JiajunGuo1027/Soft-Glove-Dissertation/data/raw/flex_sensor/ind0/plot_sensors_20250812_154303.png

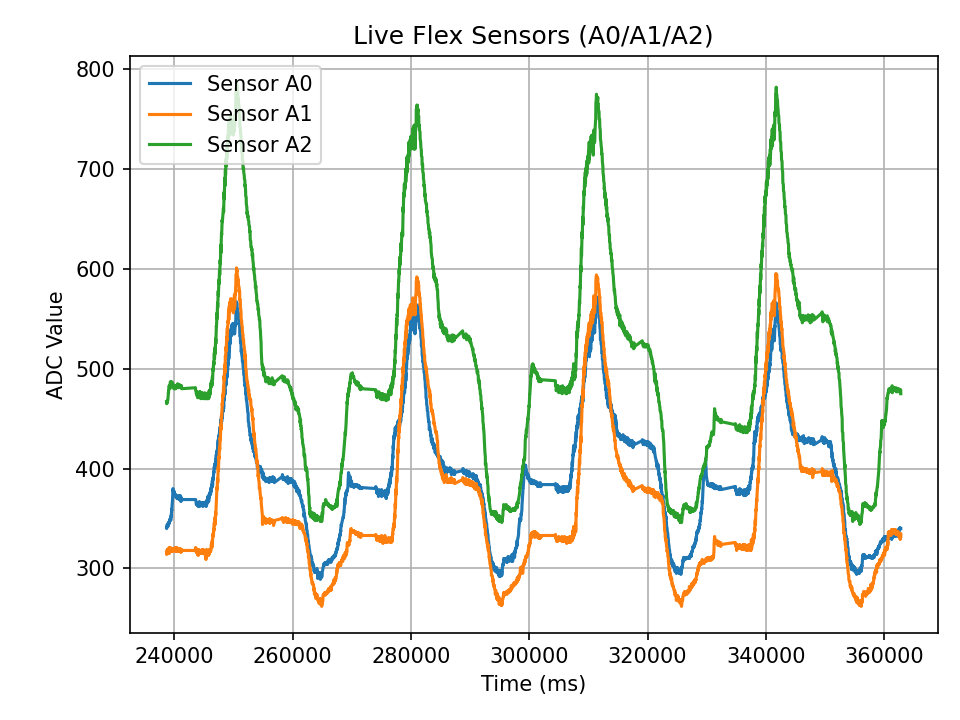
data/raw/flex_sensor/ind0/plot_sensors_20250812_154303.png
