JiajunGuo1027/Soft-Glove-Dissertation/data/raw/flex_sensor/ind1/plot_sensors_full_20250812_160008.png

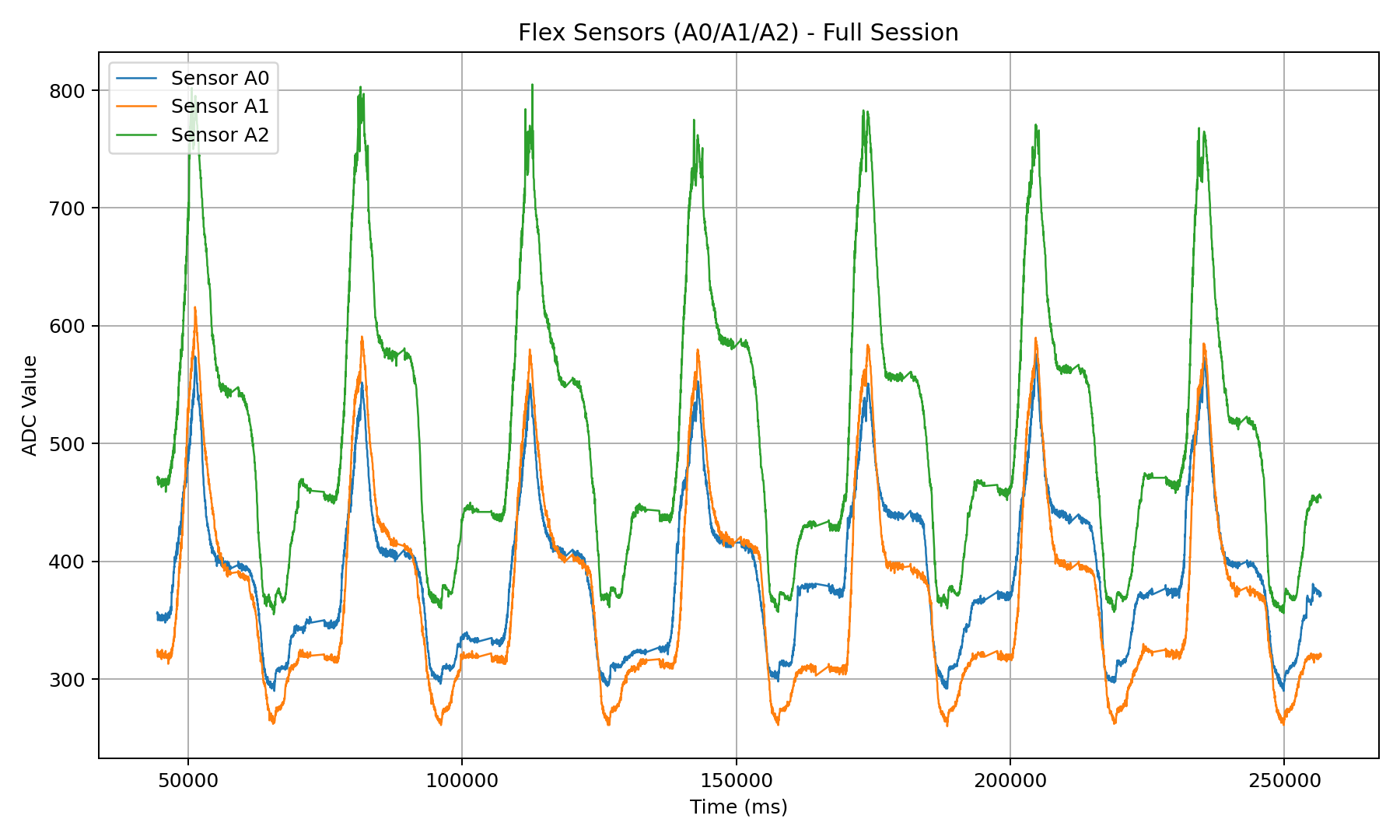
data/raw/flex_sensor/ind1/plot_sensors_full_20250812_160008.png
