JiajunGuo1027/Soft-Glove-Dissertation/data/raw/flex_sensor/ind2/plot_motors_20250812_160704.png

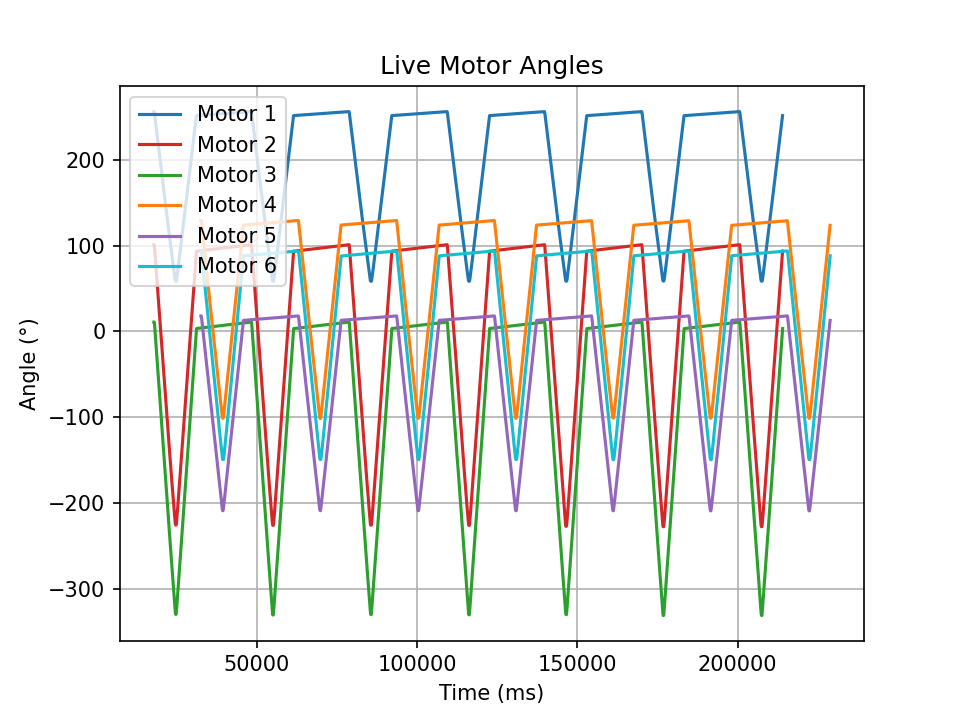
data/raw/flex_sensor/ind2/plot_motors_20250812_160704.png
