JiajunGuo1027/Soft-Glove-Dissertation/data/raw/flex_sensor/mid1/plot_sensors_20250812_162041.png

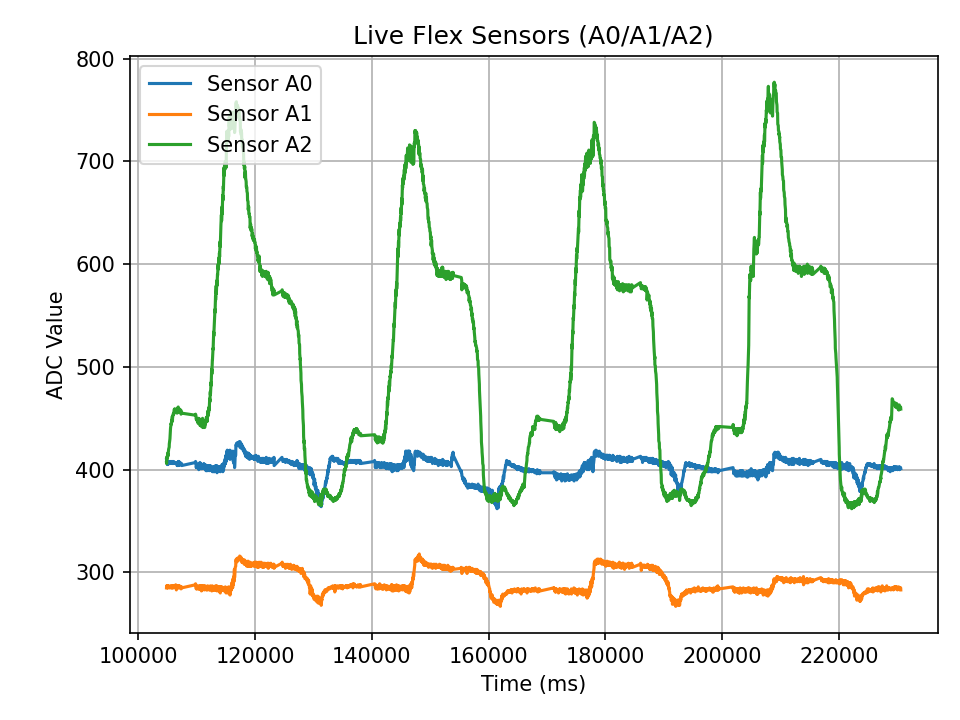
data/raw/flex_sensor/mid1/plot_sensors_20250812_162041.png
