JiajunGuo1027/Soft-Glove-Dissertation/data/raw/flex_sensor/mid2/plot_sensors_full_20250812_163051.png

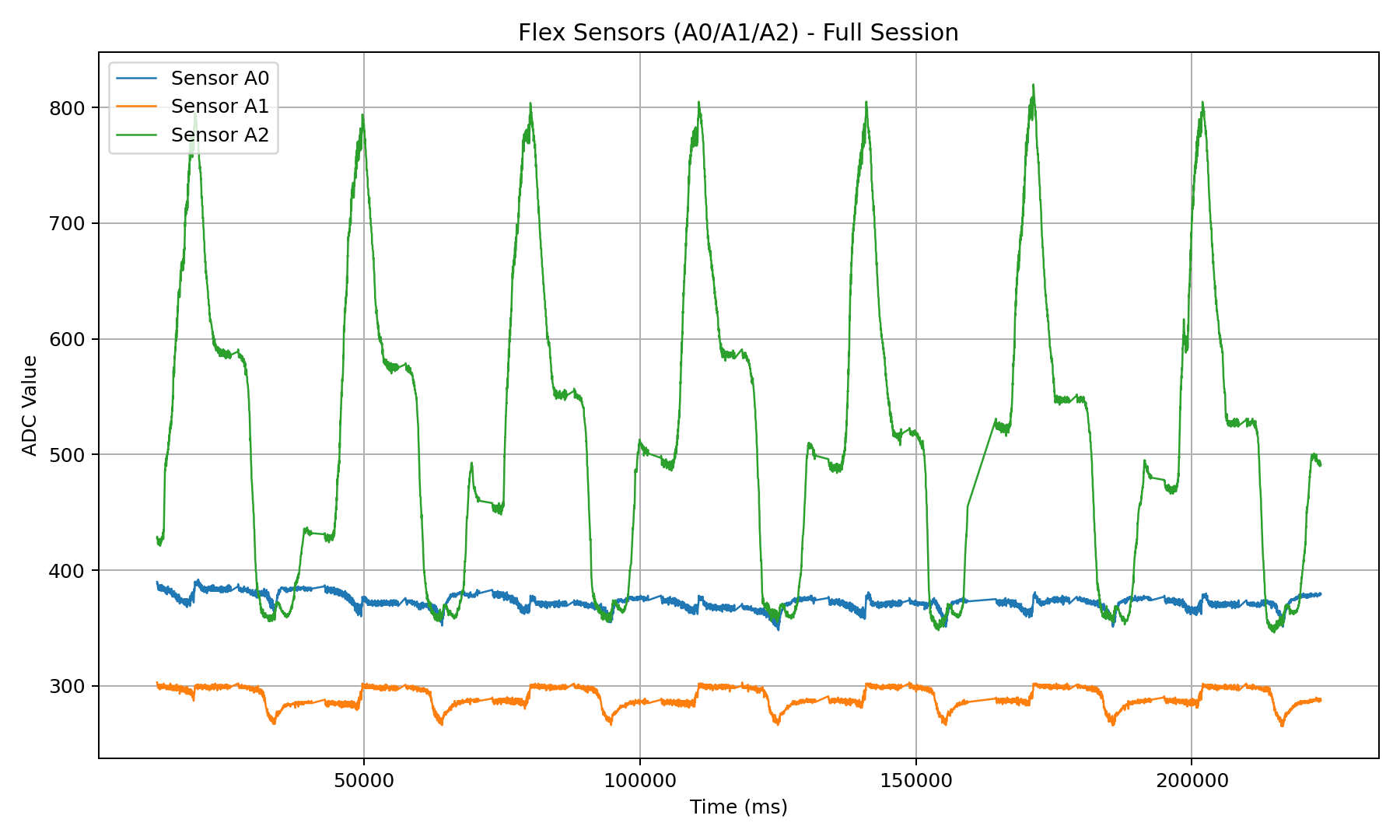
data/raw/flex_sensor/mid2/plot_sensors_full_20250812_163051.png
