JiajunGuo1027/Soft-Glove-Dissertation/data/raw/flex_sensor/plot_sensors_20250809_205605.png

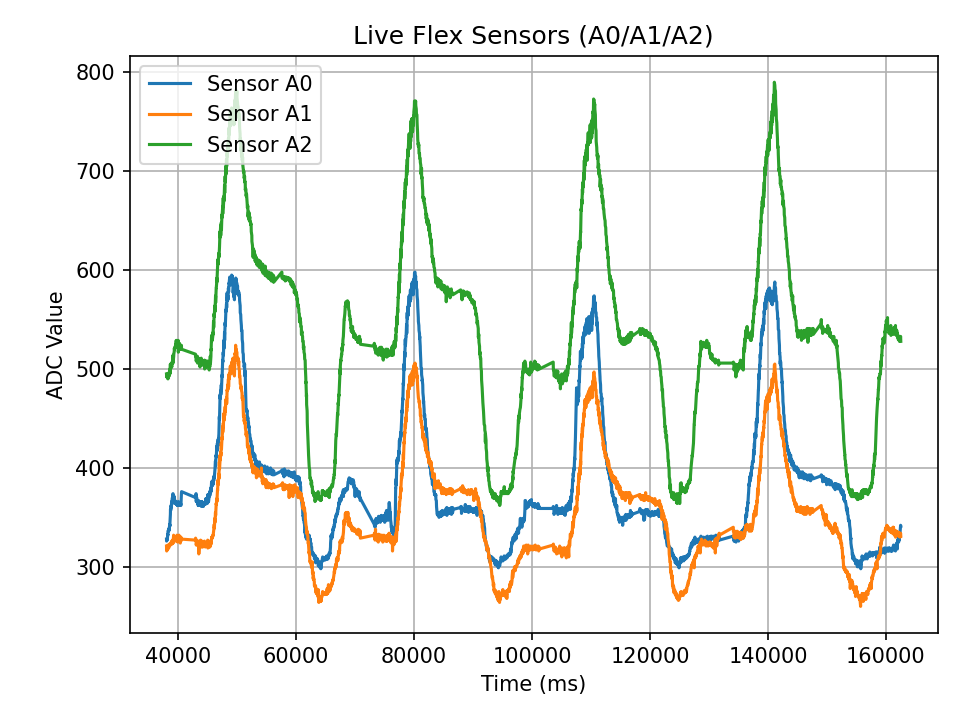
data/raw/flex_sensor/plot_sensors_20250809_205605.png
