JiajunGuo1027/Soft-Glove-Dissertation/data/raw/flex_sensor/plot_sensors_20250809_210135.png

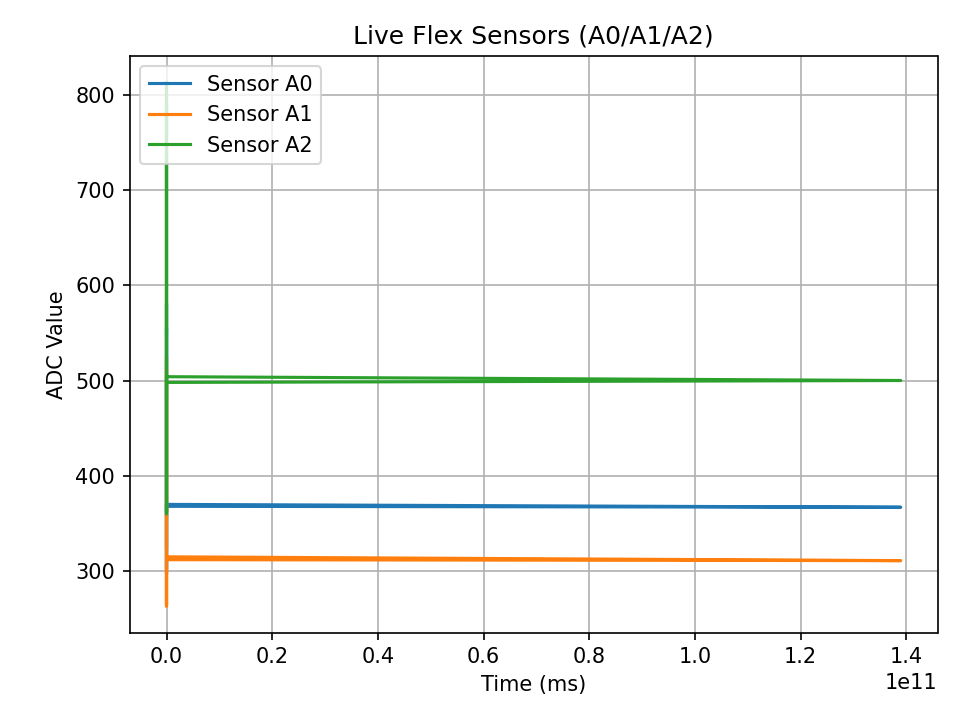
data/raw/flex_sensor/plot_sensors_20250809_210135.png
