JiajunGuo1027/Soft-Glove-Dissertation/data/raw/flex_sensor/thu1/plot_sensors_full_20250812_171734.png

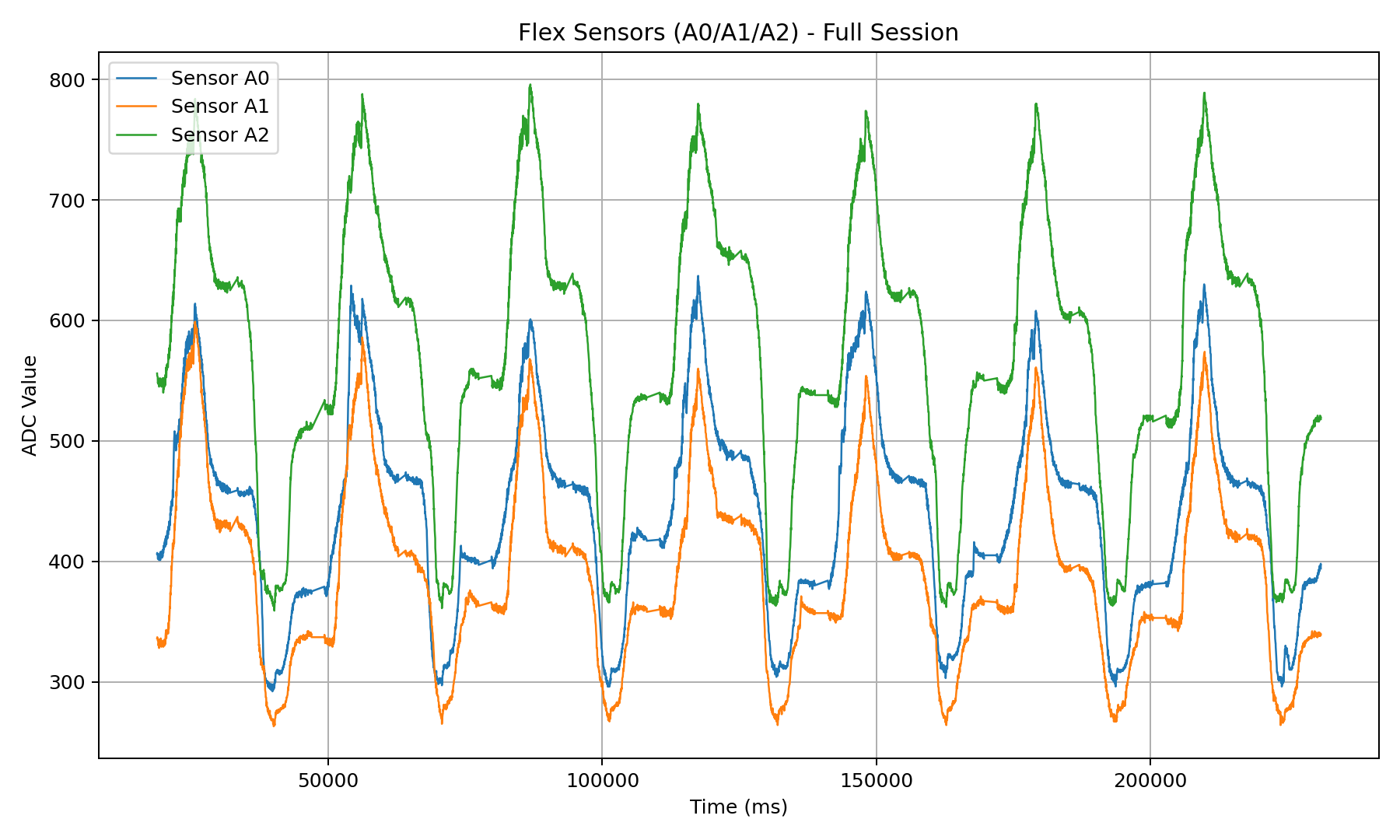
data/raw/flex_sensor/thu1/plot_sensors_full_20250812_171734.png
