JiajunGuo1027/Soft-Glove-Dissertation/data/raw/flex_sensor/thu2/plot_sensors_20250812_172157.png

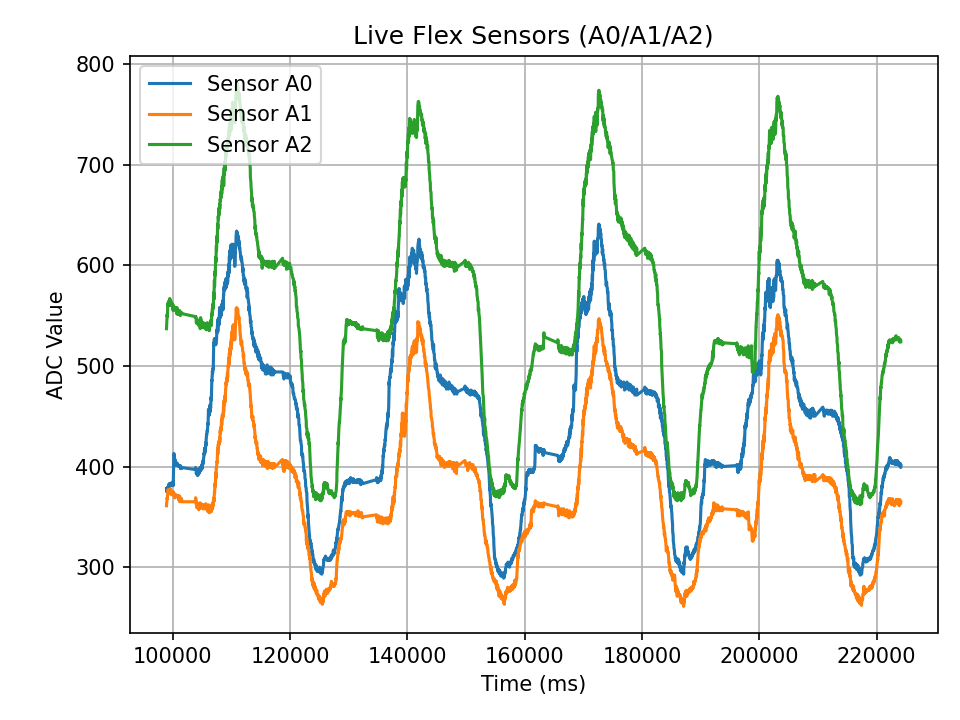
data/raw/flex_sensor/thu2/plot_sensors_20250812_172157.png
