JiajunGuo1027/Soft-Glove-Dissertation/data/raw/Index/0/Figure_ind0.png

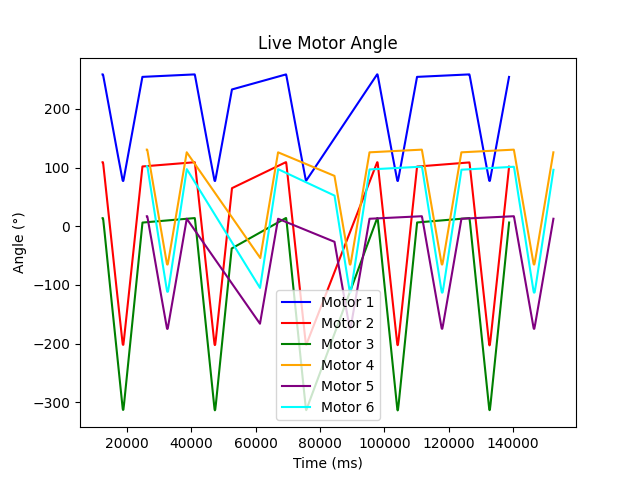
data/raw/Index/0/Figure_ind0.png
