JiajunGuo1027/Soft-Glove-Dissertation/data/raw/Index/0/Figure_ind01.png

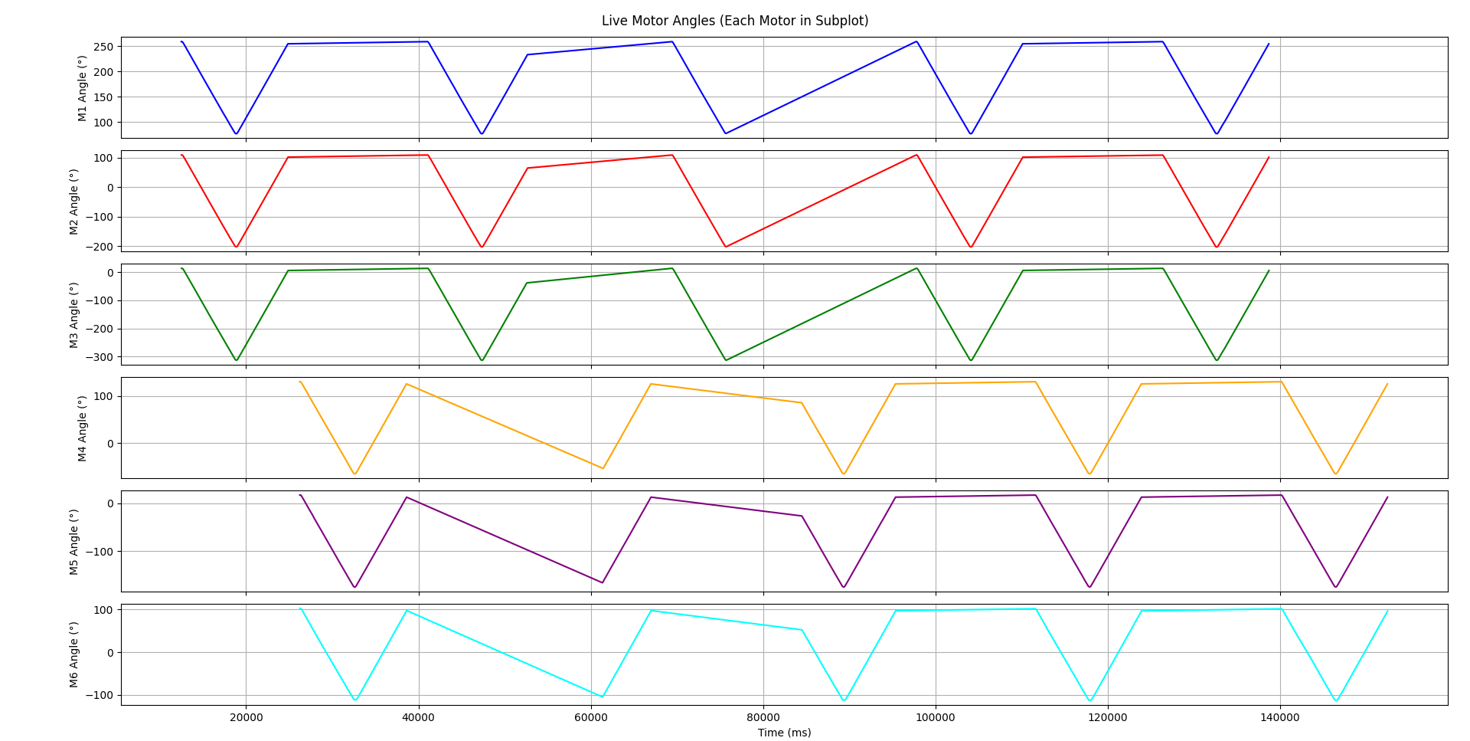
data/raw/Index/0/Figure_ind01.png
