JiajunGuo1027/Soft-Glove-Dissertation/data/raw/Index/2/Figure_ind2.png

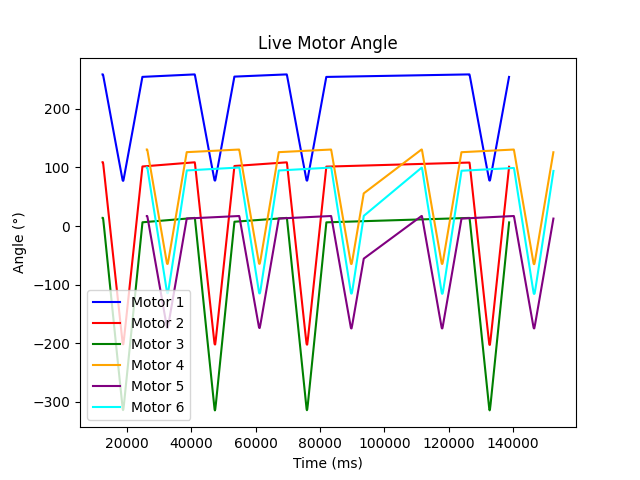
data/raw/Index/2/Figure_ind2.png
