JiajunGuo1027/Soft-Glove-Dissertation/data/raw/Index/2/Figure_ind21.png

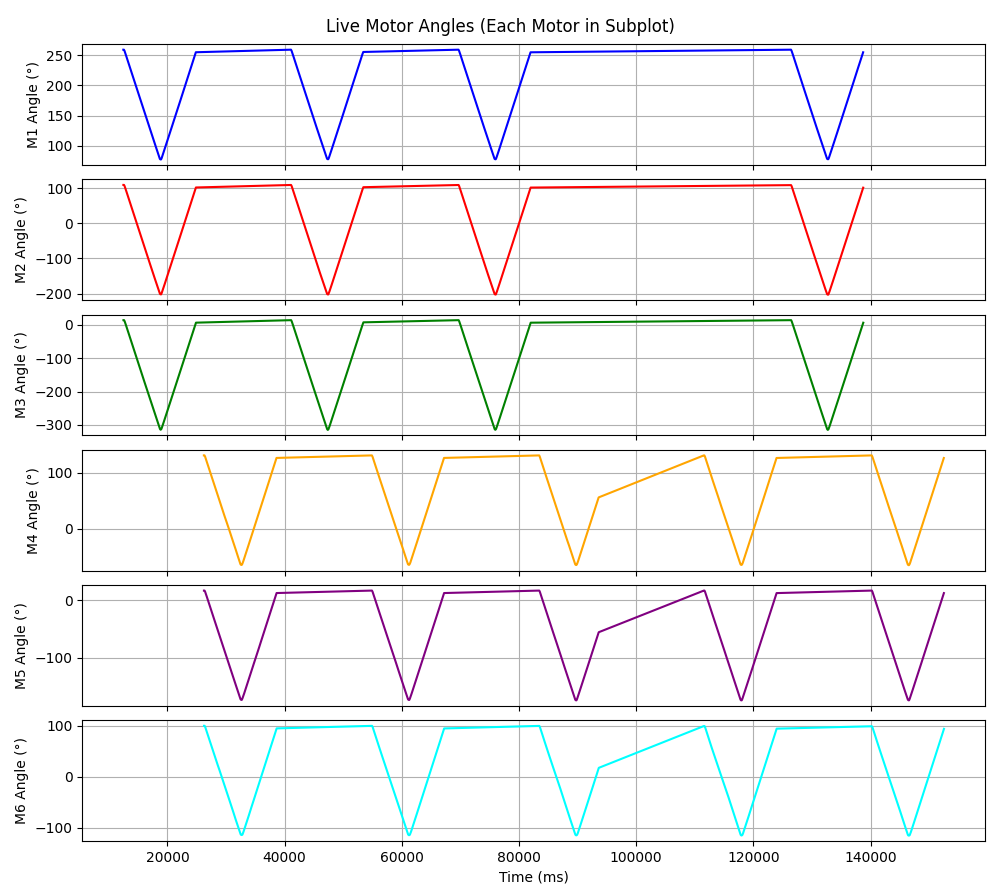
data/raw/Index/2/Figure_ind21.png
