JiajunGuo1027/Soft-Glove-Dissertation/data/raw/Middle/1/Figure_mid1.png

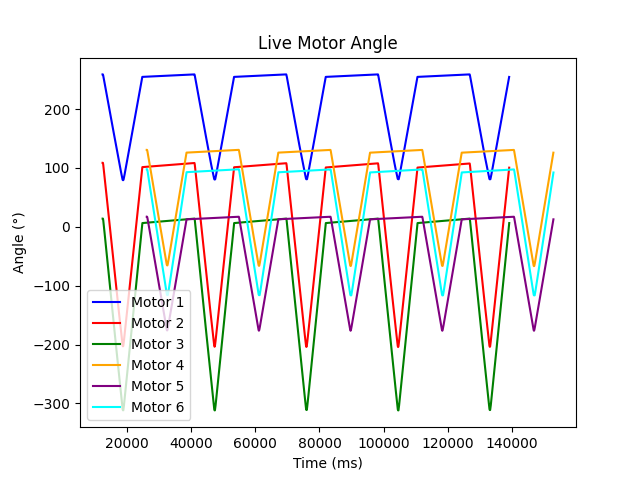
data/raw/Middle/1/Figure_mid1.png
