JiajunGuo1027/Soft-Glove-Dissertation/data/raw/Middle/2/Figure_mid2.png

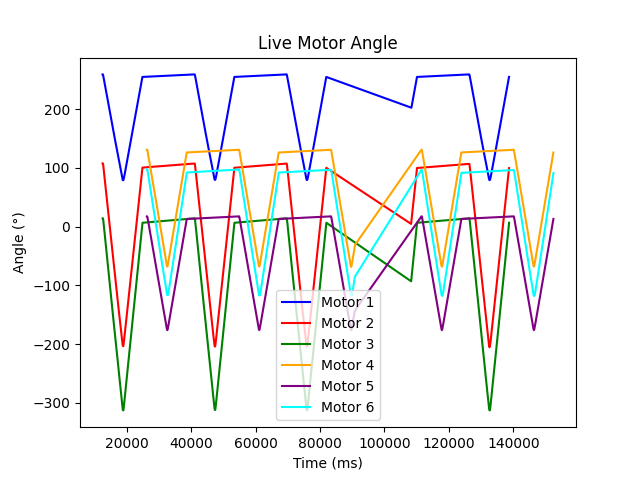
data/raw/Middle/2/Figure_mid2.png
