JiajunGuo1027/Soft-Glove-Dissertation/data/raw/Middle/2/Figure_mid21.png

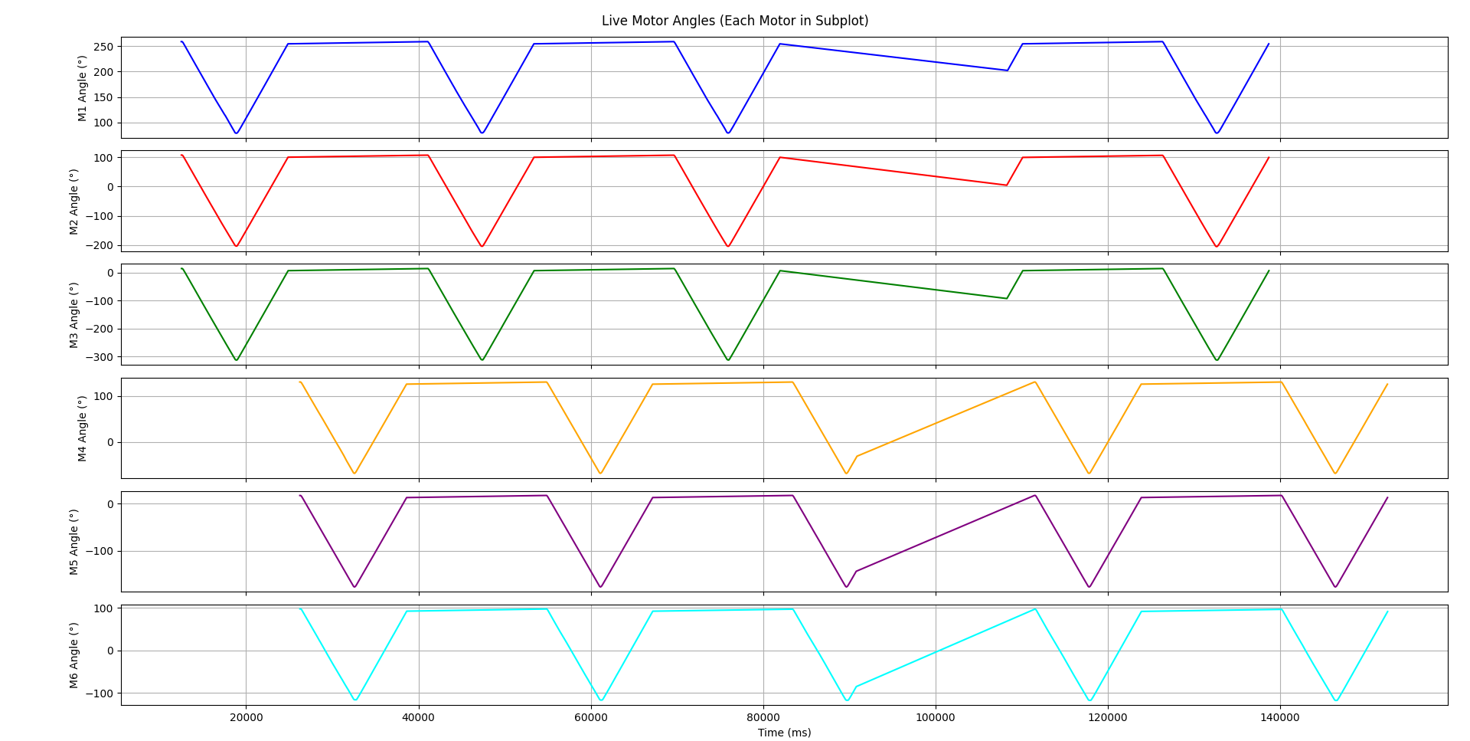
data/raw/Middle/2/Figure_mid21.png
