JiajunGuo1027/Soft-Glove-Dissertation/data/raw/Thumb/1/Figure_thu11.png

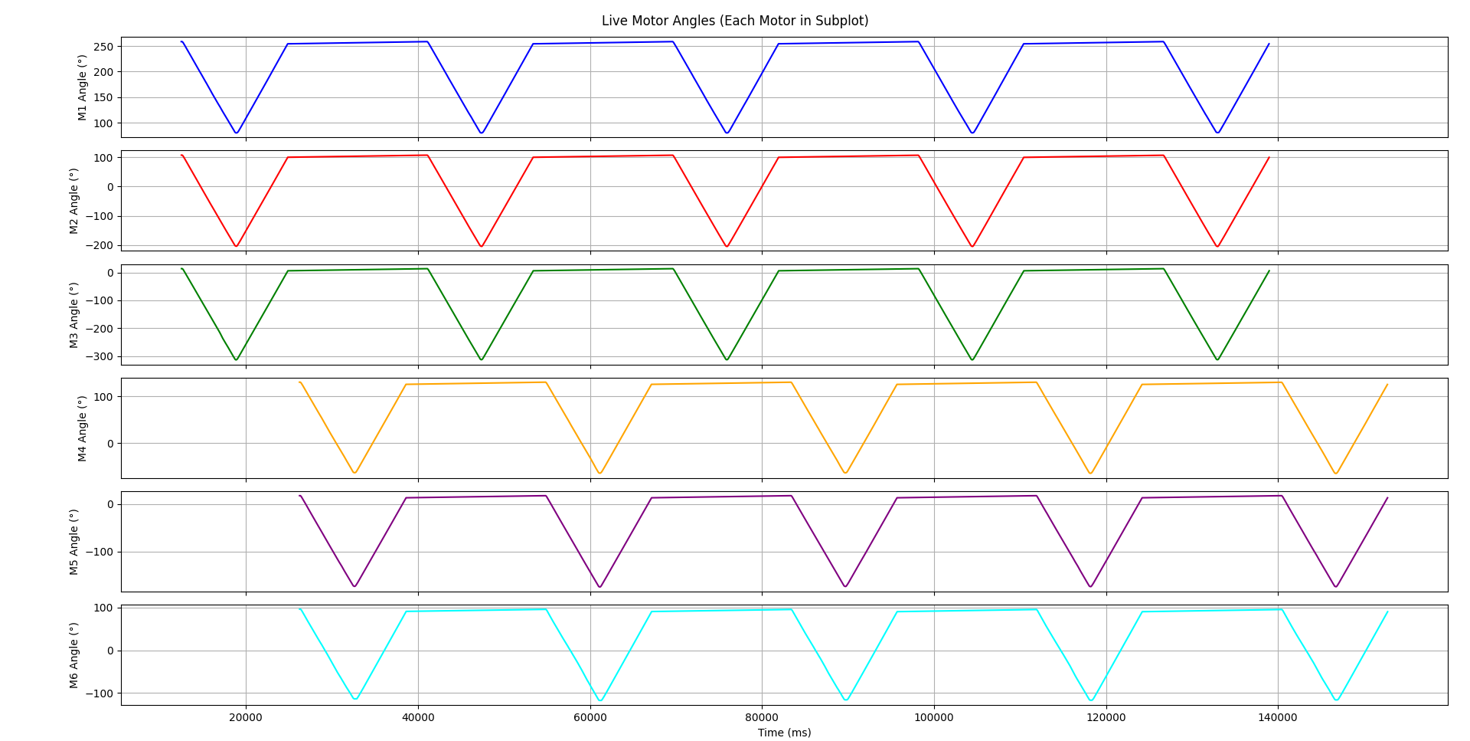
data/raw/Thumb/1/Figure_thu11.png
