JiajunGuo1027/Soft-Glove-Dissertation/data/raw/Thumb/2/Figure_thu2.png

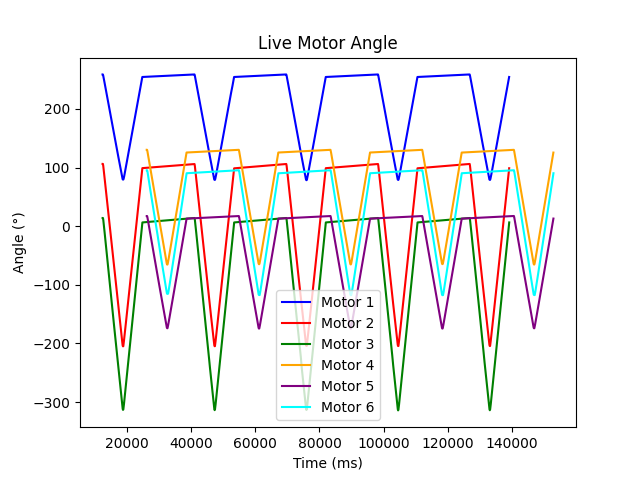
data/raw/Thumb/2/Figure_thu2.png
