JiajunGuo1027/Soft-Glove-Dissertation/images/article/aluminum.jpg

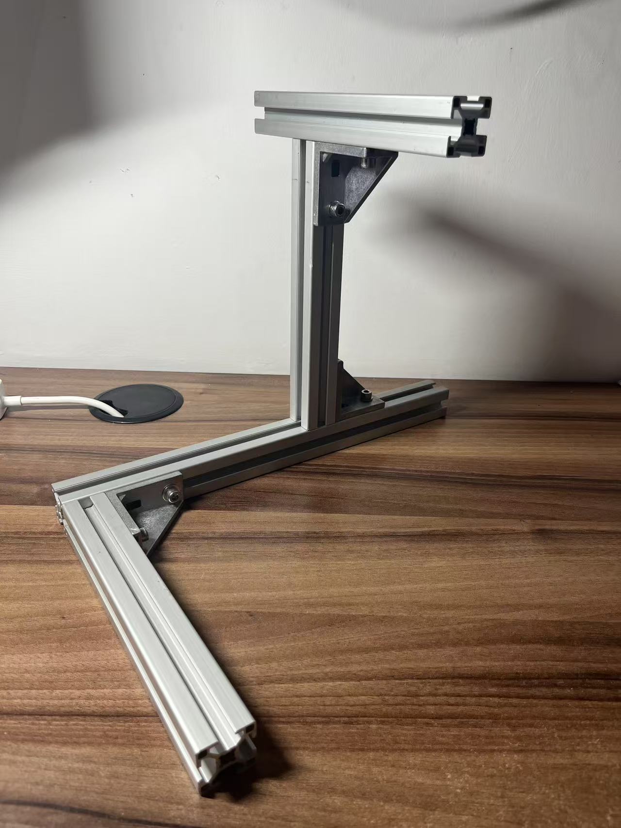
images/article/aluminum.jpg
