JiajunGuo1027/Soft-Glove-Dissertation/images/article/anagle_detect.jpg

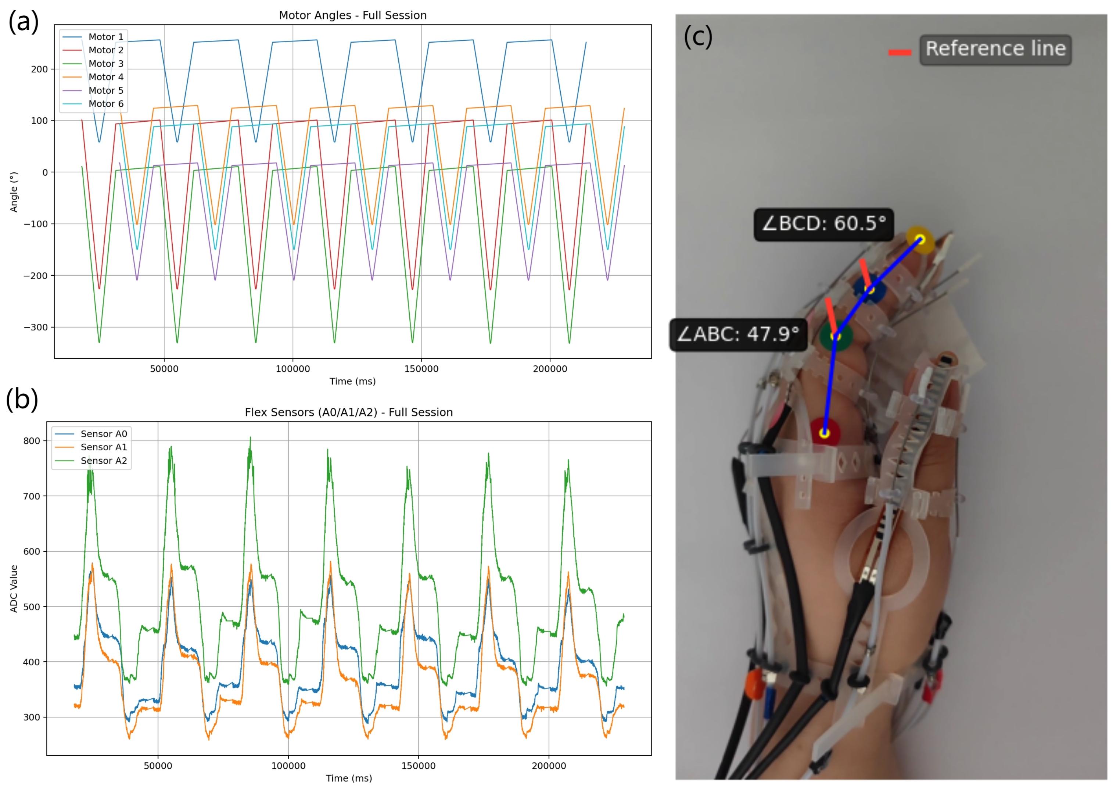
images/article/anagle_detect.jpg
