JiajunGuo1027/Soft-Glove-Dissertation/images/article/cable_connector.png

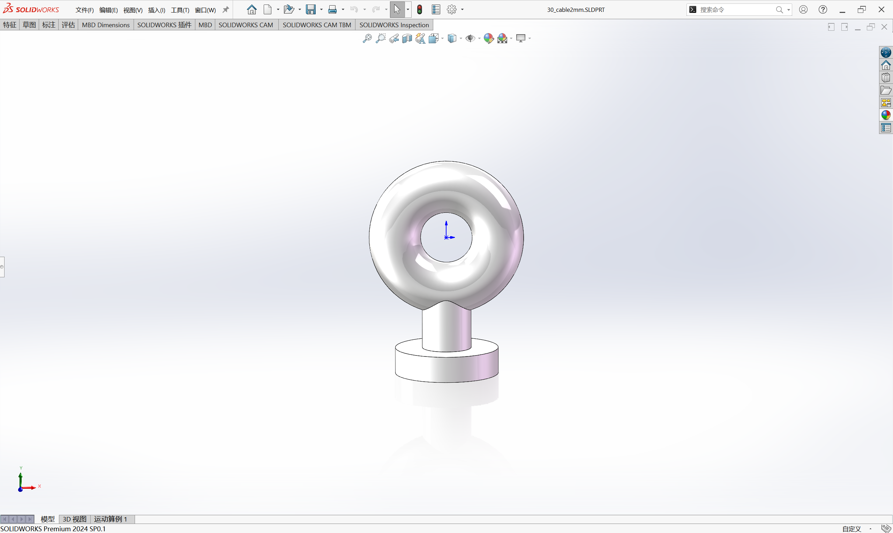
images/article/cable_connector.png
