JiajunGuo1027/Soft-Glove-Dissertation/images/article/connector.png

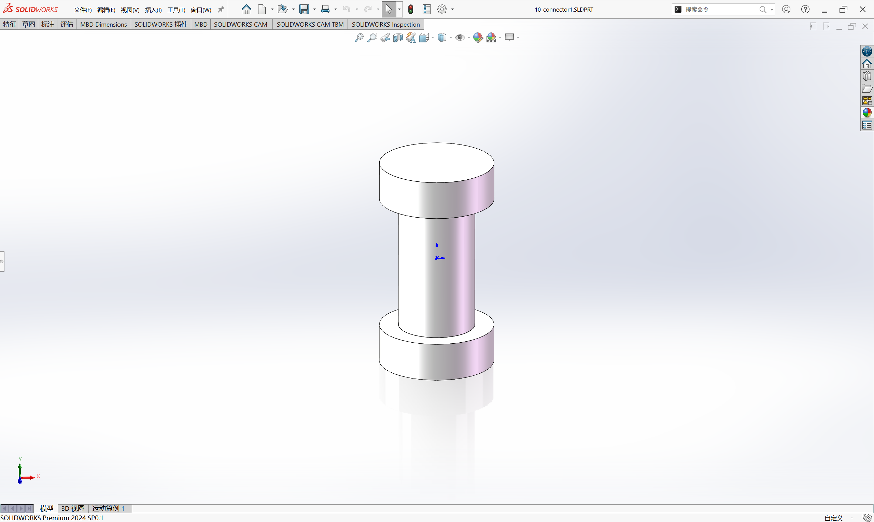
images/article/connector.png
