JiajunGuo1027/Soft-Glove-Dissertation/images/article/control_flowchart1.png

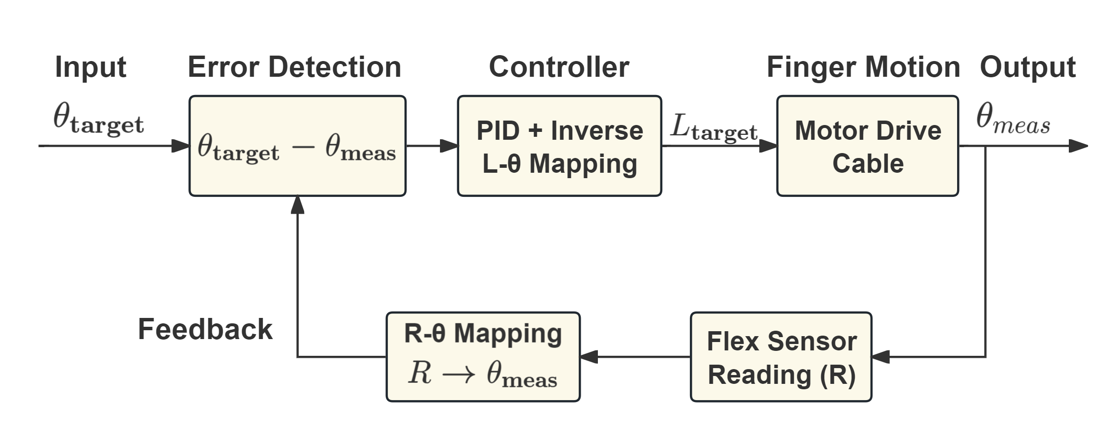
images/article/control_flowchart1.png
