JiajunGuo1027/Soft-Glove-Dissertation/images/article/control_flowchart.png

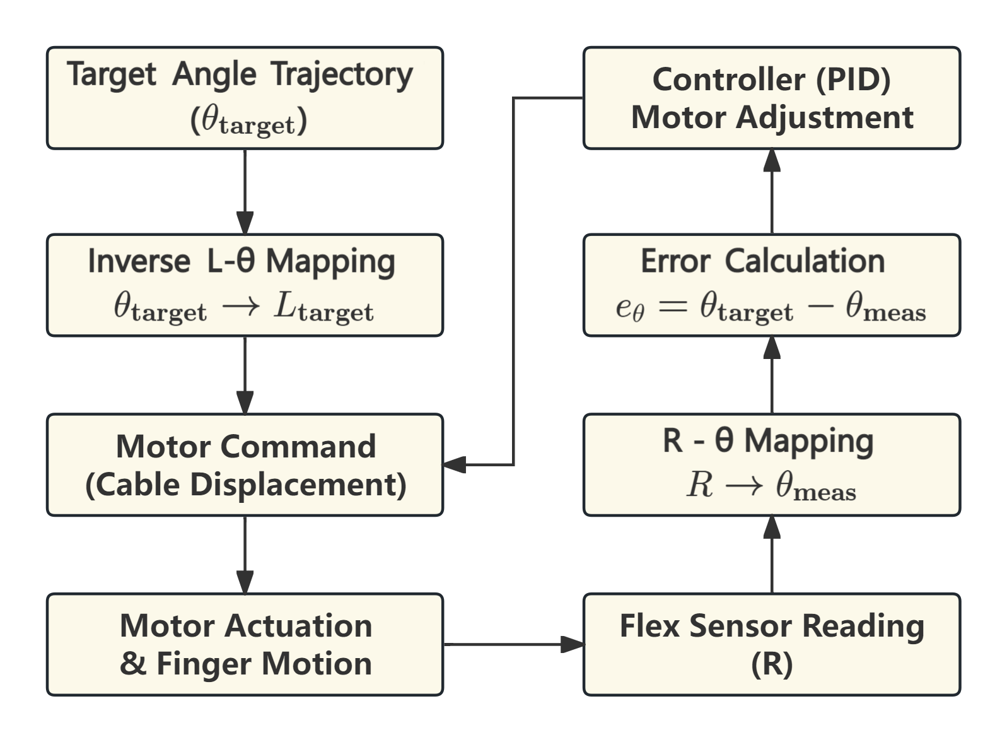
images/article/control_flowchart.png
