JiajunGuo1027/Soft-Glove-Dissertation/images/article/finger_lower.png

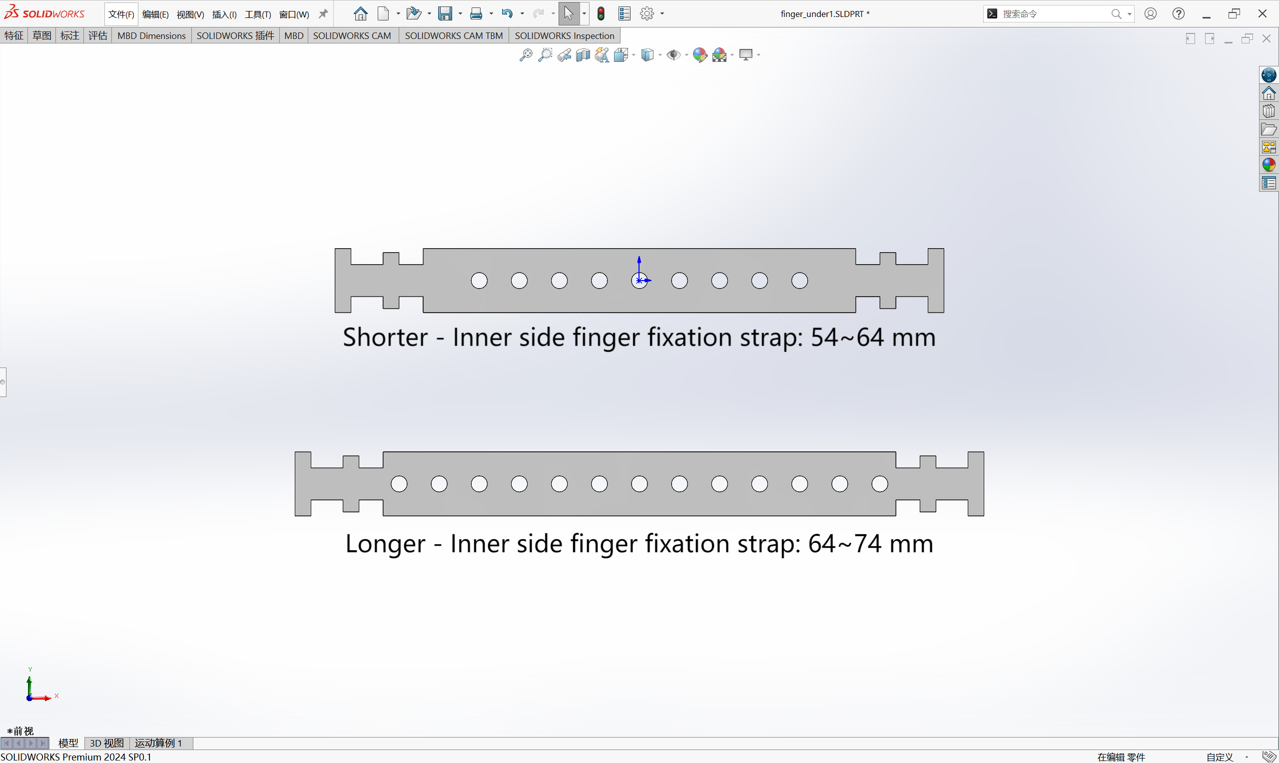
images/article/finger_lower.png
