JiajunGuo1027/Soft-Glove-Dissertation/images/article/finger_lower_sketch1.png

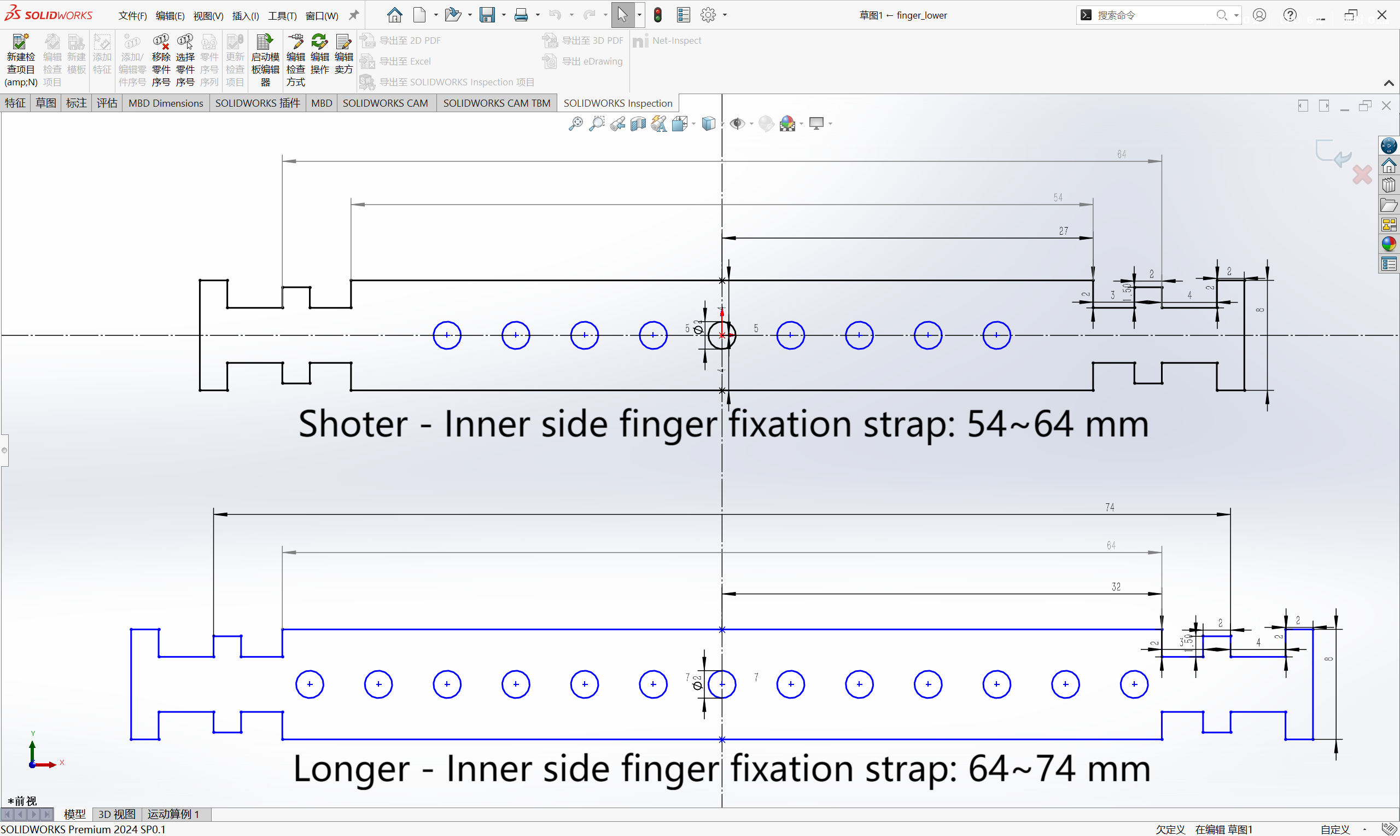
images/article/finger_lower_sketch1.png
