JiajunGuo1027/Soft-Glove-Dissertation/images/article/fingers_design.jpg

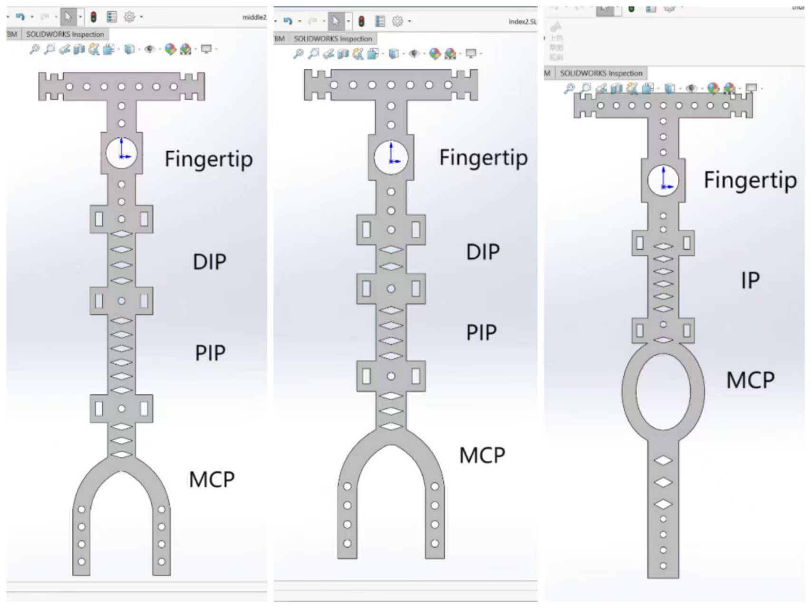
images/article/fingers_design.jpg
