JiajunGuo1027/Soft-Glove-Dissertation/images/article/glove_connector.jpg

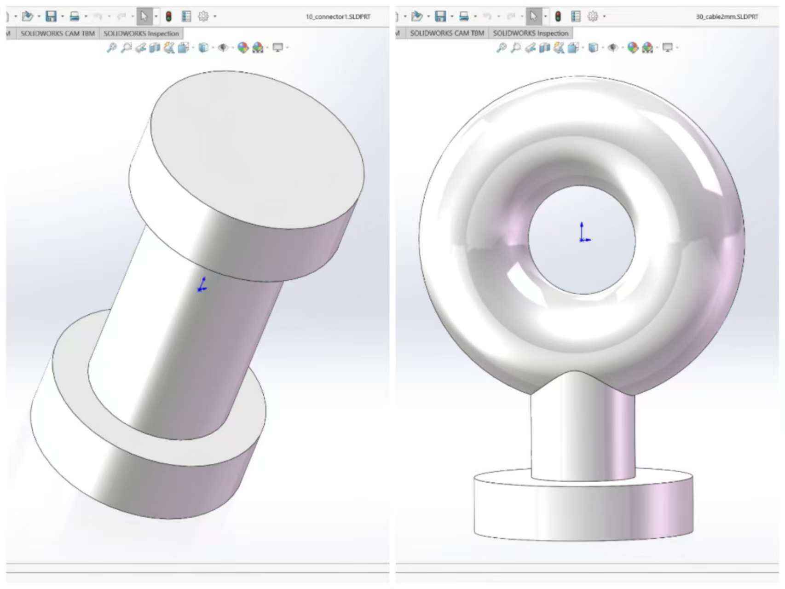
images/article/glove_connector.jpg
