JiajunGuo1027/Soft-Glove-Dissertation/images/article/glove_wearing.jpg

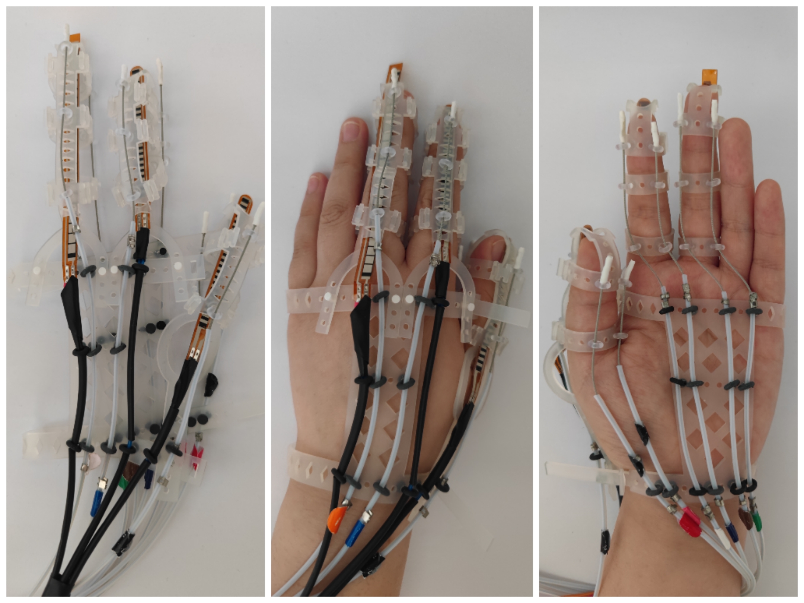
images/article/glove_wearing.jpg
