JiajunGuo1027/Soft-Glove-Dissertation/images/article/index_upper.png

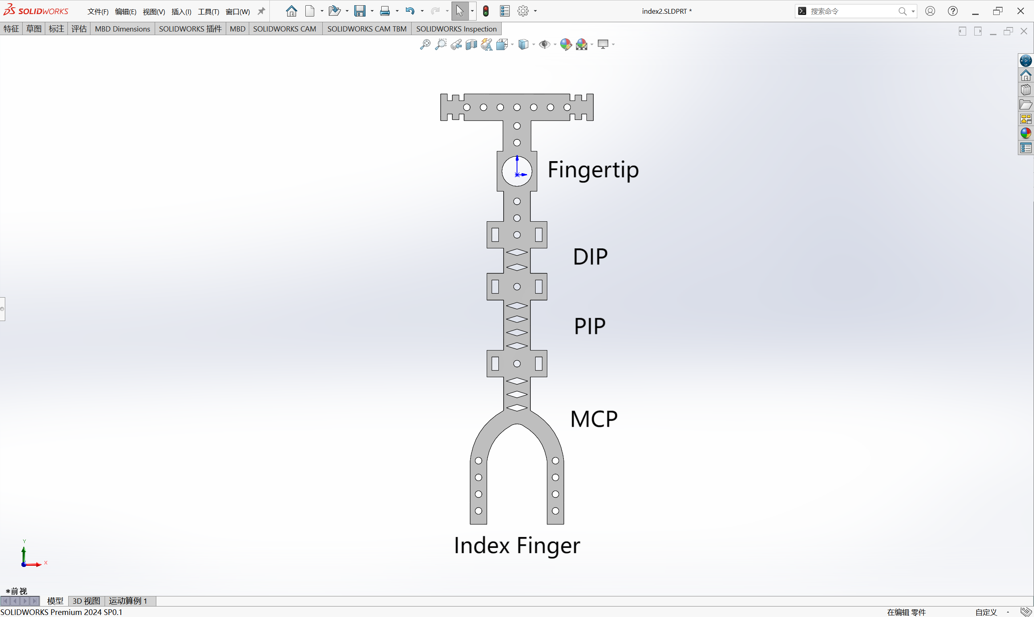
images/article/index_upper.png
