JiajunGuo1027/Soft-Glove-Dissertation/images/article/motor_sensors.jpg

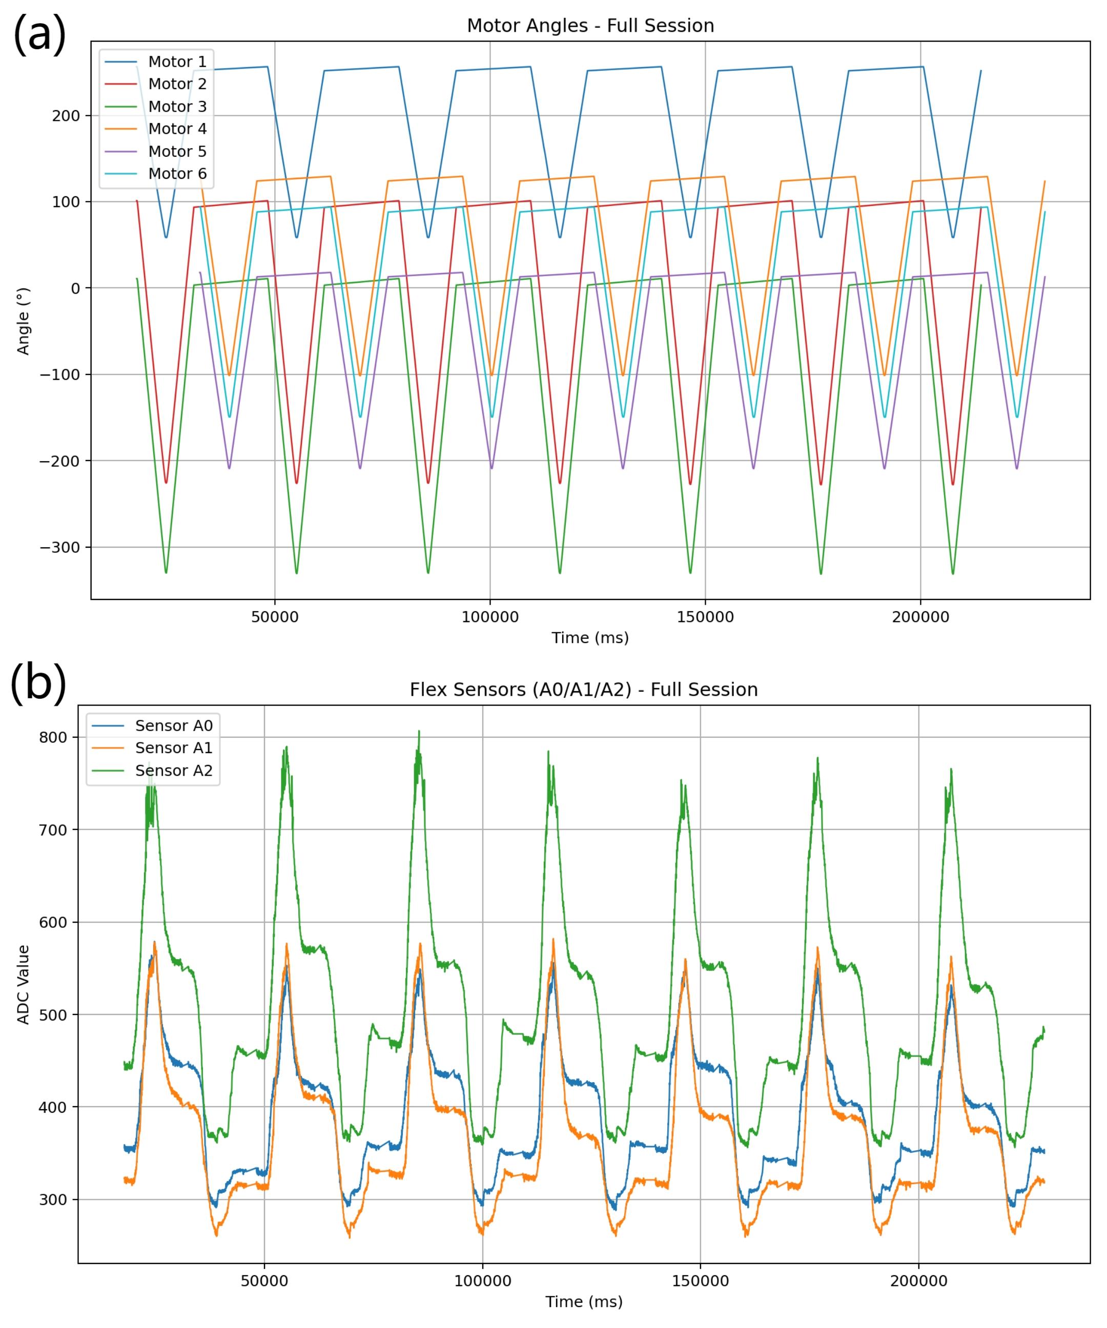
images/article/motor_sensors.jpg
