JiajunGuo1027/Soft-Glove-Dissertation/images/article/Overall_flowchart.png

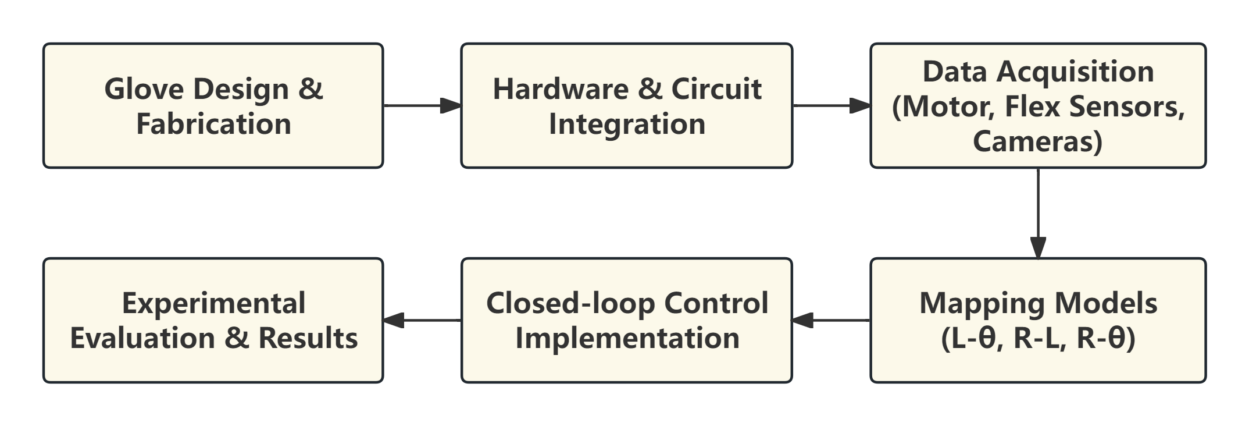
images/article/Overall_flowchart.png
