JiajunGuo1027/Soft-Glove-Dissertation/images/article/palm1.png

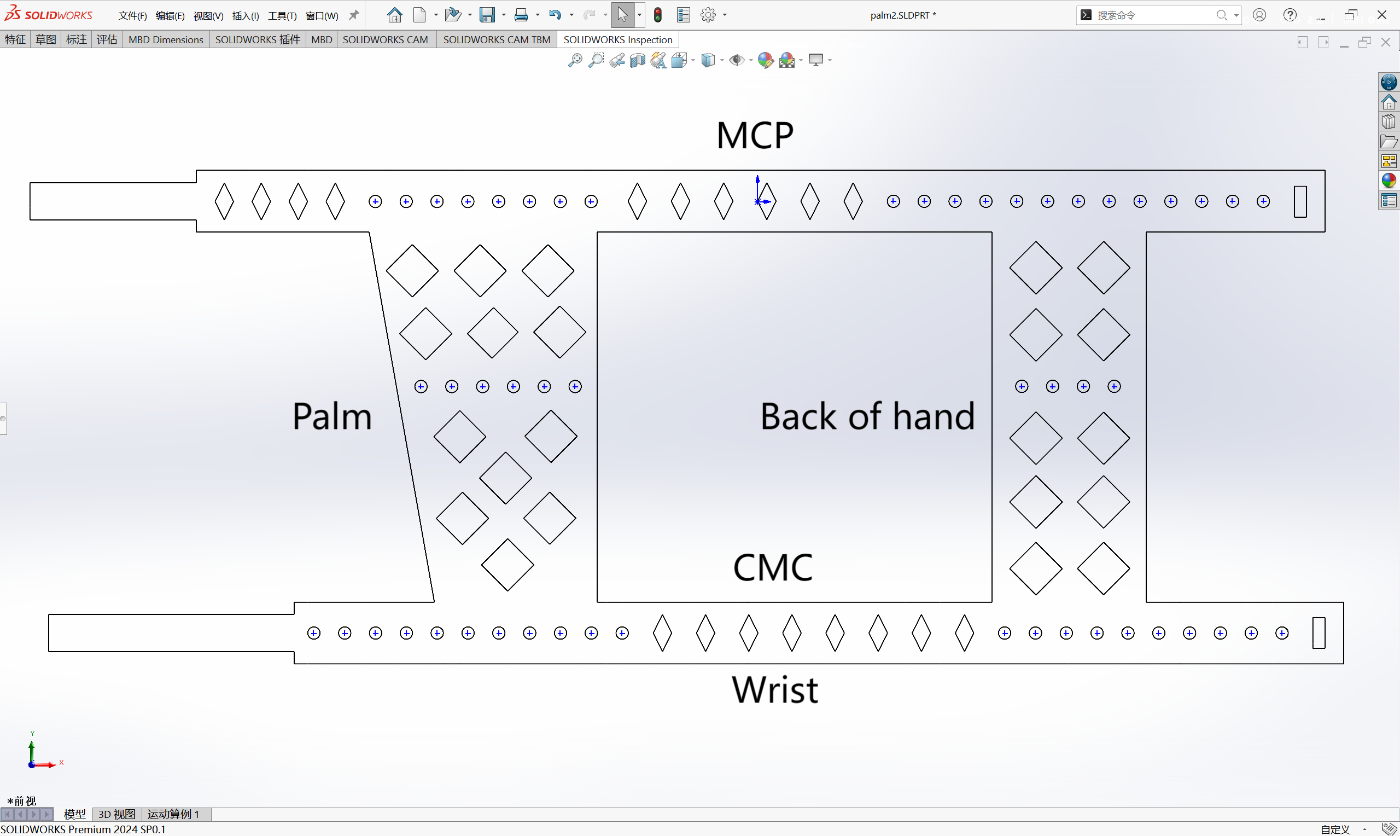
images/article/palm1.png
