JiajunGuo1027/Soft-Glove-Dissertation/images/article/palm.png

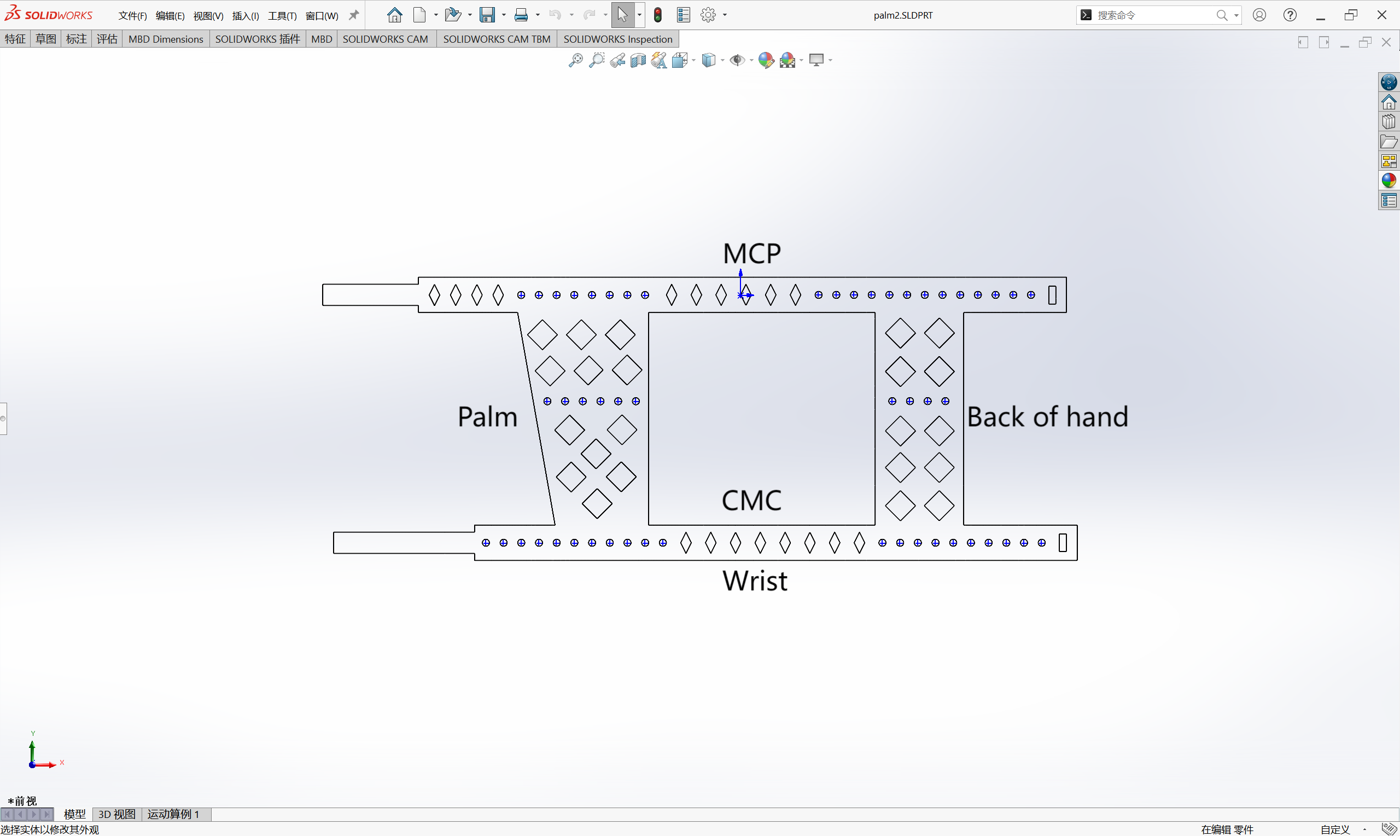
images/article/palm.png
