JiajunGuo1027/Soft-Glove-Dissertation/images/article/R_L1.jpg

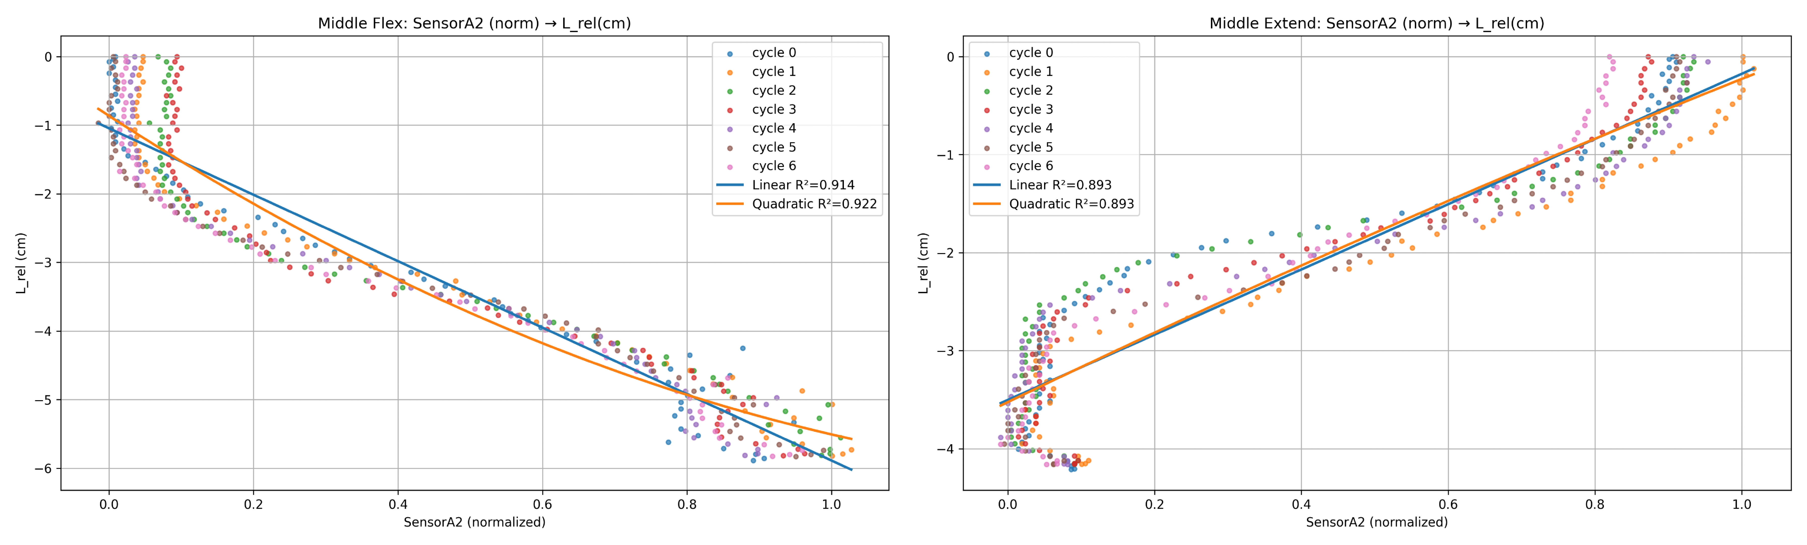
images/article/R_L1.jpg
