JiajunGuo1027/Soft-Glove-Dissertation/images/article/R_L2.jpg

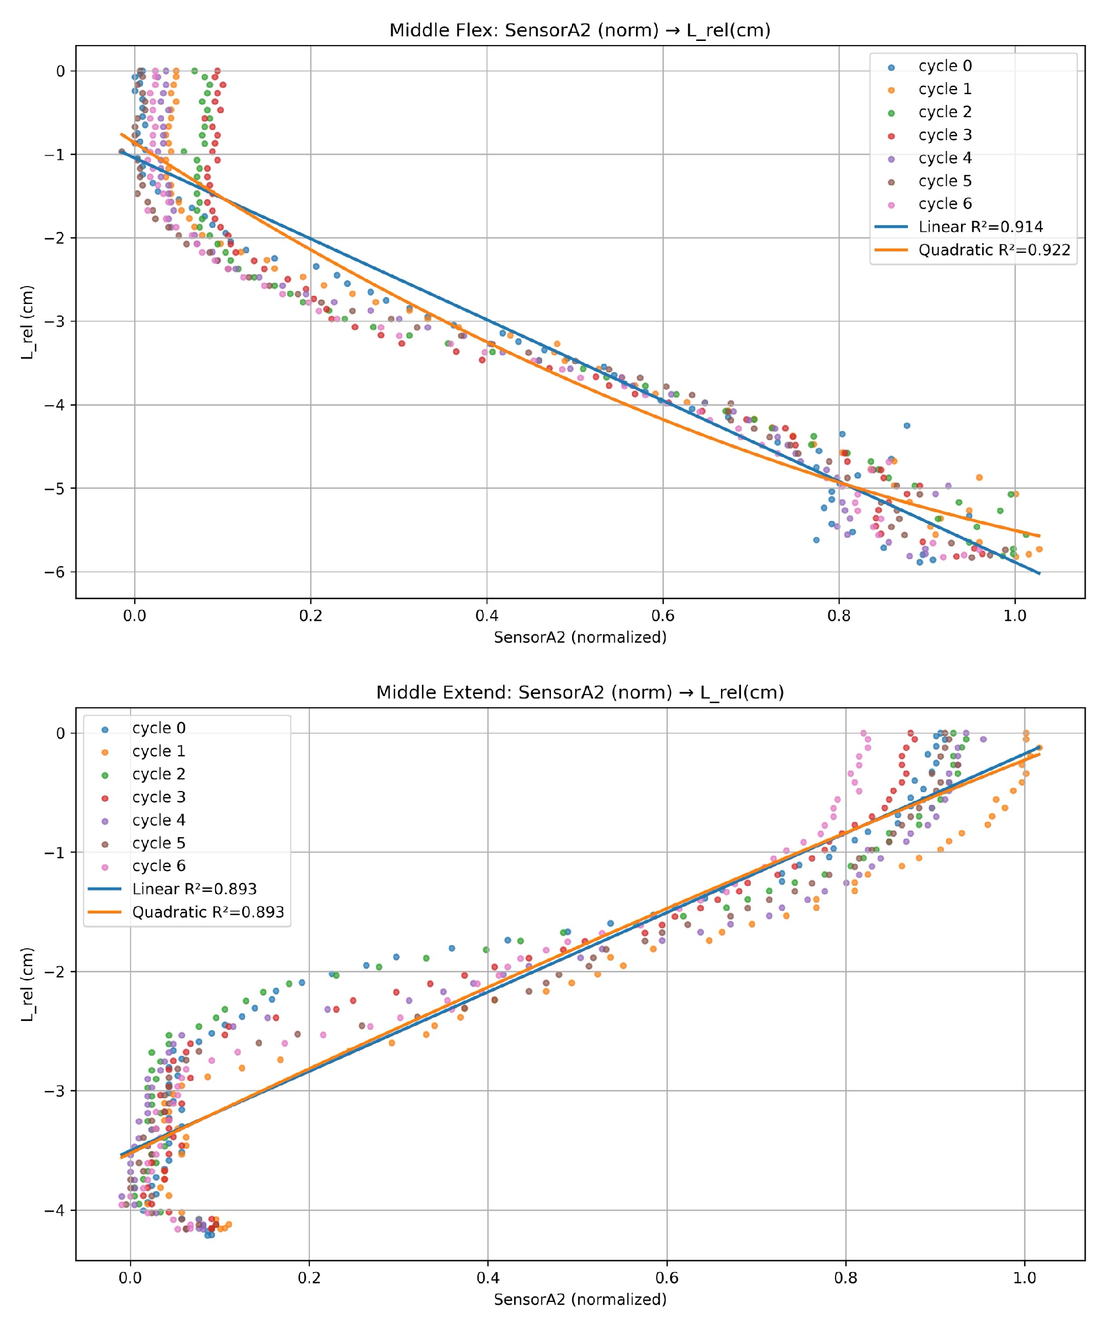
images/article/R_L2.jpg
