JiajunGuo1027/Soft-Glove-Dissertation/images/article/Raw data acquisition1.jpg

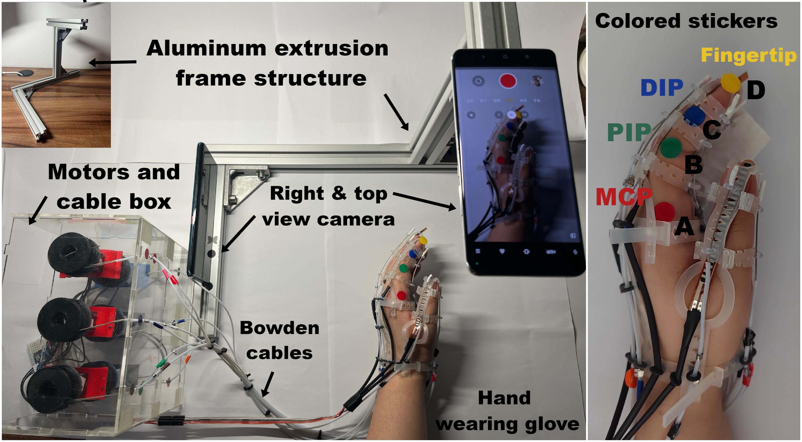
images/article/Raw data acquisition1.jpg
