JiajunGuo1027/Soft-Glove-Dissertation/images/article/Raw data acquisition.jpg

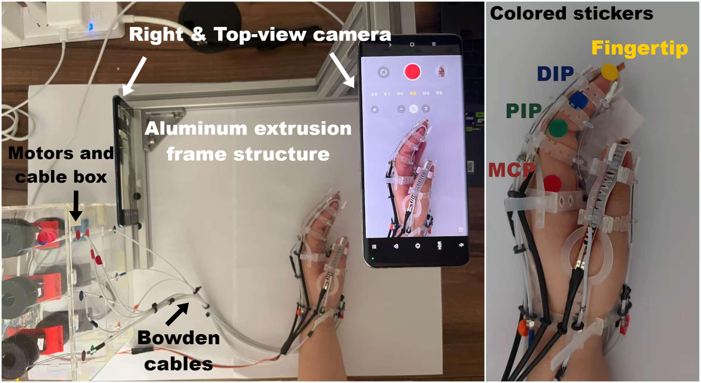
images/article/Raw data acquisition.jpg
