JiajunGuo1027/Soft-Glove-Dissertation/images/article/thumb.png

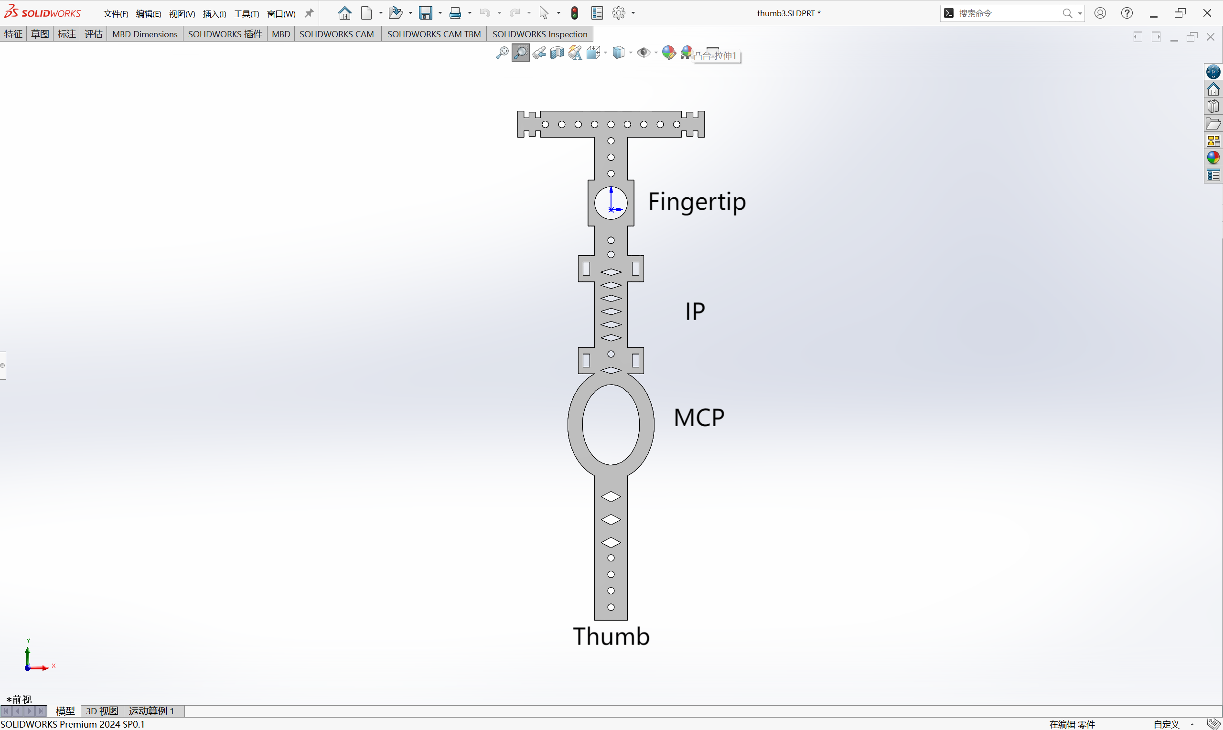
images/article/thumb.png
