JiajunGuo1027/Soft-Glove-Dissertation/images/article/visual.jpg

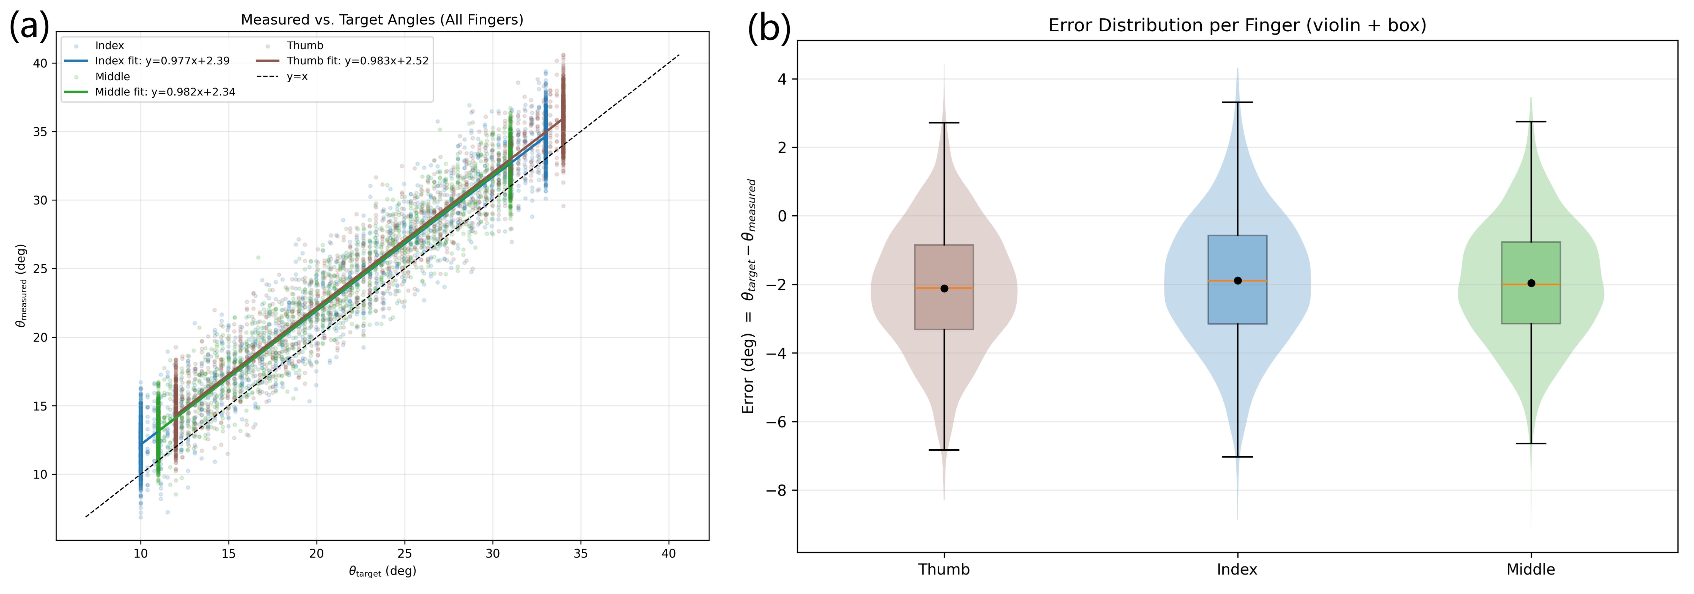
images/article/visual.jpg
