JiajunGuo1027/Soft-Glove-Dissertation/images/article/屏幕截图 2025-07-07 192710.png

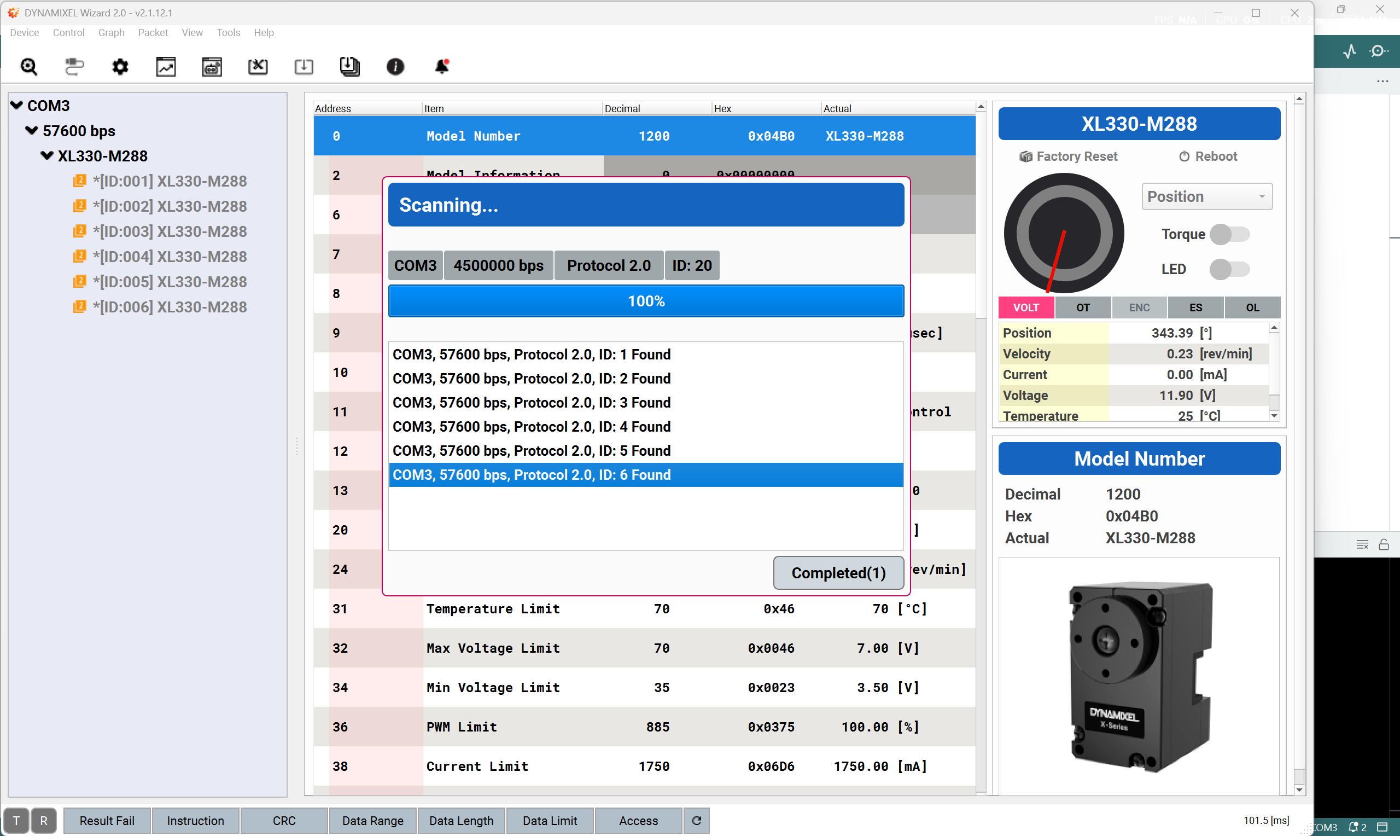
images/article/屏幕截图 2025-07-07 192710.png
