JiajunGuo1027/Soft-Glove-Dissertation/images/design_sketch/cable_connector.png

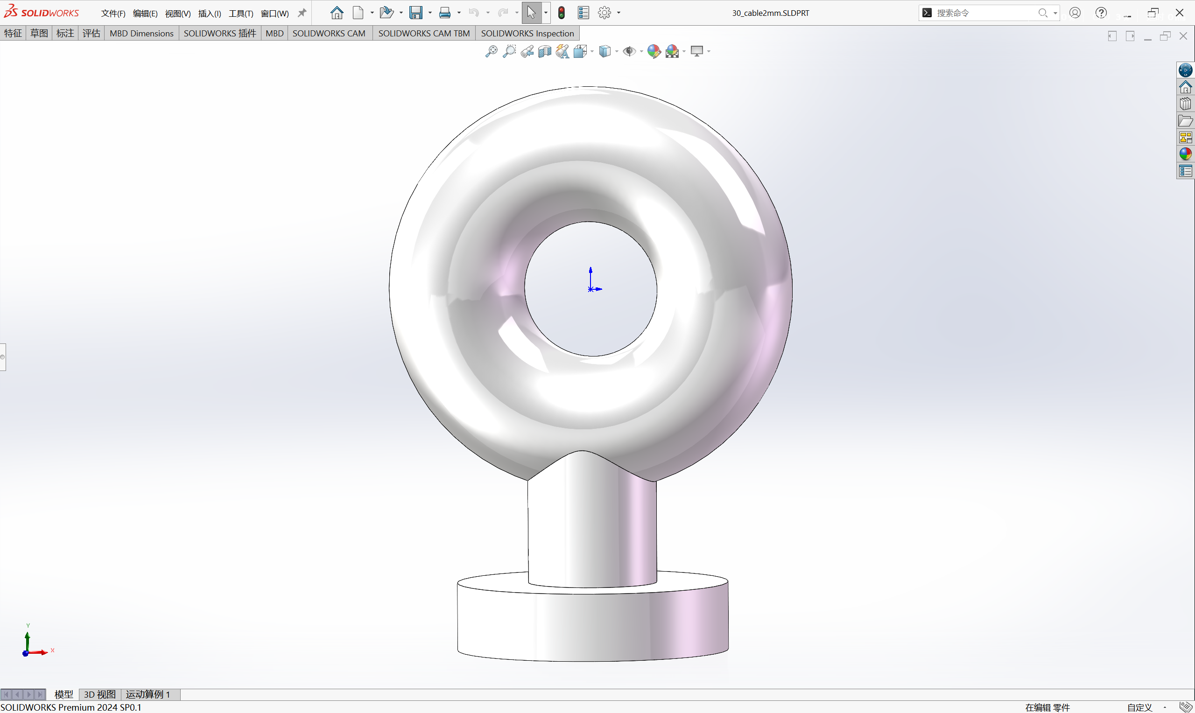
images/design_sketch/cable_connector.png
