JiajunGuo1027/Soft-Glove-Dissertation/images/design_sketch/connector.png

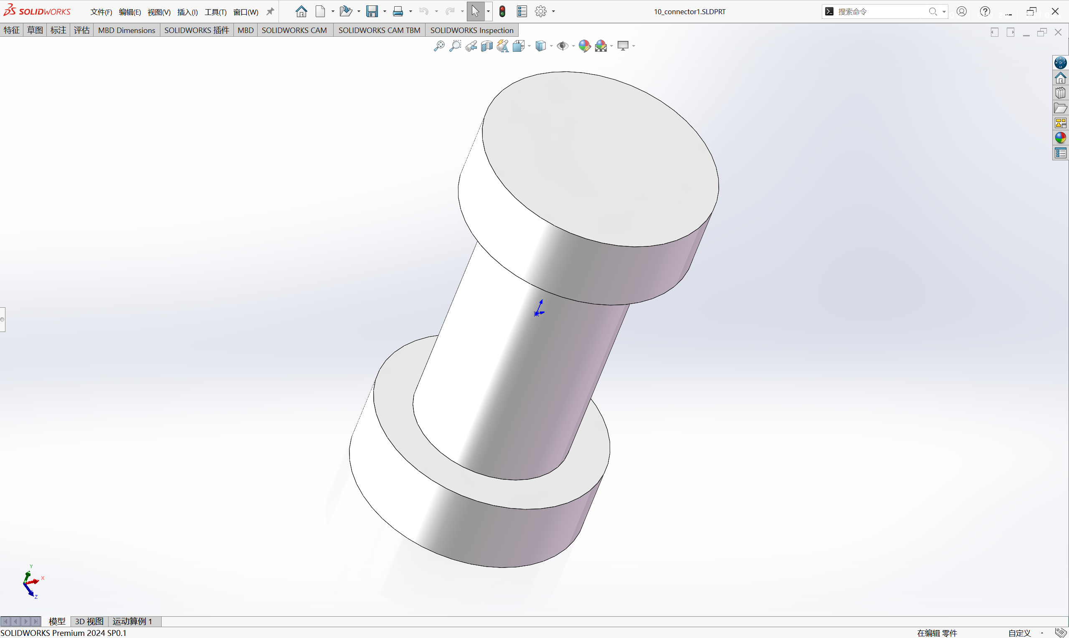
images/design_sketch/connector.png
