JiajunGuo1027/Soft-Glove-Dissertation/images/design_sketch/finger_lower.png

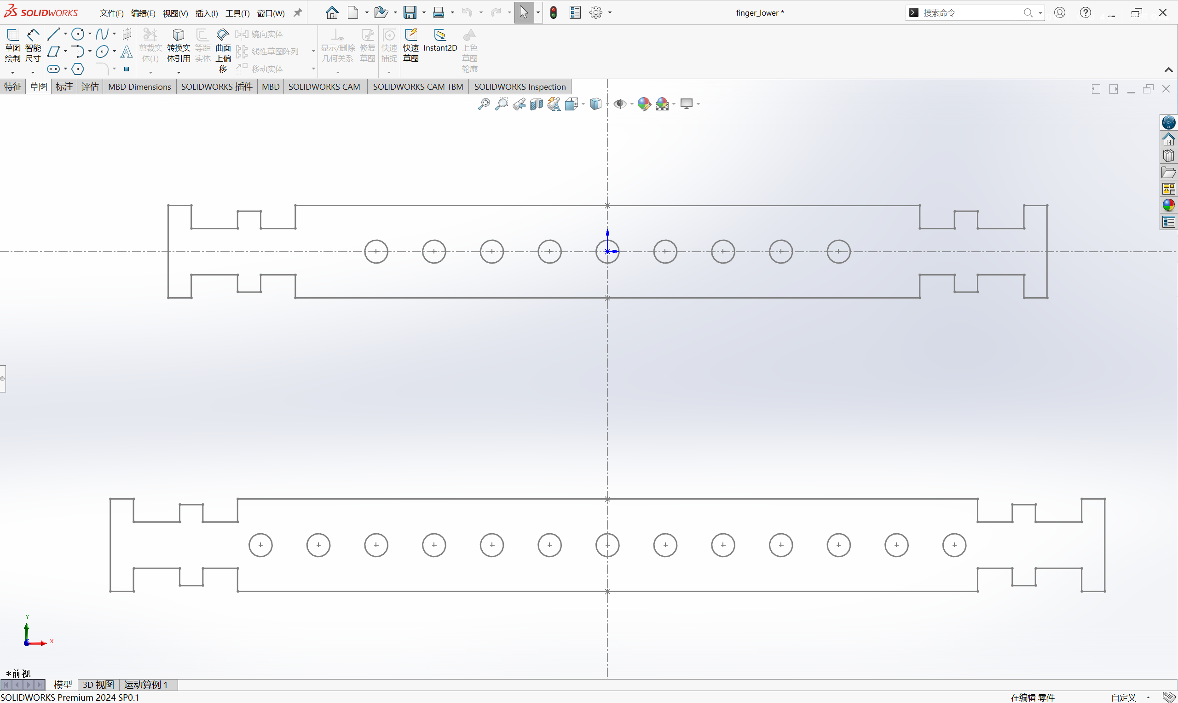
images/design_sketch/finger_lower.png
