JiajunGuo1027/Soft-Glove-Dissertation/images/design_sketch/finger_lower_longer_sketch.png

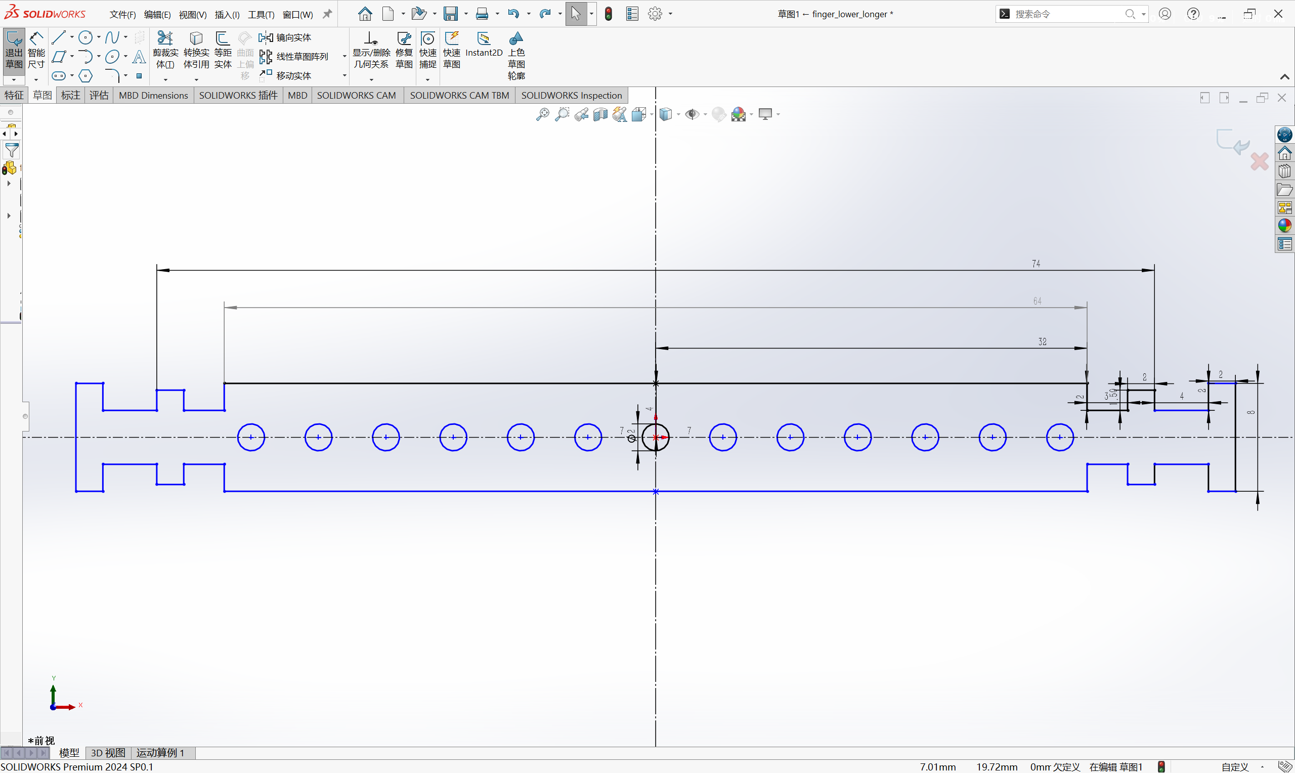
images/design_sketch/finger_lower_longer_sketch.png
