JiajunGuo1027/Soft-Glove-Dissertation/images/design_sketch/finger_upper.png

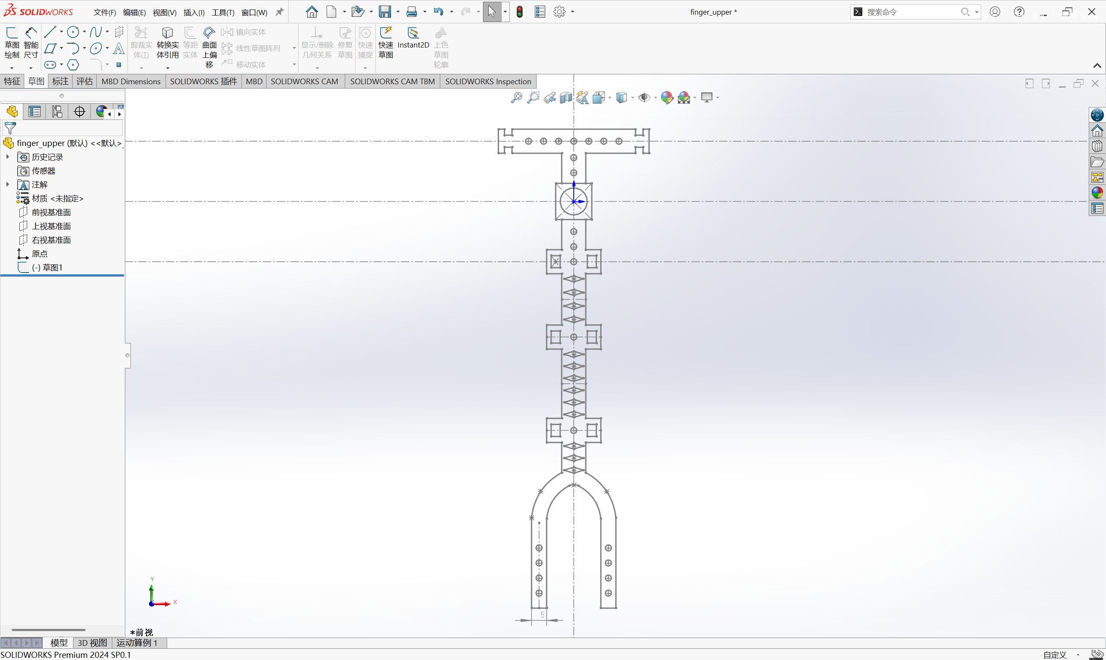
images/design_sketch/finger_upper.png
