JiajunGuo1027/Soft-Glove-Dissertation/images/design_sketch/longer2.png

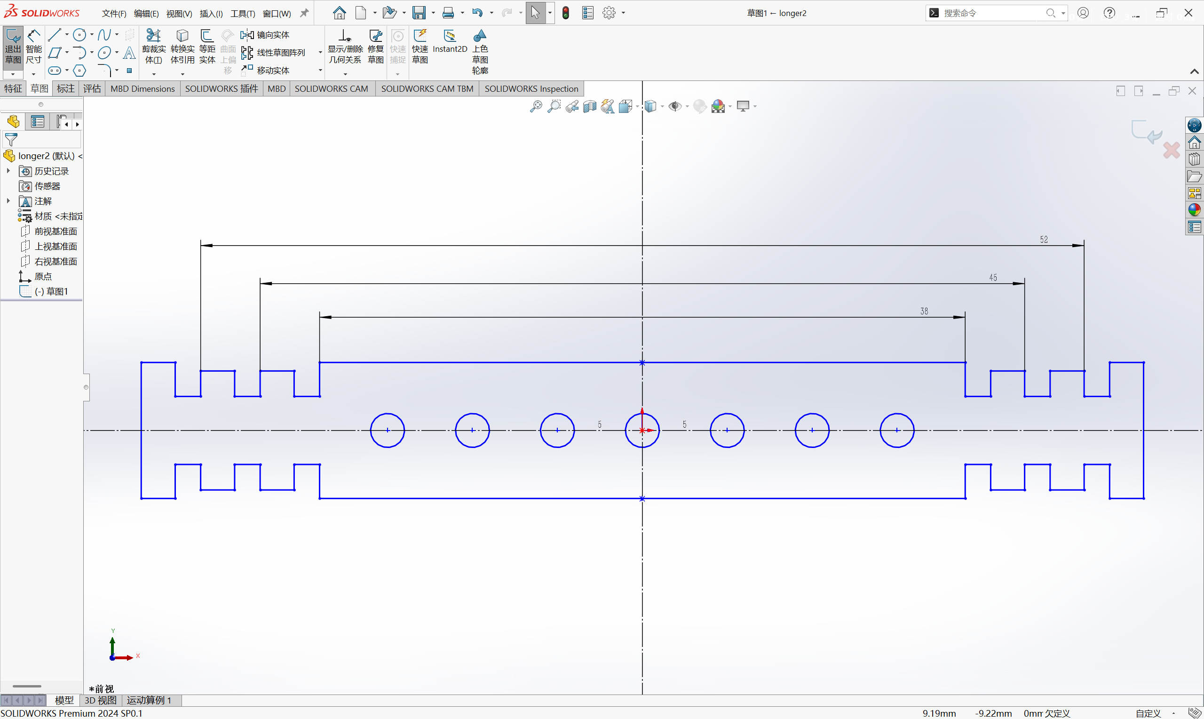
images/design_sketch/longer2.png
