JiajunGuo1027/Soft-Glove-Dissertation/images/design_sketch/palm.png

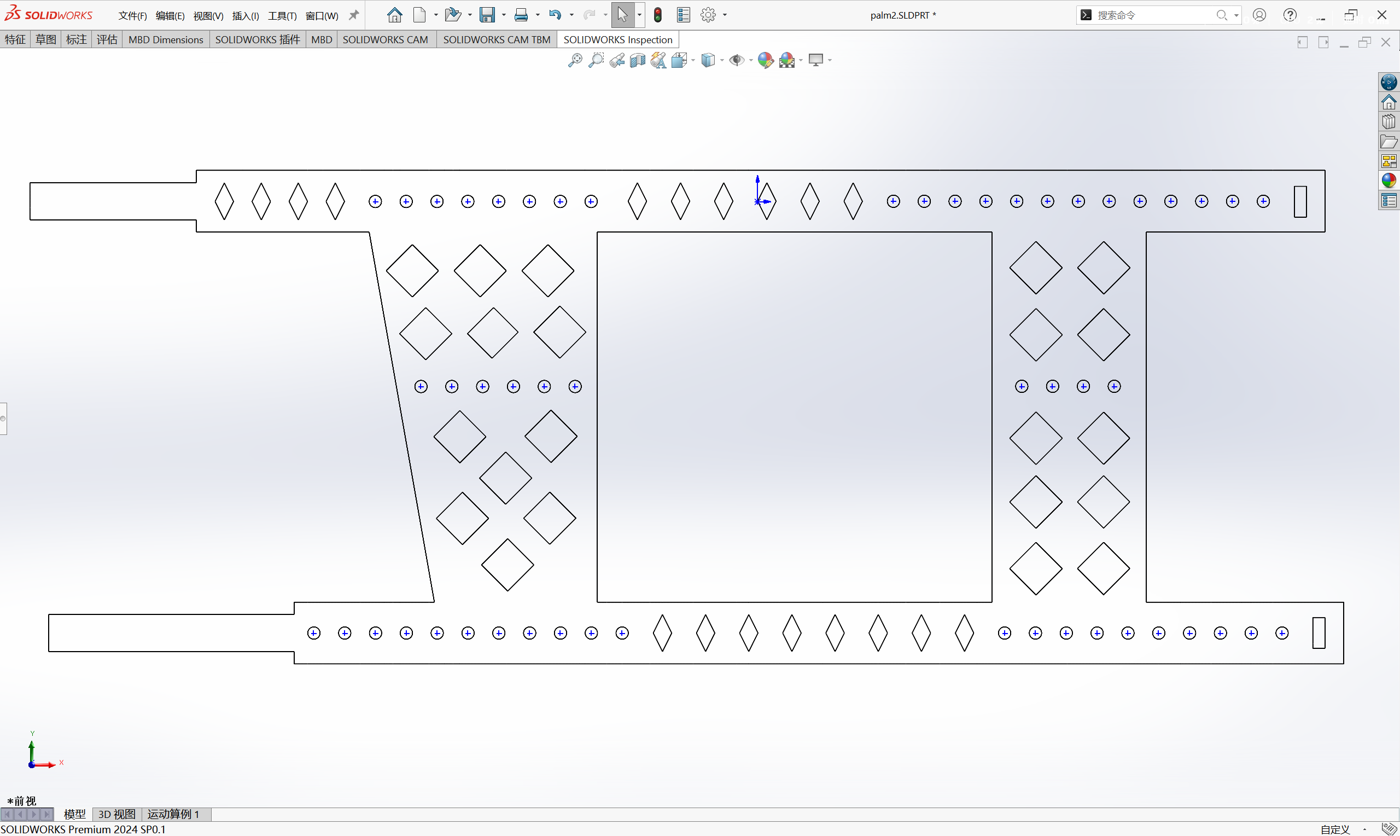
images/design_sketch/palm.png
