JiajunGuo1027/Soft-Glove-Dissertation/images/design_sketch/thumb_sketch.png

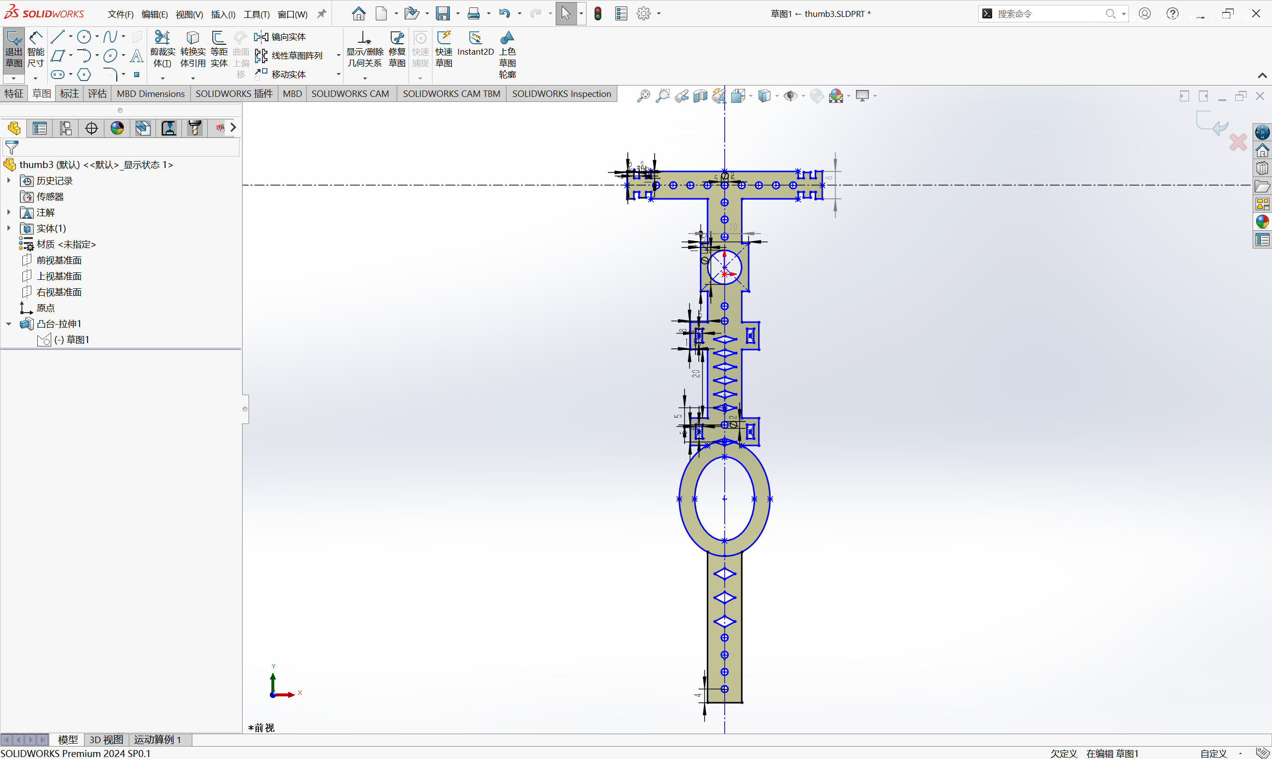
images/design_sketch/thumb_sketch.png
