JiajunGuo1027/Soft-Glove-Dissertation/models/index/R_L/R_L_Extend.png

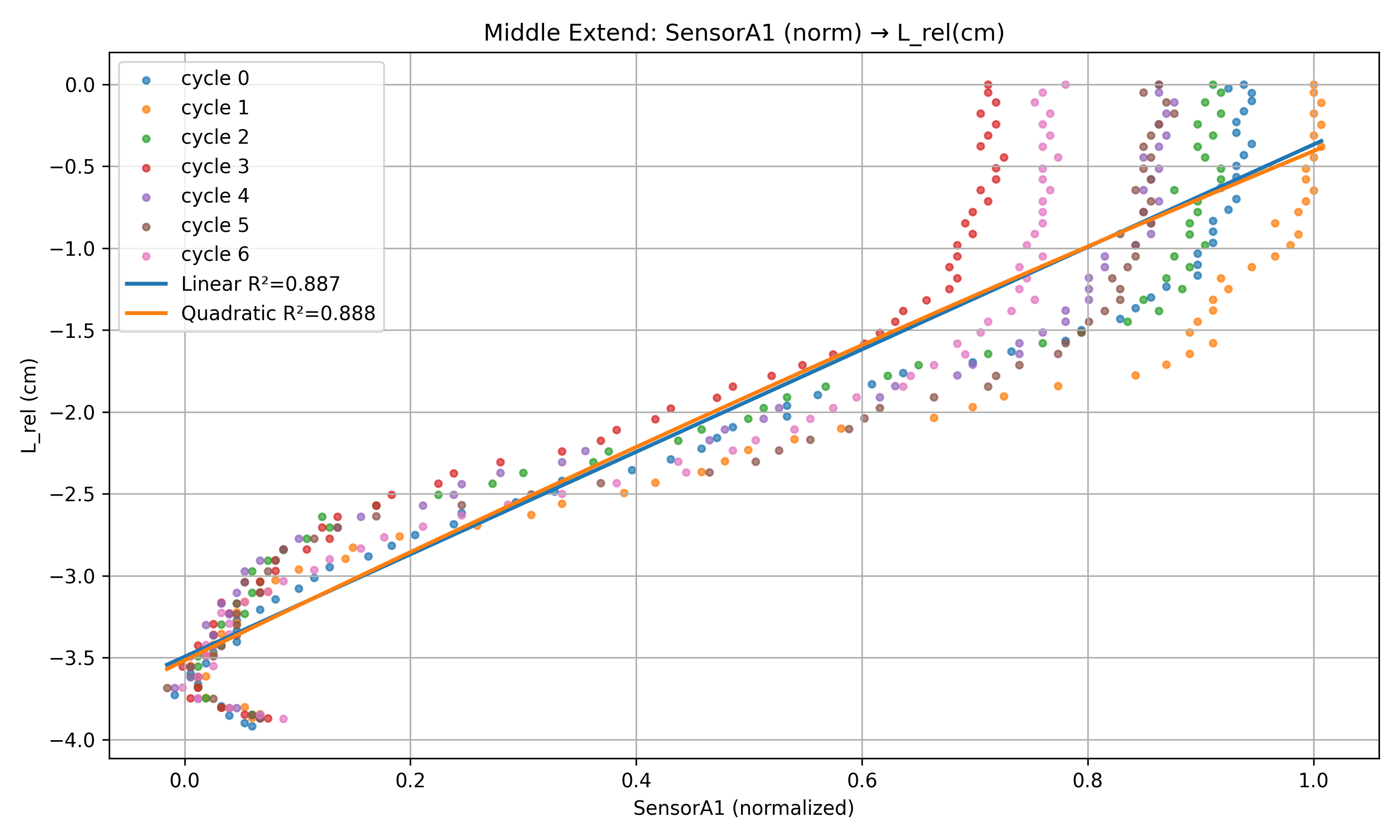
models/index/R_L/R_L_Extend.png
