JiajunGuo1027/Soft-Glove-Dissertation/models/index/R_L/R_L_Flex.png

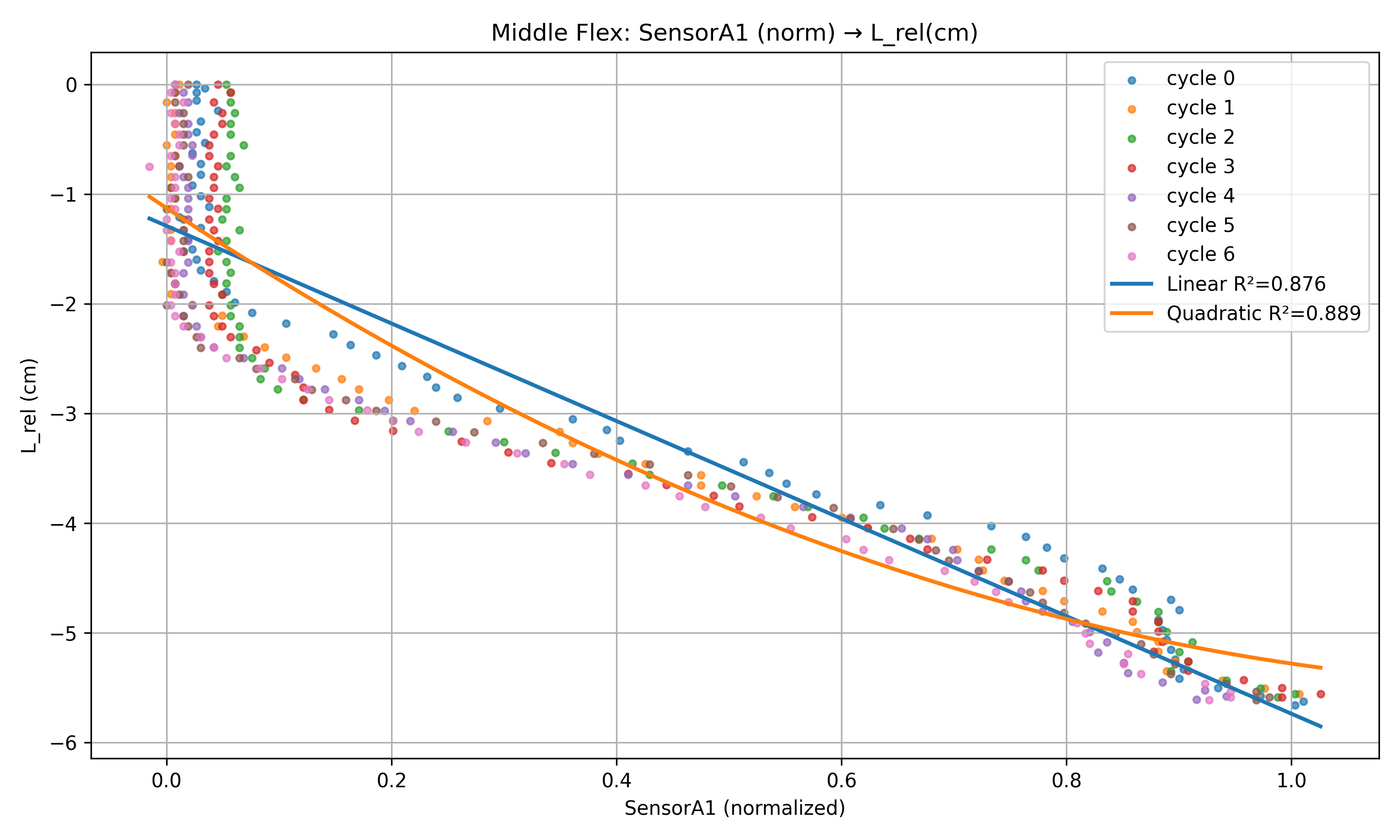
models/index/R_L/R_L_Flex.png
