JiajunGuo1027/Soft-Glove-Dissertation/models/index/R_theta_compose/0/R_theta_composed_timeseries.png

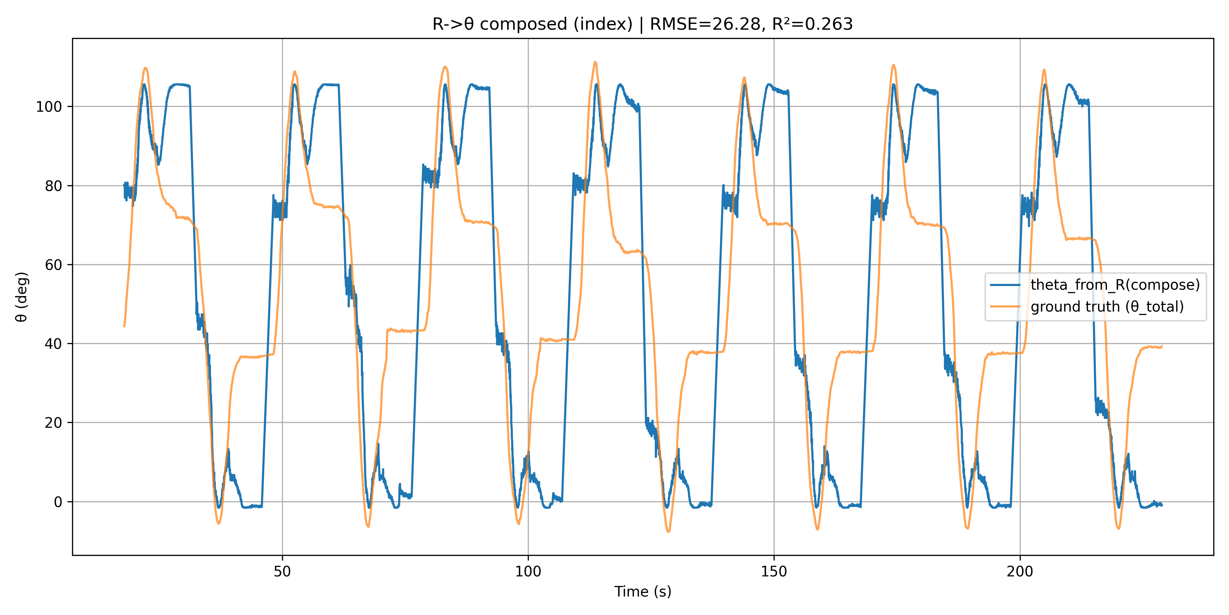
models/index/R_theta_compose/0/R_theta_composed_timeseries.png
