JiajunGuo1027/Soft-Glove-Dissertation/models/index/R_theta_compose_active/R_theta_composed_ACTIVE_scatter_Extend.png

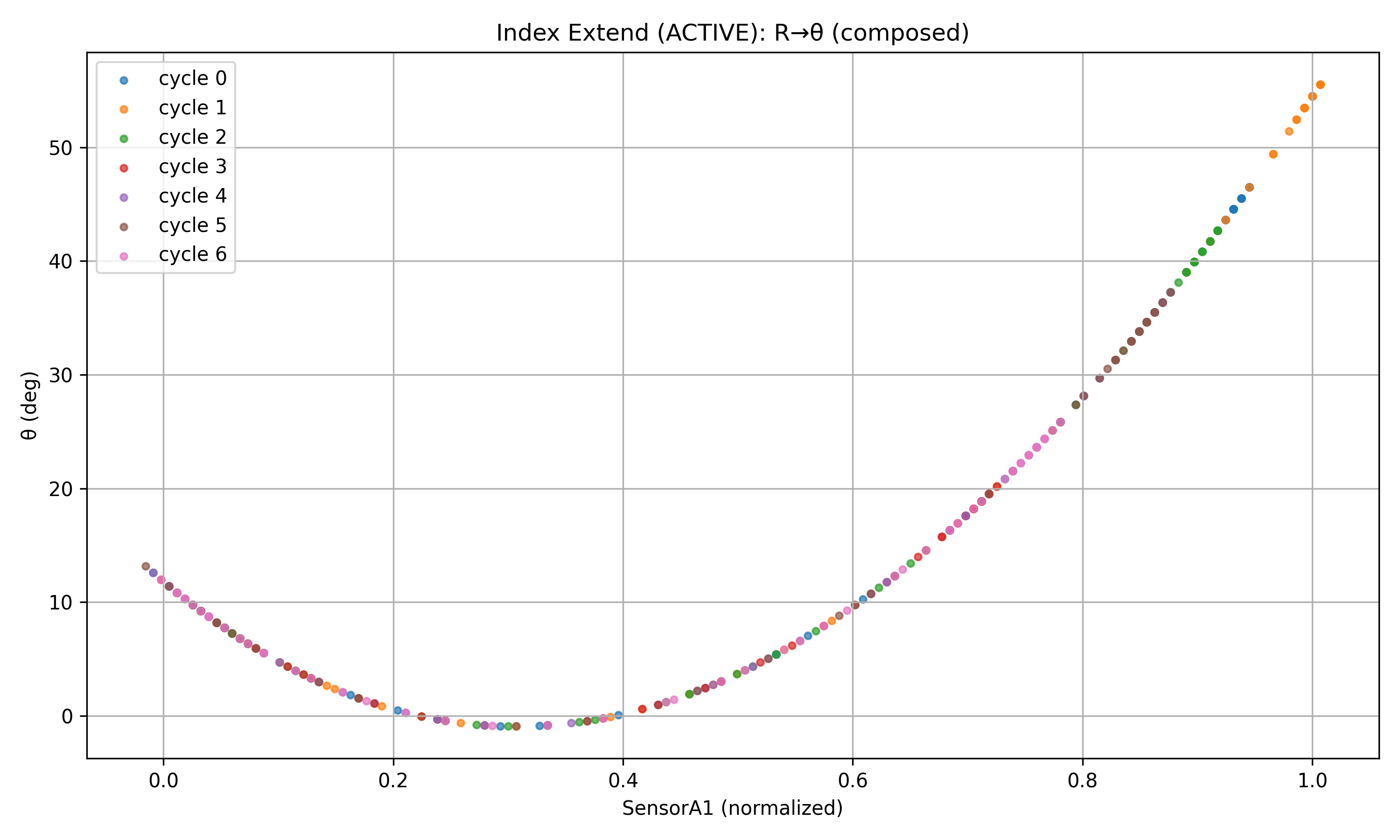
models/index/R_theta_compose_active/R_theta_composed_ACTIVE_scatter_Extend.png
