JiajunGuo1027/Soft-Glove-Dissertation/models/index/R_theta_compose_active/R_theta_composed_timeseries_ALL.png

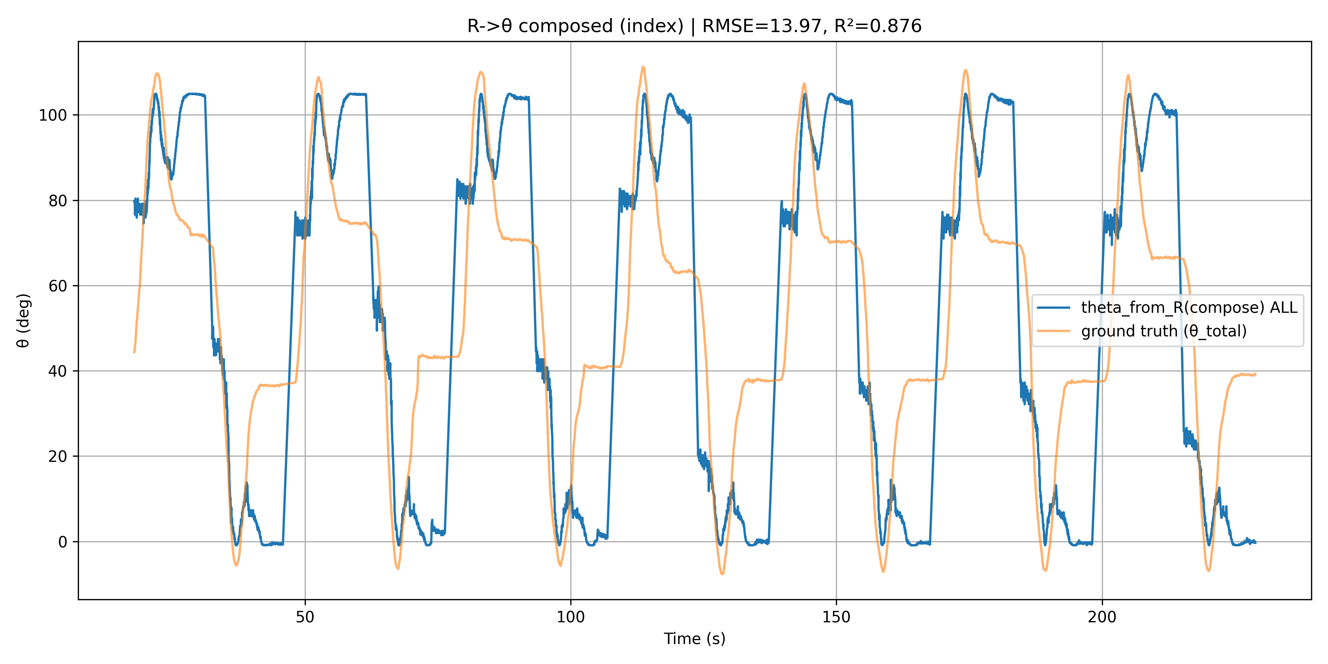
models/index/R_theta_compose_active/R_theta_composed_timeseries_ALL.png
