JiajunGuo1027/Soft-Glove-Dissertation/models/index/R_theta_direct/R_theta_Extend.png

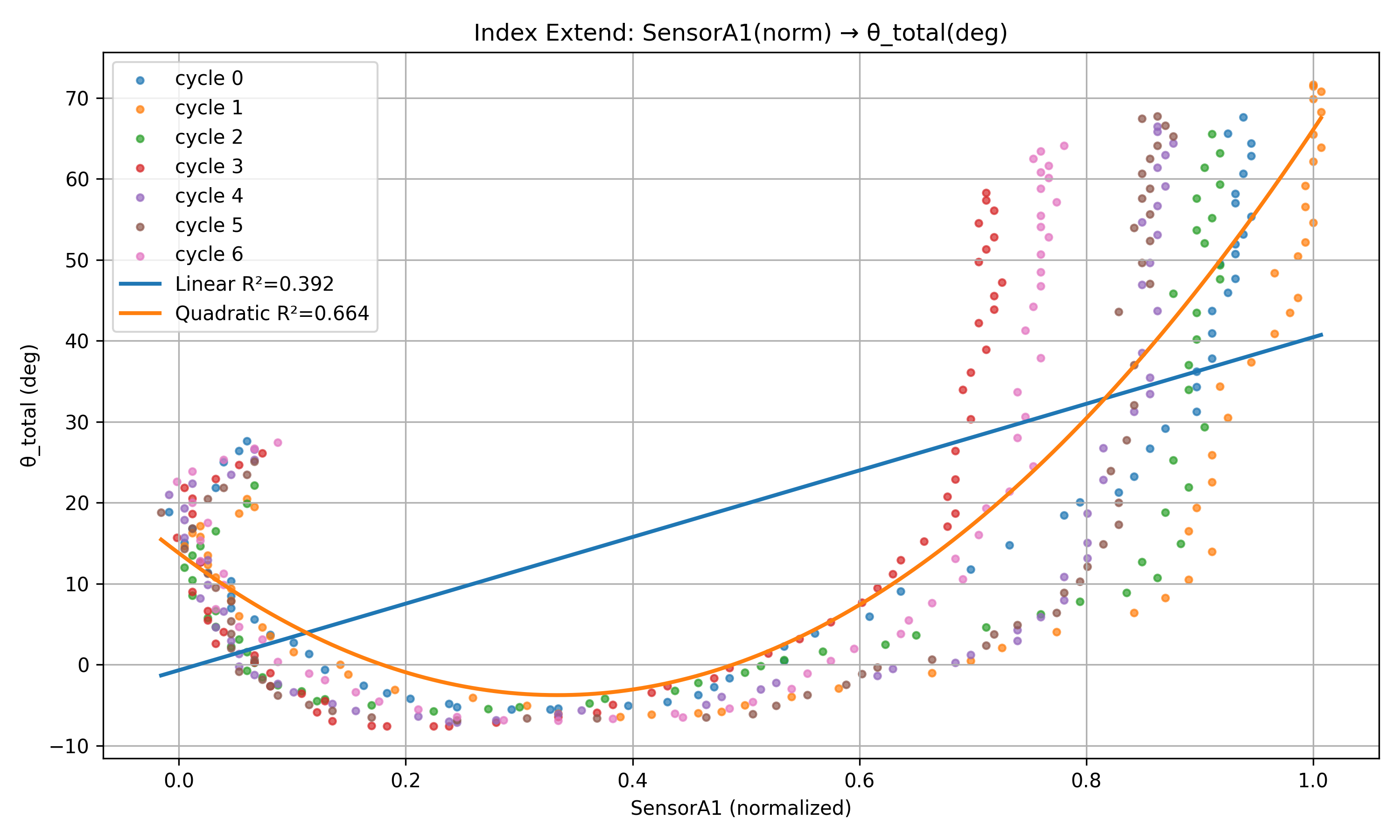
models/index/R_theta_direct/R_theta_Extend.png
