JiajunGuo1027/Soft-Glove-Dissertation/models/index/R_theta_direct/R_theta_Flex.png

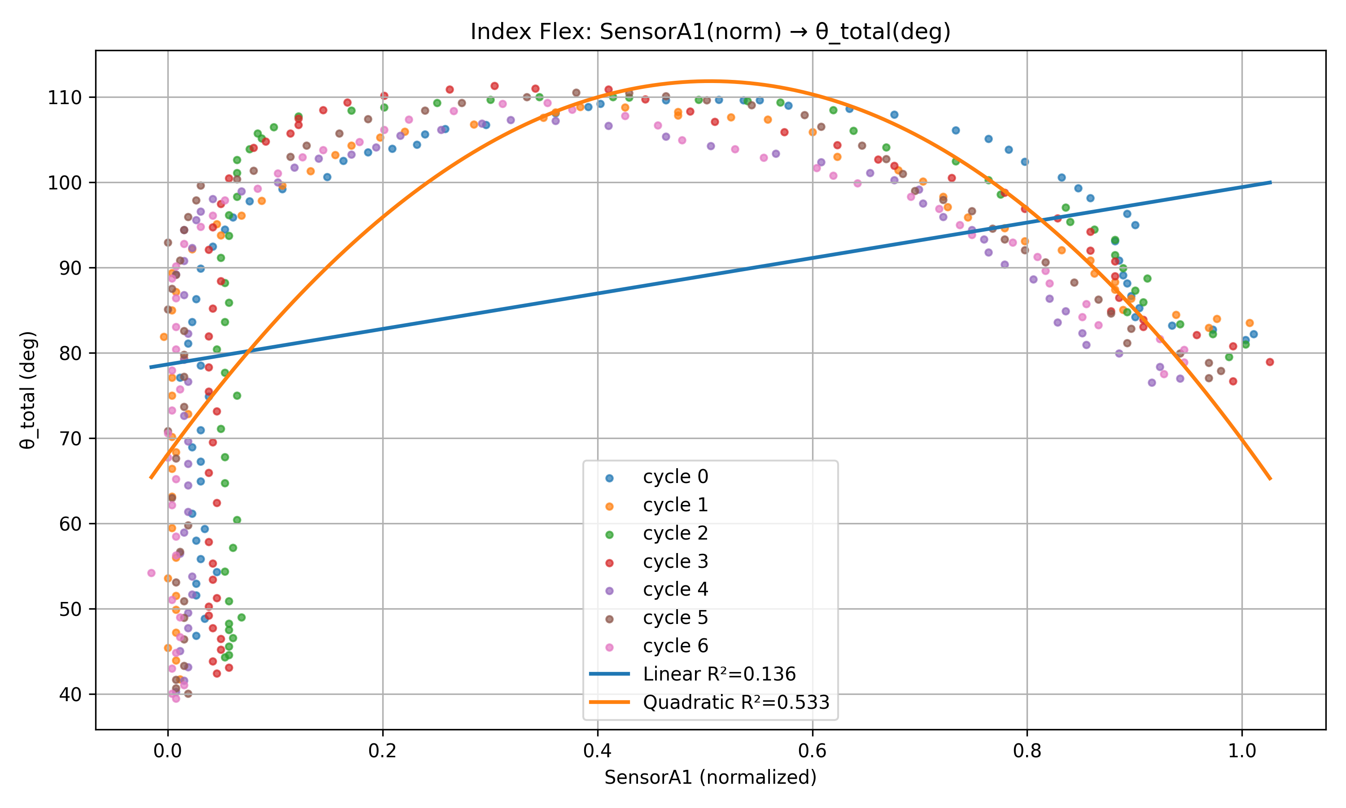
models/index/R_theta_direct/R_theta_Flex.png
