JiajunGuo1027/Soft-Glove-Dissertation/models/middle/L_theta/1/middle_Extend_θ_total_vs_Lrel.png

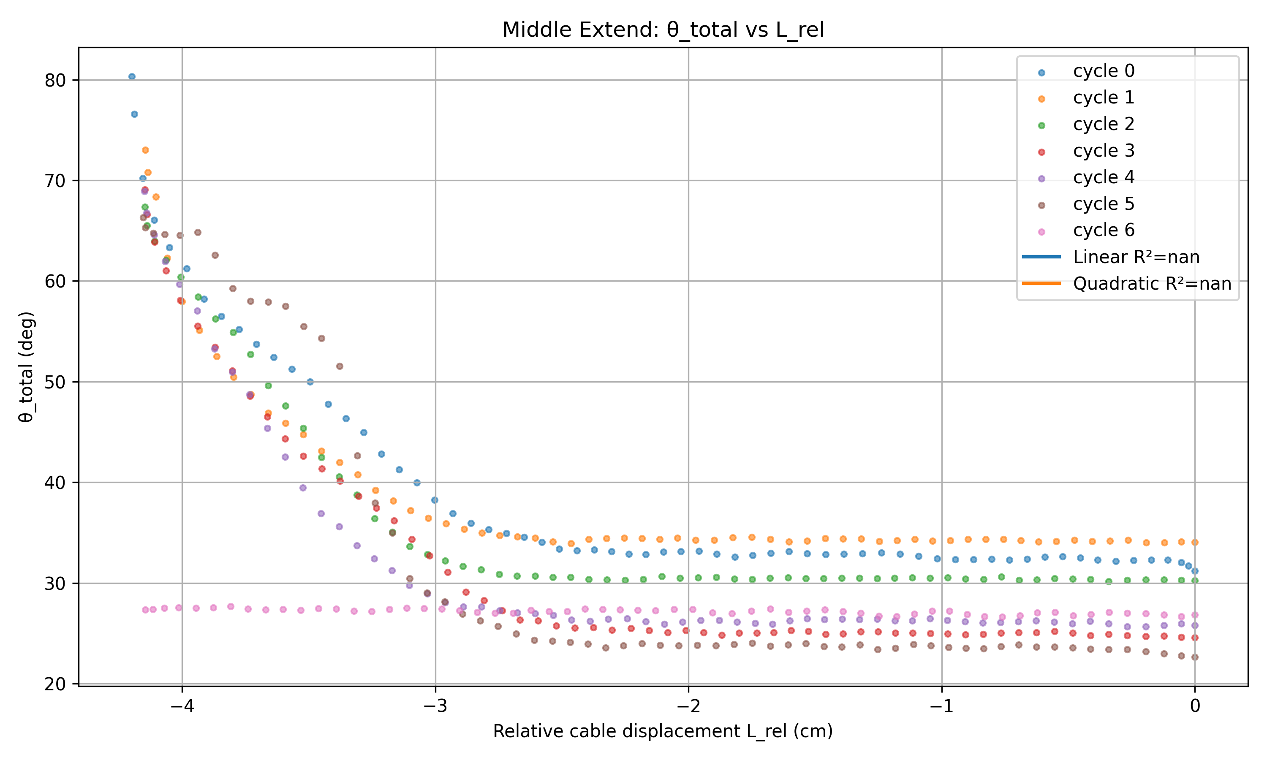
models/middle/L_theta/1/middle_Extend_θ_total_vs_Lrel.png
