JiajunGuo1027/Soft-Glove-Dissertation/models/middle/L_theta/1/middle_Flex_∠BCD_smooth_vs_Lrel.png

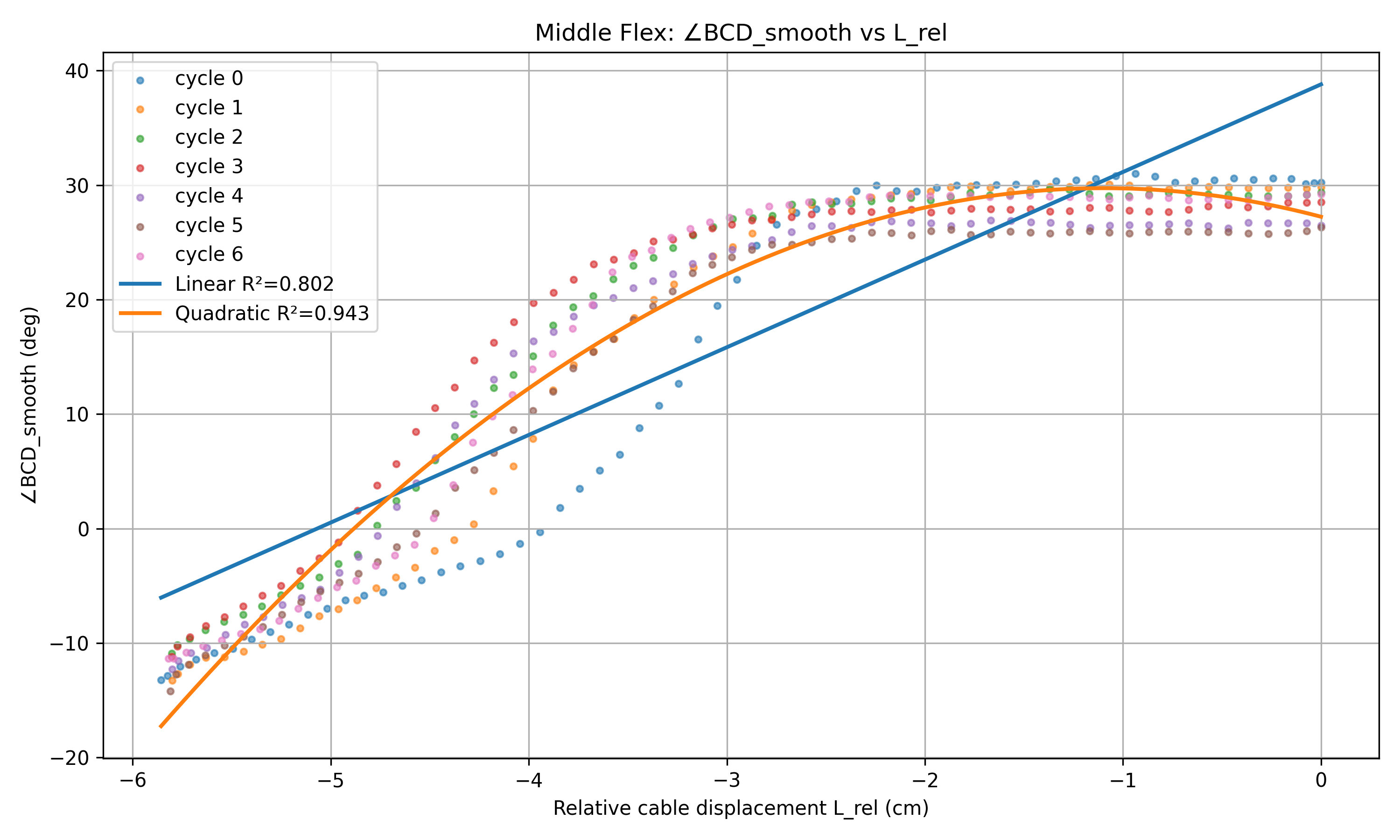
models/middle/L_theta/1/middle_Flex_∠BCD_smooth_vs_Lrel.png
