JiajunGuo1027/Soft-Glove-Dissertation/models/middle/L_theta/2_middle/middle_Extend_∠BCD_smooth_vs_Lrel.png

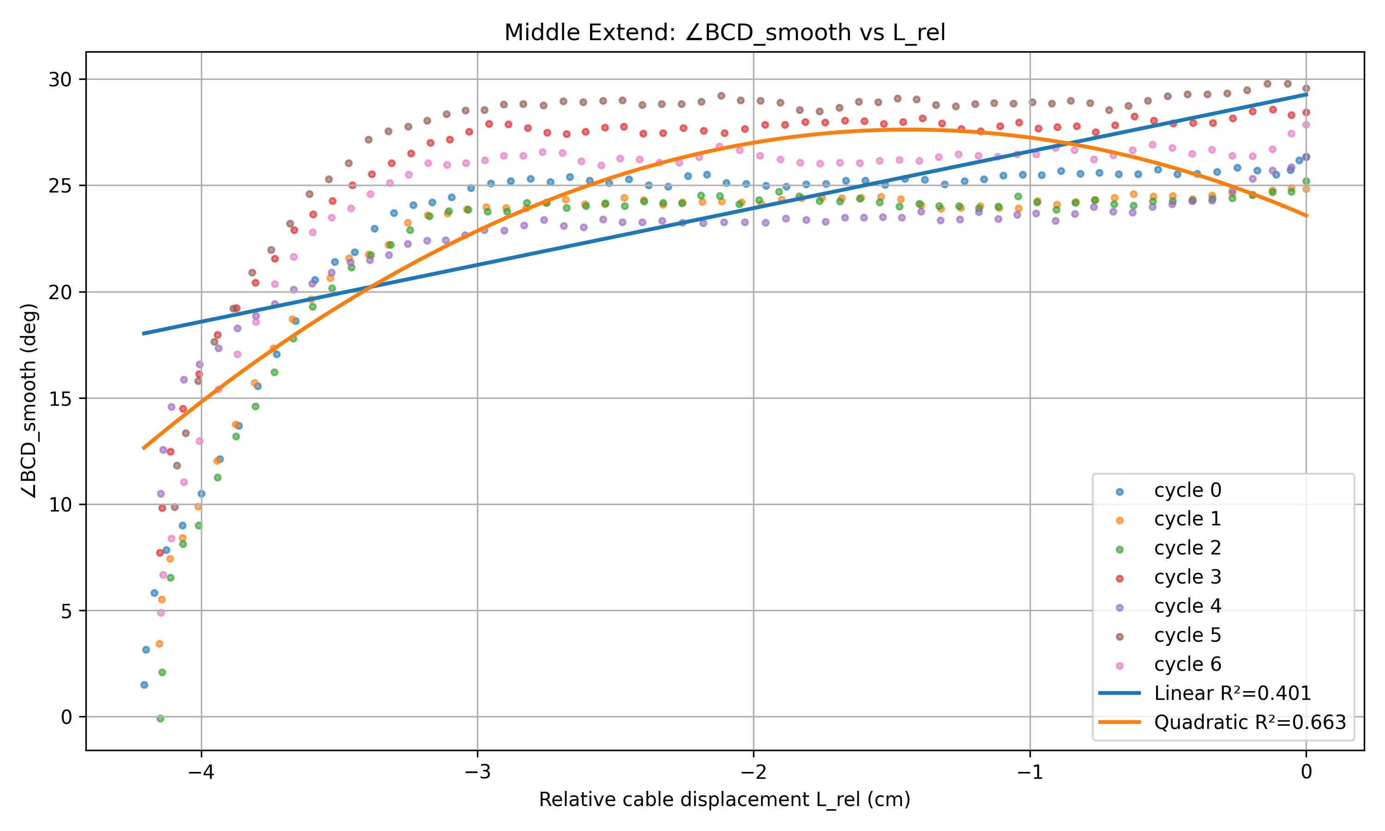
models/middle/L_theta/2_middle/middle_Extend_∠BCD_smooth_vs_Lrel.png
