JiajunGuo1027/Soft-Glove-Dissertation/models/middle/L_theta/2_middle/middle_Flex_∠ABC_smooth_vs_Lrel.png

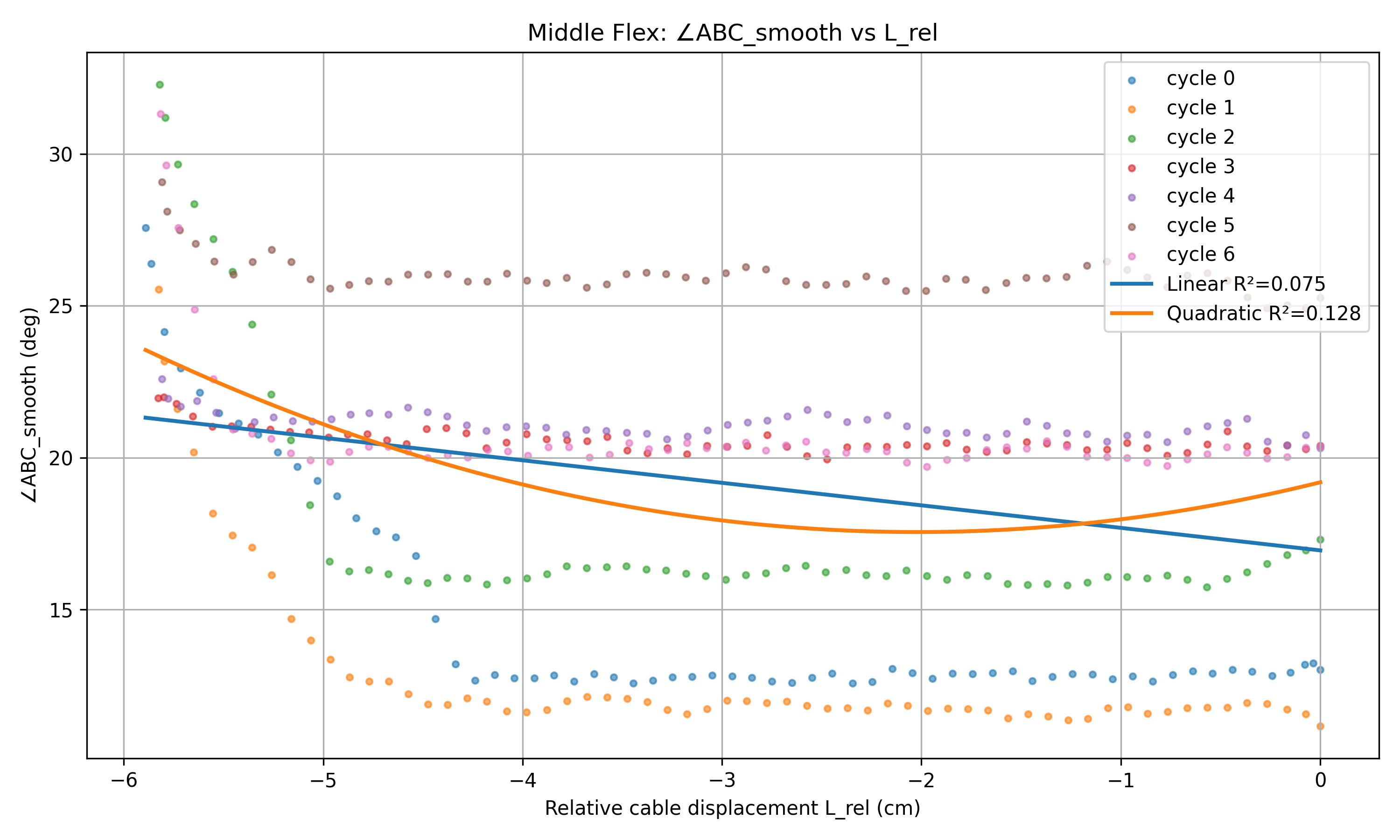
models/middle/L_theta/2_middle/middle_Flex_∠ABC_smooth_vs_Lrel.png
