JiajunGuo1027/Soft-Glove-Dissertation/models/middle/L_theta/index_transfer_fit/middle_Extend_transfer_fit.png

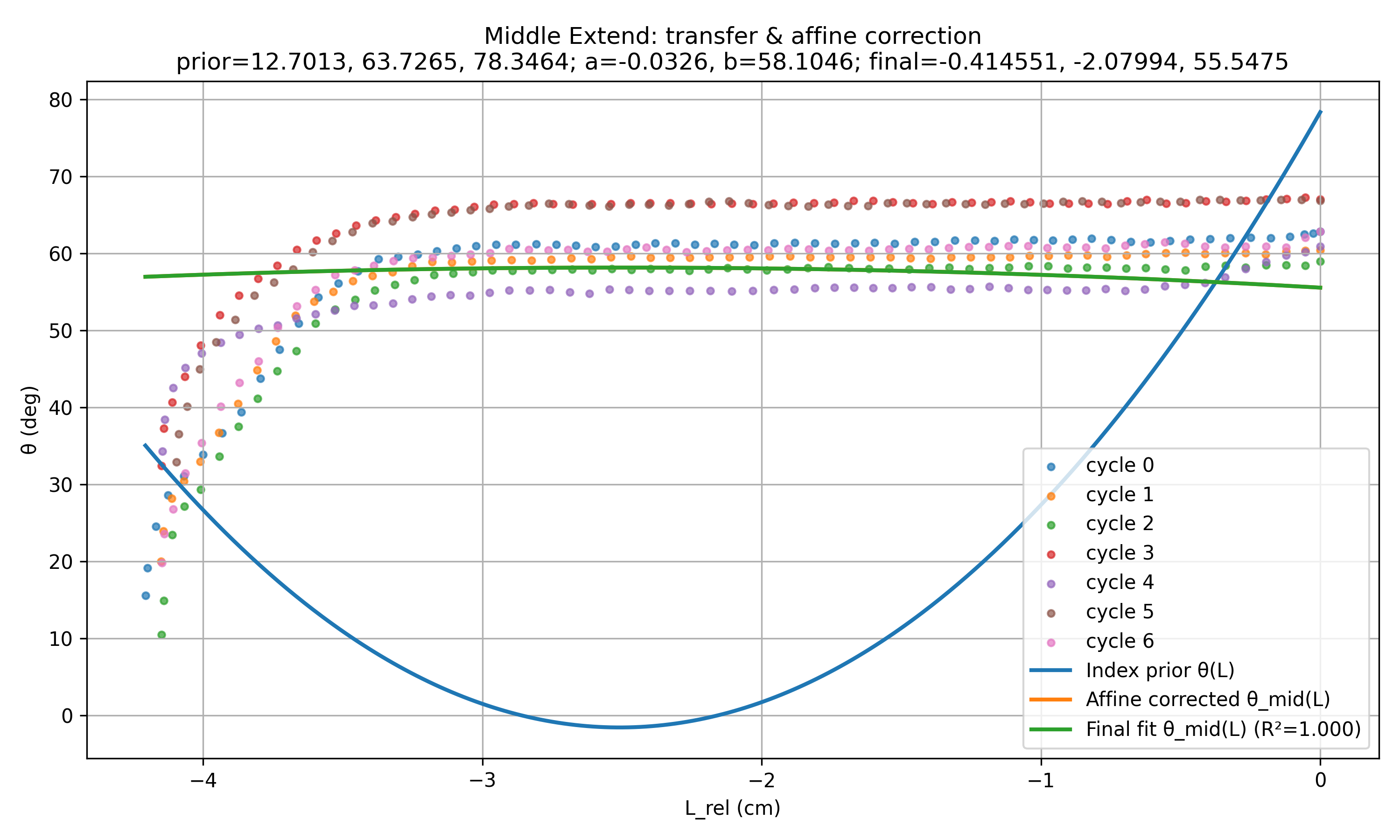
models/middle/L_theta/index_transfer_fit/middle_Extend_transfer_fit.png
