JiajunGuo1027/Soft-Glove-Dissertation/models/middle/L_theta/middle_Extend_∠ABC_smooth_vs_Lrel.png

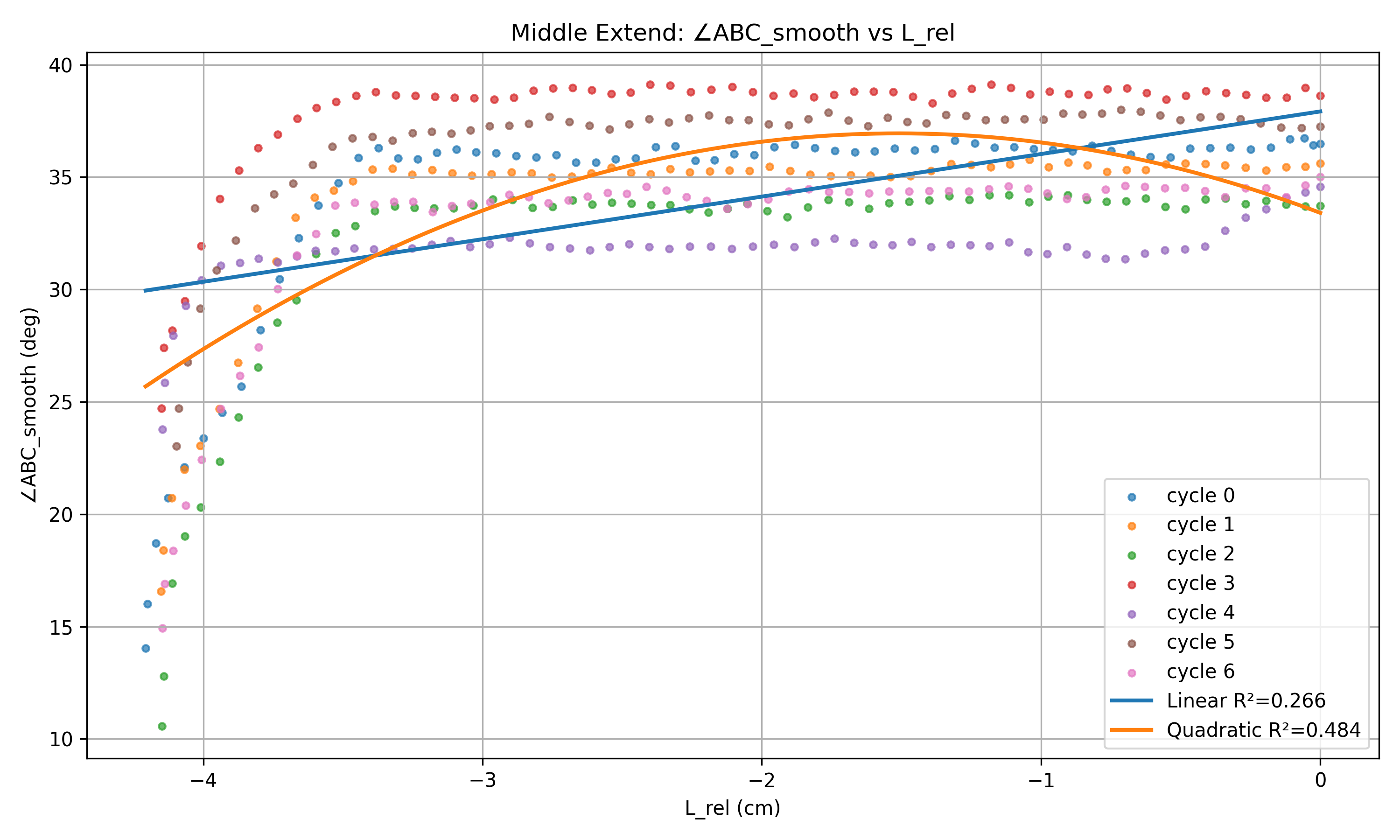
models/middle/L_theta/middle_Extend_∠ABC_smooth_vs_Lrel.png
