JiajunGuo1027/Soft-Glove-Dissertation/models/middle/L_theta/middle_Flex_θ_total_vs_Lrel.png

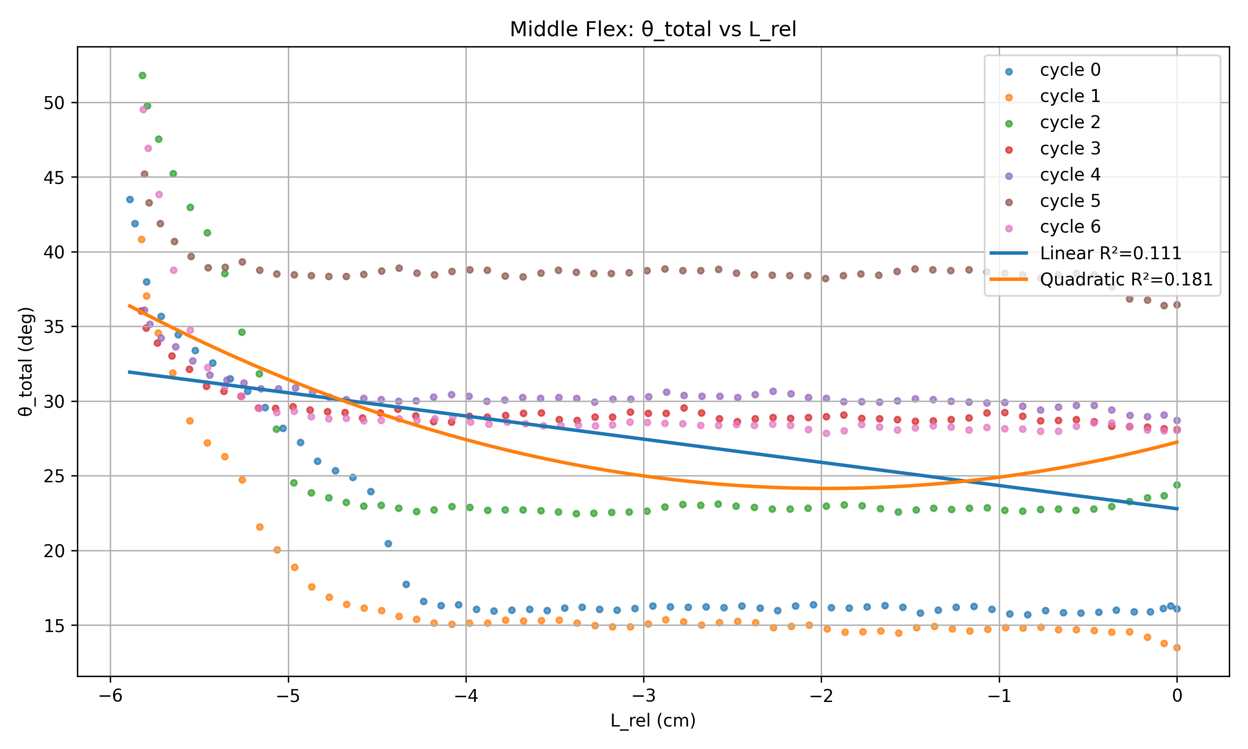
models/middle/L_theta/middle_Flex_θ_total_vs_Lrel.png
