JiajunGuo1027/Soft-Glove-Dissertation/models/middle/proxy_theta/proxy_theta_timeseries.png

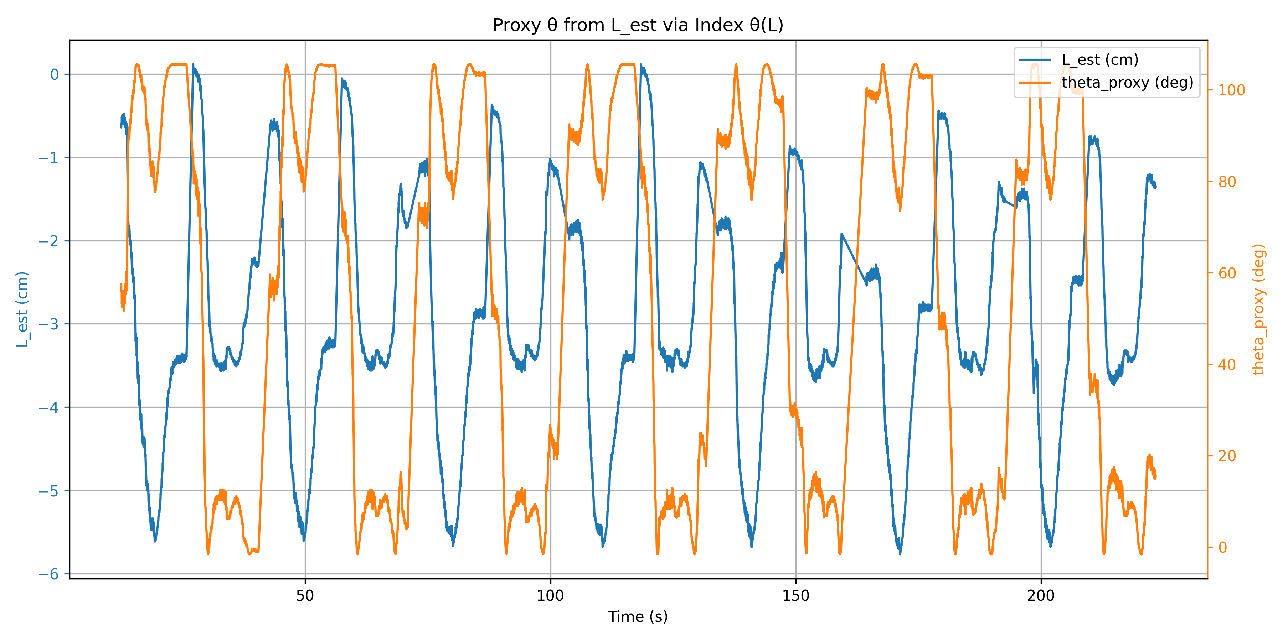
models/middle/proxy_theta/proxy_theta_timeseries.png
