JiajunGuo1027/Soft-Glove-Dissertation/models/middle/R_theta_compose/R_theta_composed_timeseries.png

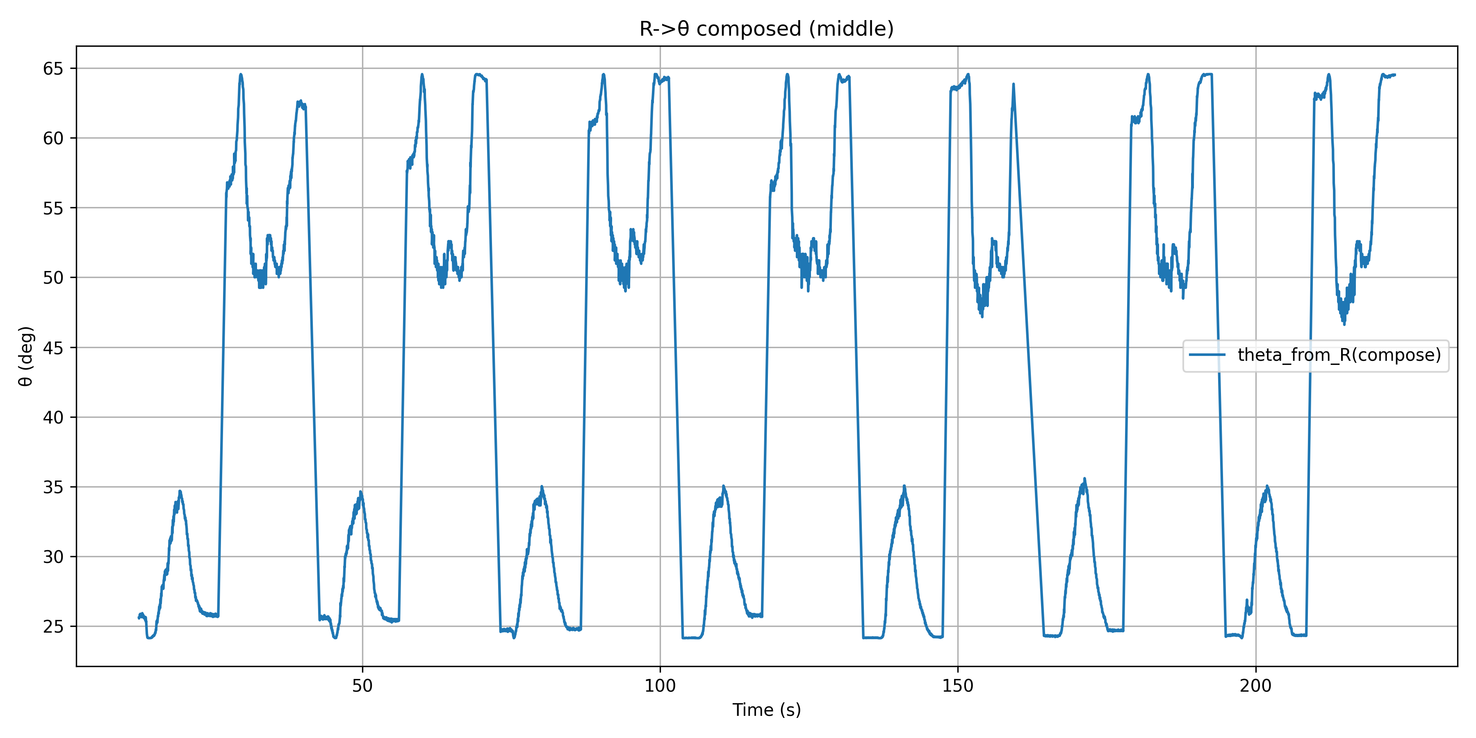
models/middle/R_theta_compose/R_theta_composed_timeseries.png
