JiajunGuo1027/Soft-Glove-Dissertation/models/middle/R_theta_compose_active/R_theta_composed_ACTIVE_scatter_Flex.png

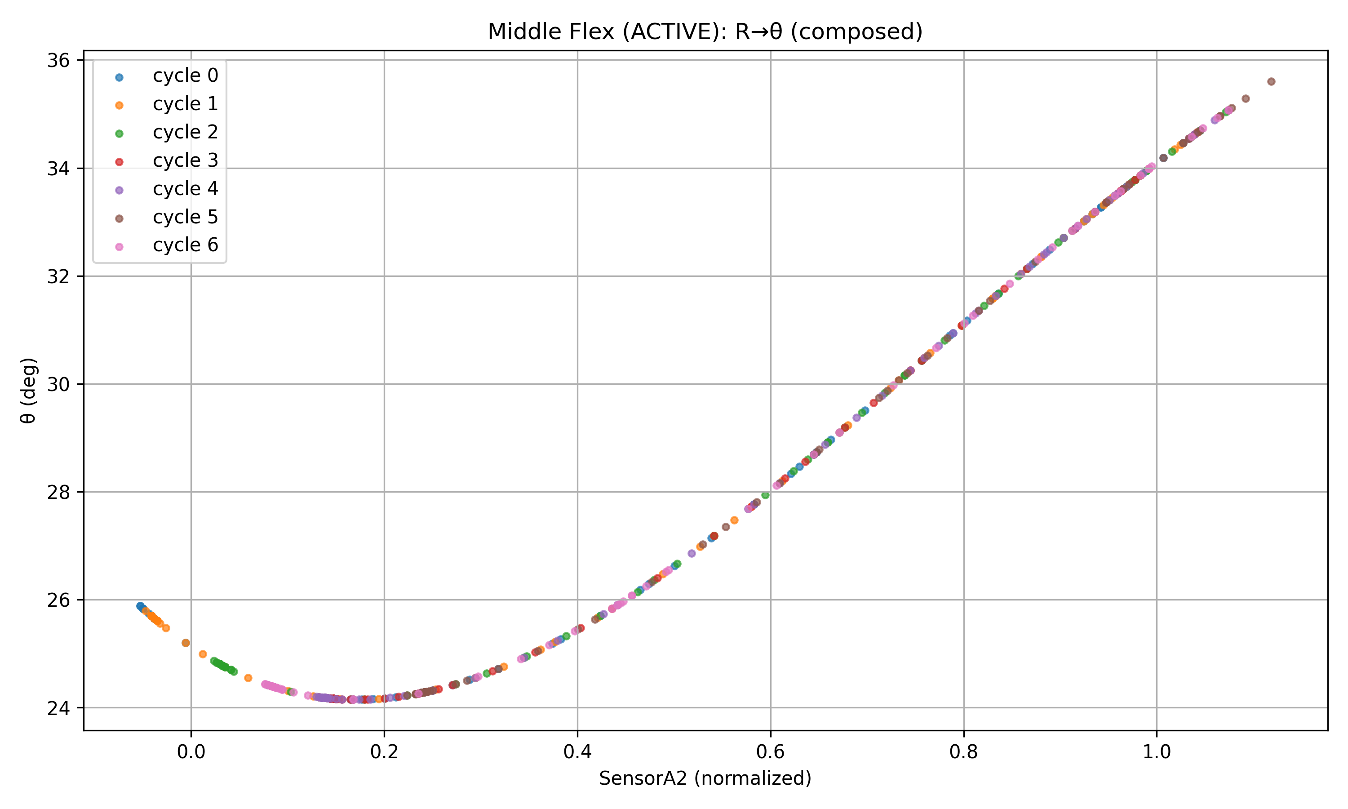
models/middle/R_theta_compose_active/R_theta_composed_ACTIVE_scatter_Flex.png
