JiajunGuo1027/Soft-Glove-Dissertation/models/middle/R_theta_direct/R_theta_Extend.png

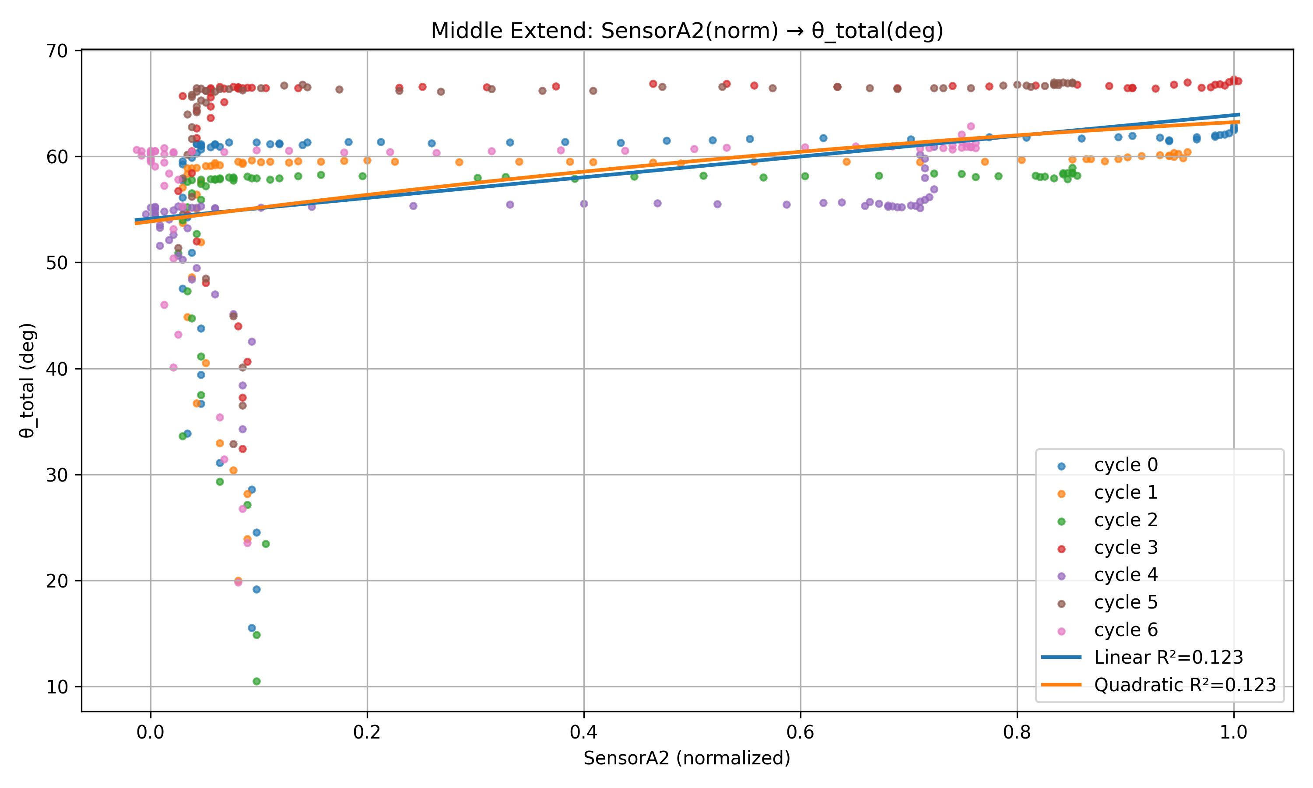
models/middle/R_theta_direct/R_theta_Extend.png
