JiajunGuo1027/Soft-Glove-Dissertation/models/middle/R_theta_direct/R_theta_Flex.png

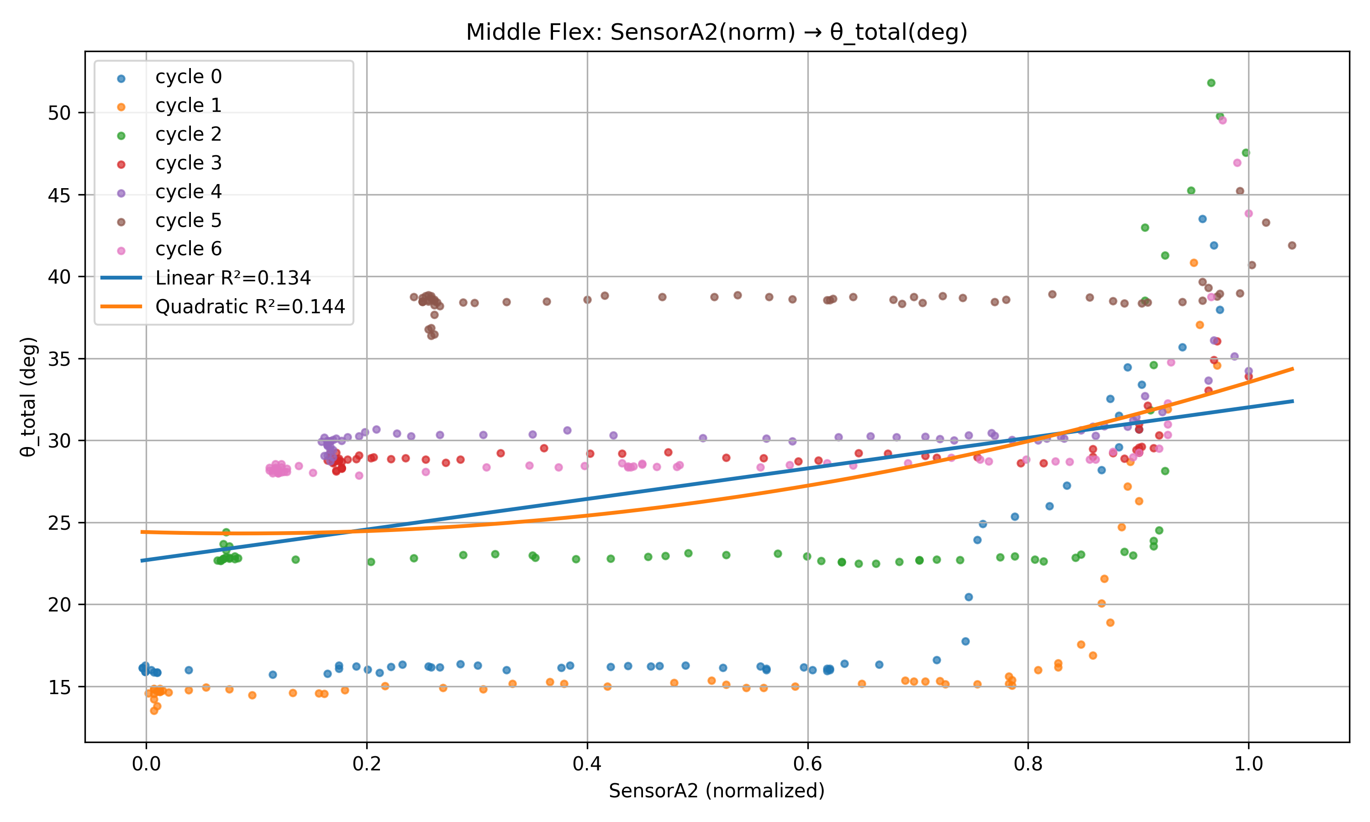
models/middle/R_theta_direct/R_theta_Flex.png
