JiajunGuo1027/Soft-Glove-Dissertation/models/qu_cubic/index/L_theta/index_Extend_θ_total_vs_Lrel.png

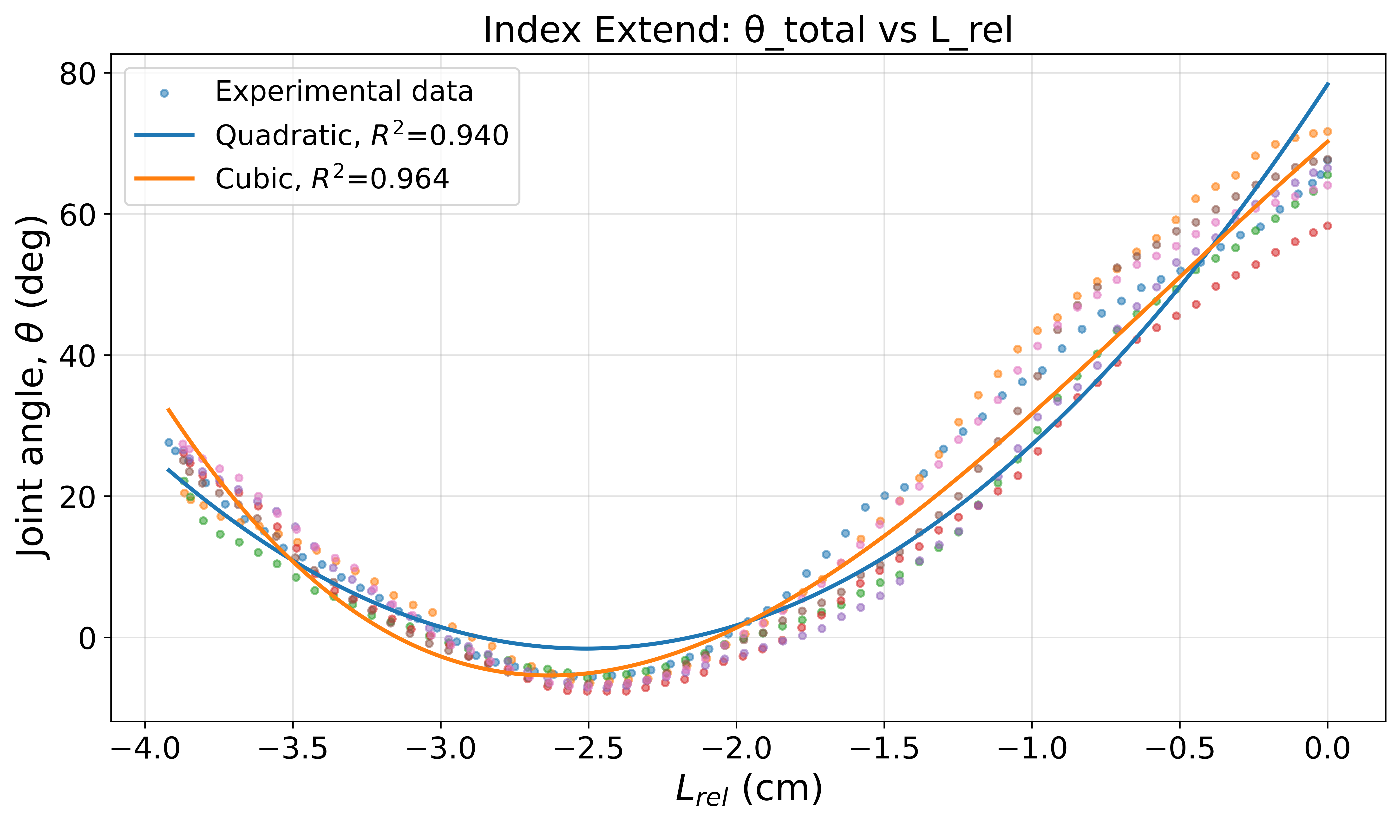
models/qu_cubic/index/L_theta/index_Extend_θ_total_vs_Lrel.png
