JiajunGuo1027/Soft-Glove-Dissertation/models/qu_cubic/index/L_theta/index_Flex_∠BCD_smooth_vs_Lrel.png

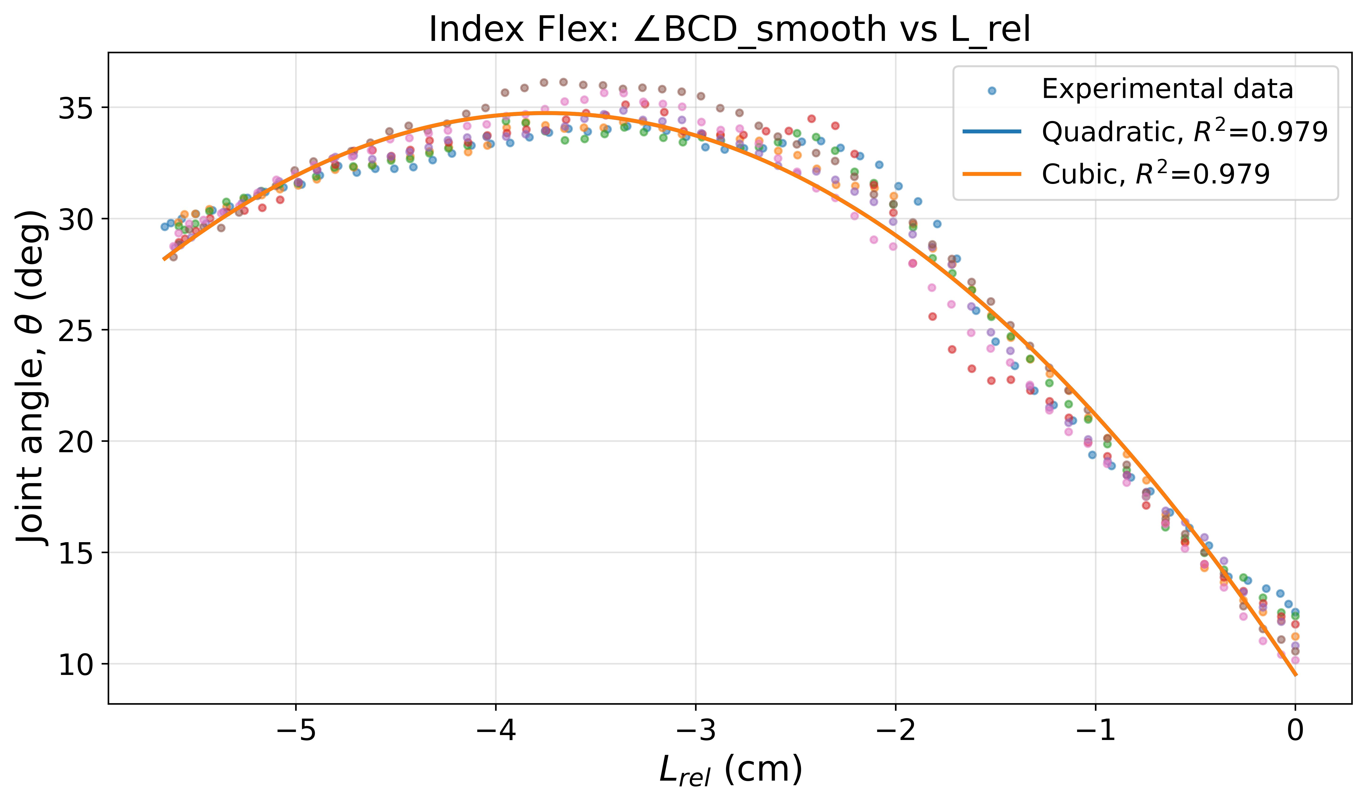
models/qu_cubic/index/L_theta/index_Flex_∠BCD_smooth_vs_Lrel.png
