JiajunGuo1027/Soft-Glove-Dissertation/models/qu_cubic/middle/R_L/R_L_Flex.png

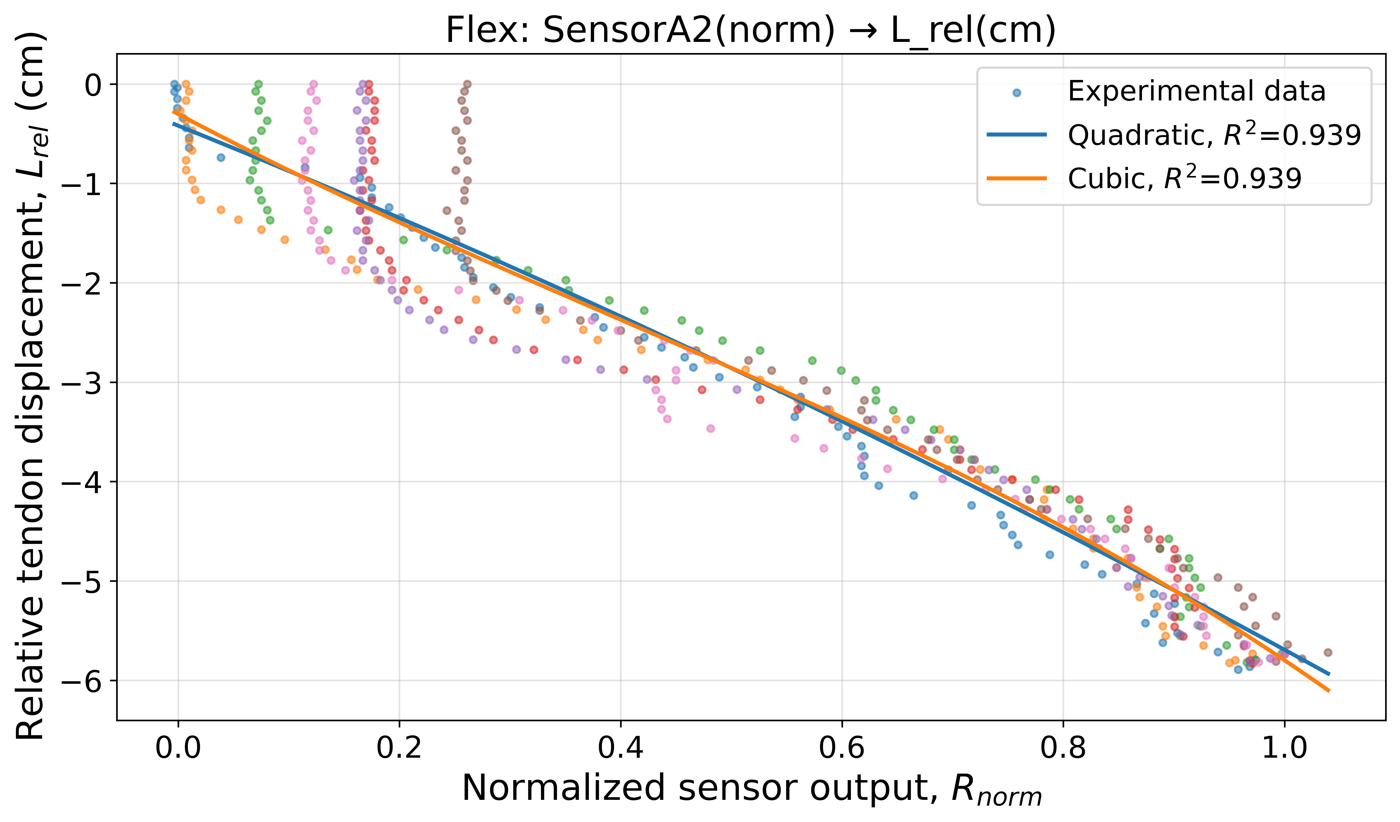
models/qu_cubic/middle/R_L/R_L_Flex.png
