JiajunGuo1027/Soft-Glove-Dissertation/models/thumb/L_theta/thumb_Extend_∠ABD_smooth_vs_Lrel.png

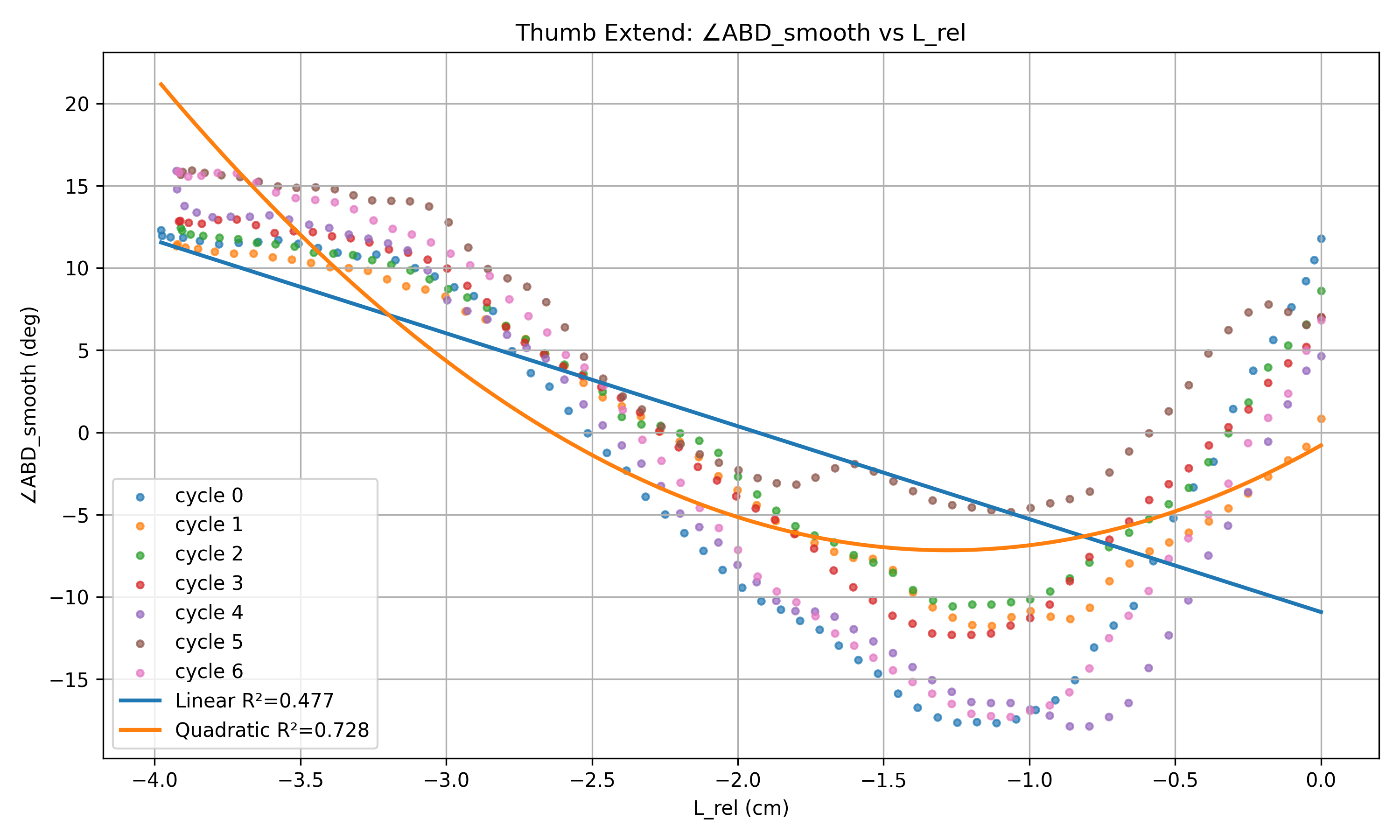
models/thumb/L_theta/thumb_Extend_∠ABD_smooth_vs_Lrel.png
