JiajunGuo1027/Soft-Glove-Dissertation/models/thumb/R_L/R_L_Flex.png

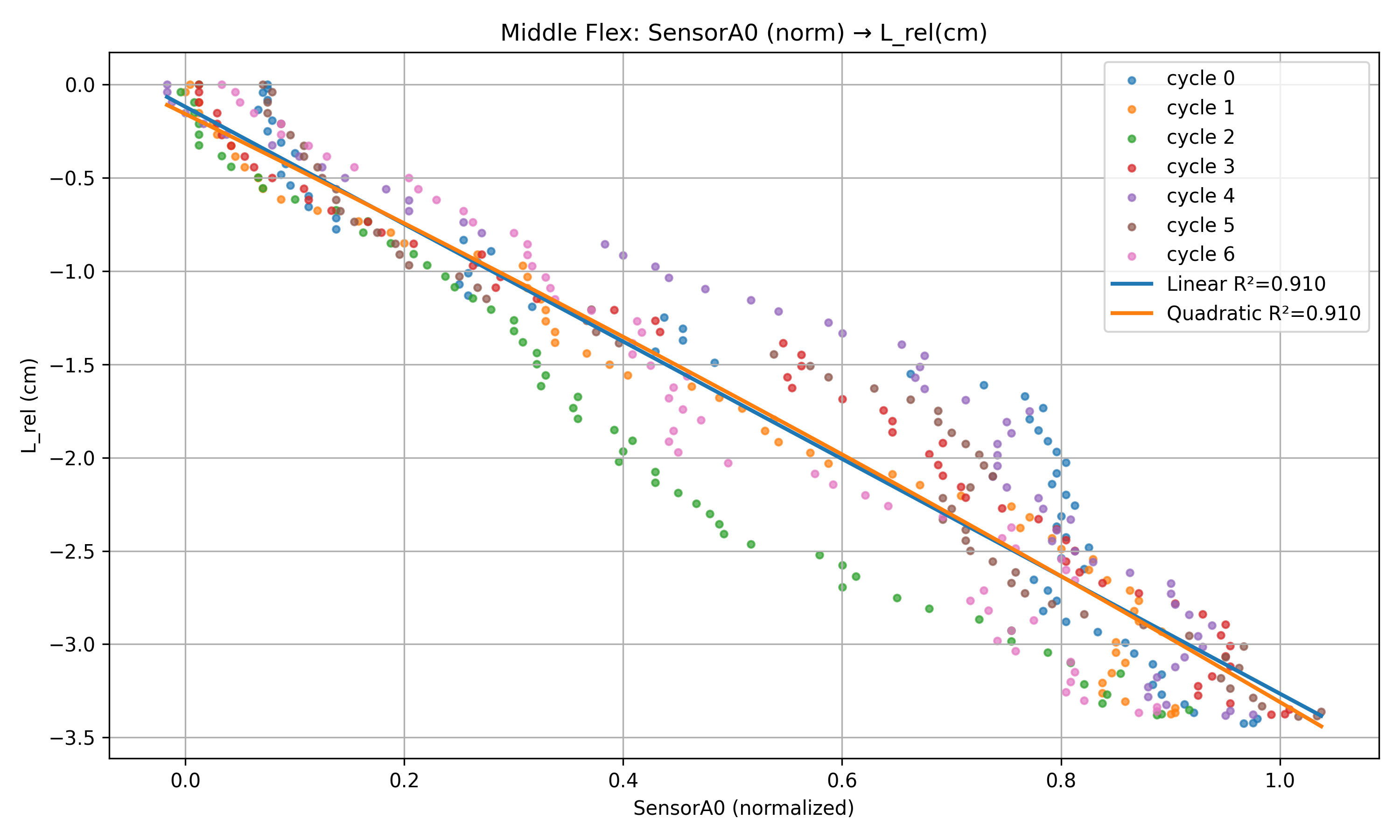
models/thumb/R_L/R_L_Flex.png
