JiajunGuo1027/Soft-Glove-Dissertation/models/thumb/R_theta_compose/R_theta_composed_timeseries.png

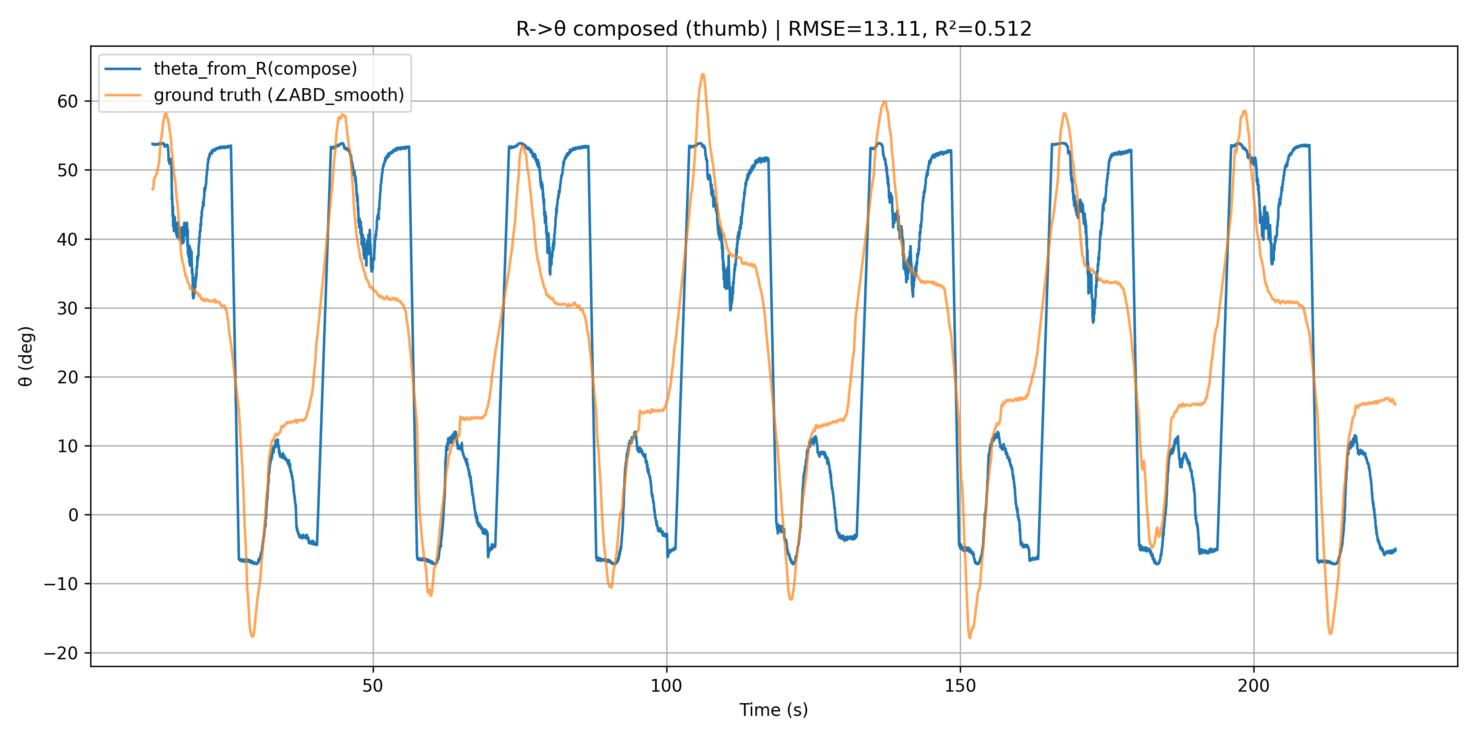
models/thumb/R_theta_compose/R_theta_composed_timeseries.png
