JiajunGuo1027/Soft-Glove-Dissertation/models/thumb/R_theta_compose_active/1/R_theta_composed_ACTIVE_scatter_Extend.png

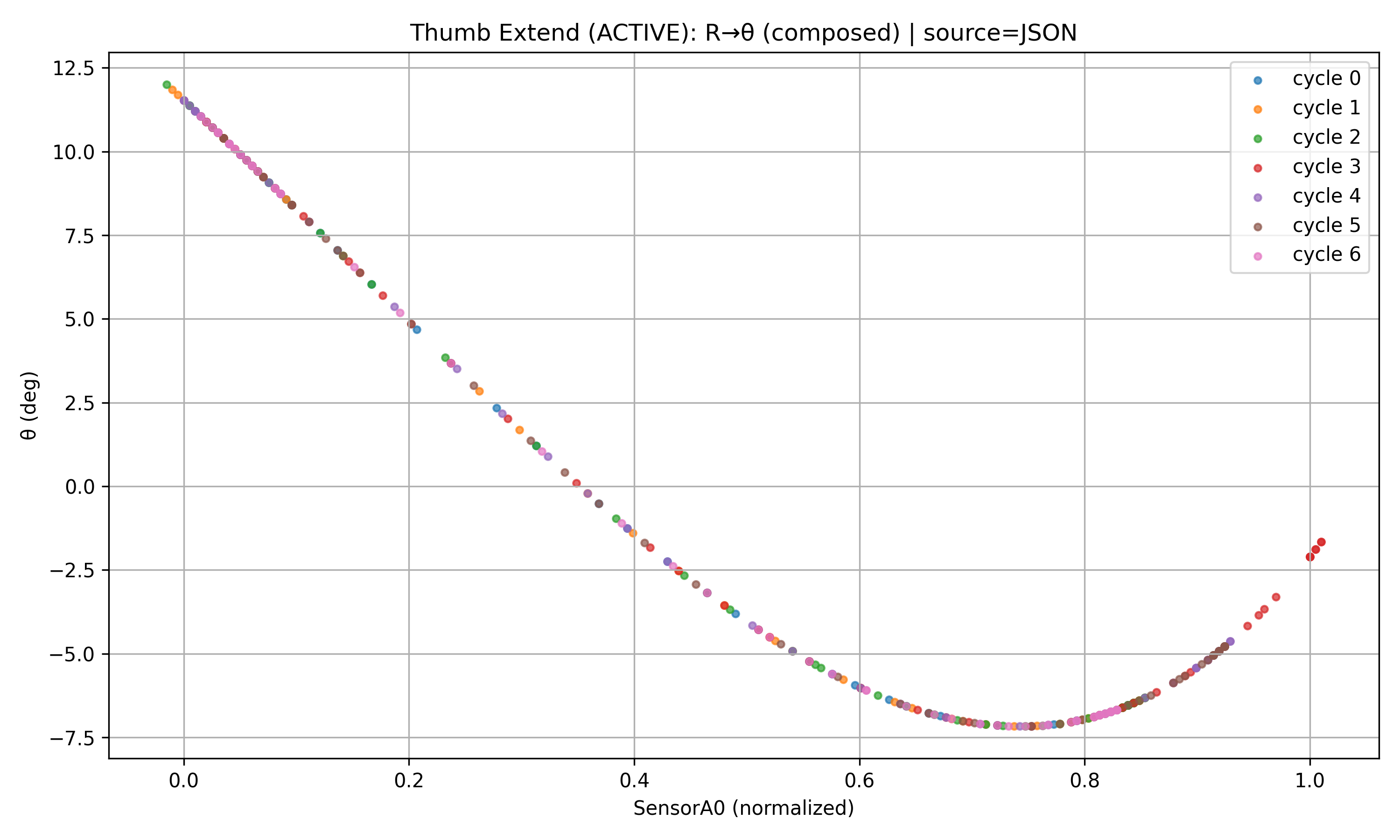
models/thumb/R_theta_compose_active/1/R_theta_composed_ACTIVE_scatter_Extend.png
