JiajunGuo1027/Soft-Glove-Dissertation/models/thumb/R_theta_direct/R_theta_Extend.png

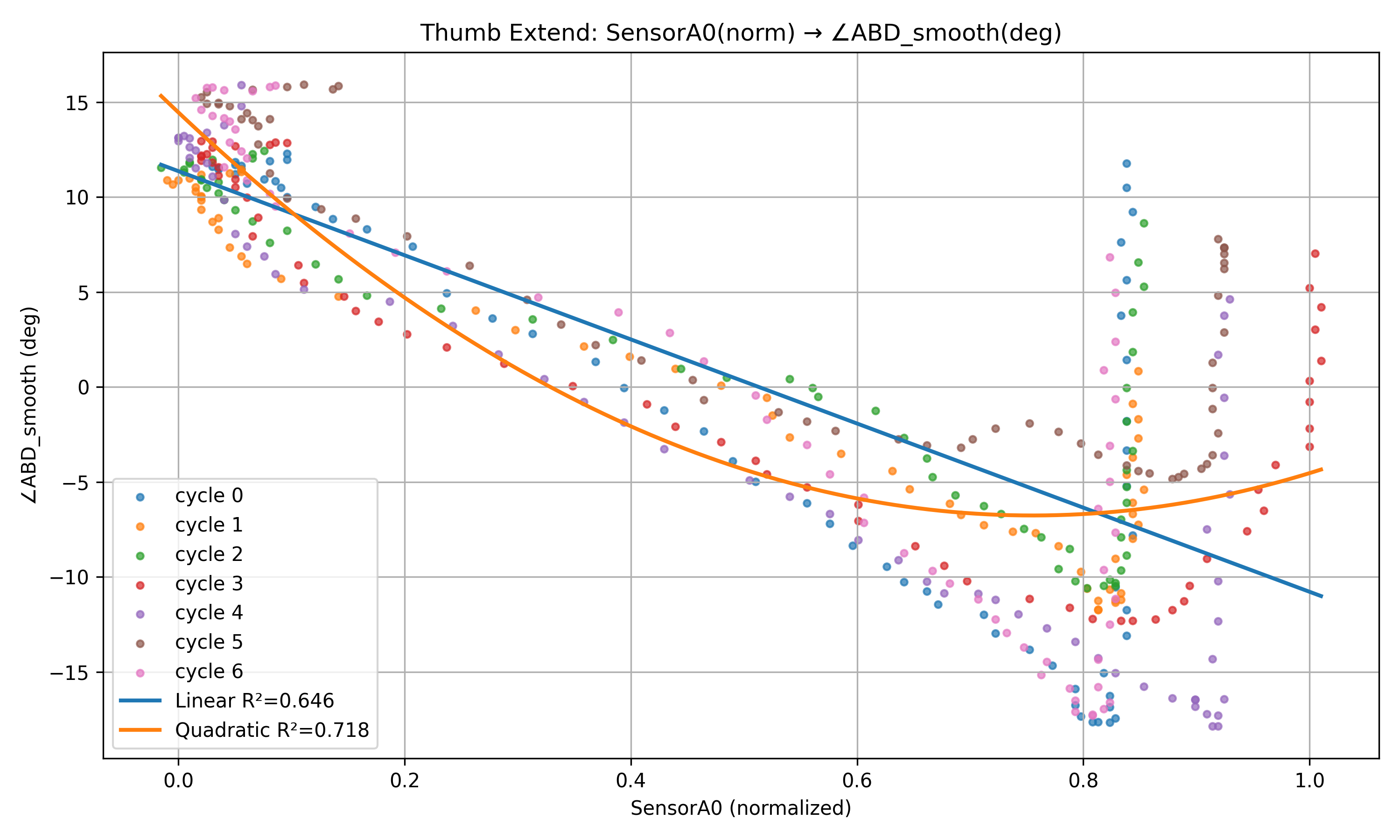
models/thumb/R_theta_direct/R_theta_Extend.png
