JiajunGuo1027/Soft-Glove-Dissertation/models/thumb/R_theta_direct/R_theta_Flex.png

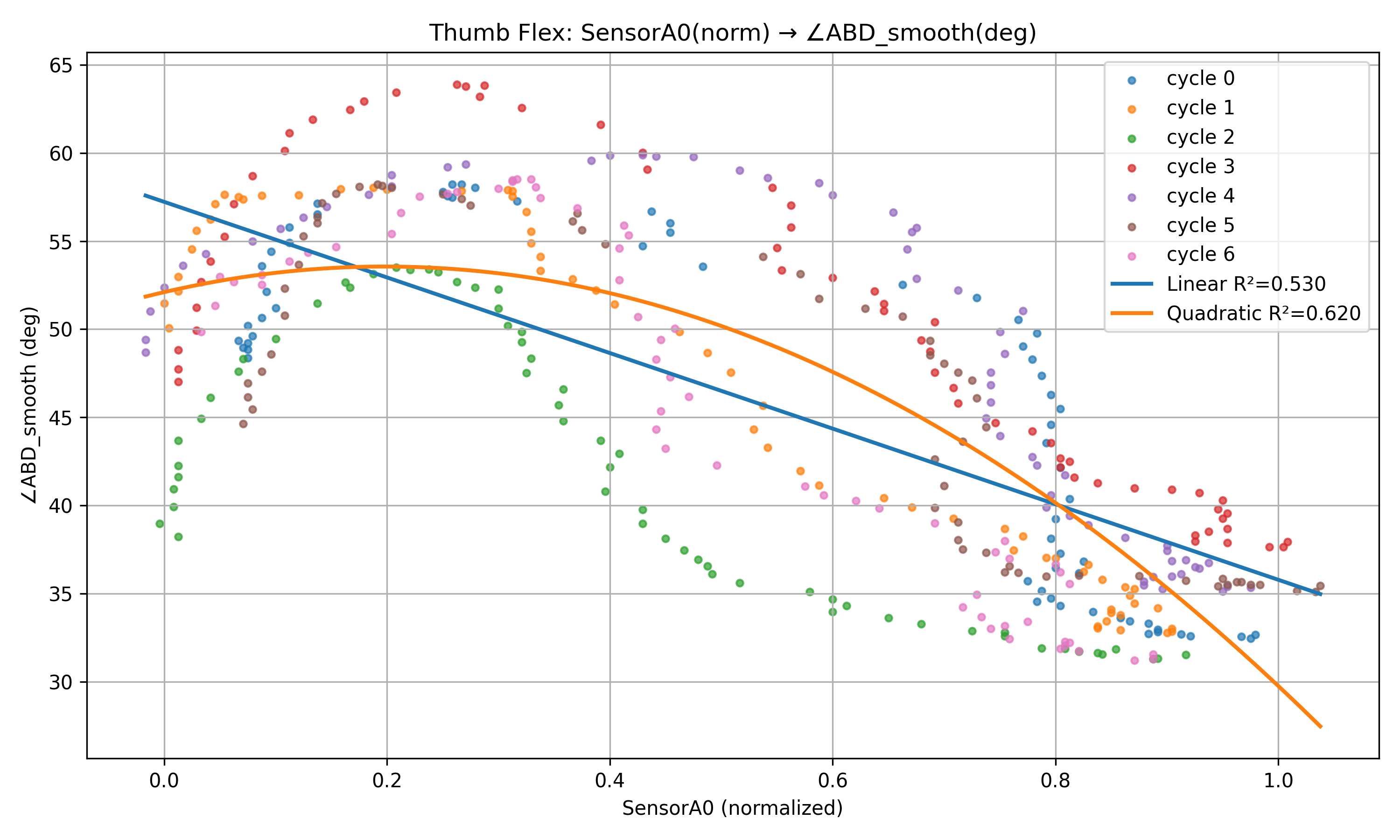
models/thumb/R_theta_direct/R_theta_Flex.png
