JiajunGuo1027/Soft-Glove-Dissertation/output/control_results/timeseries_overview.png

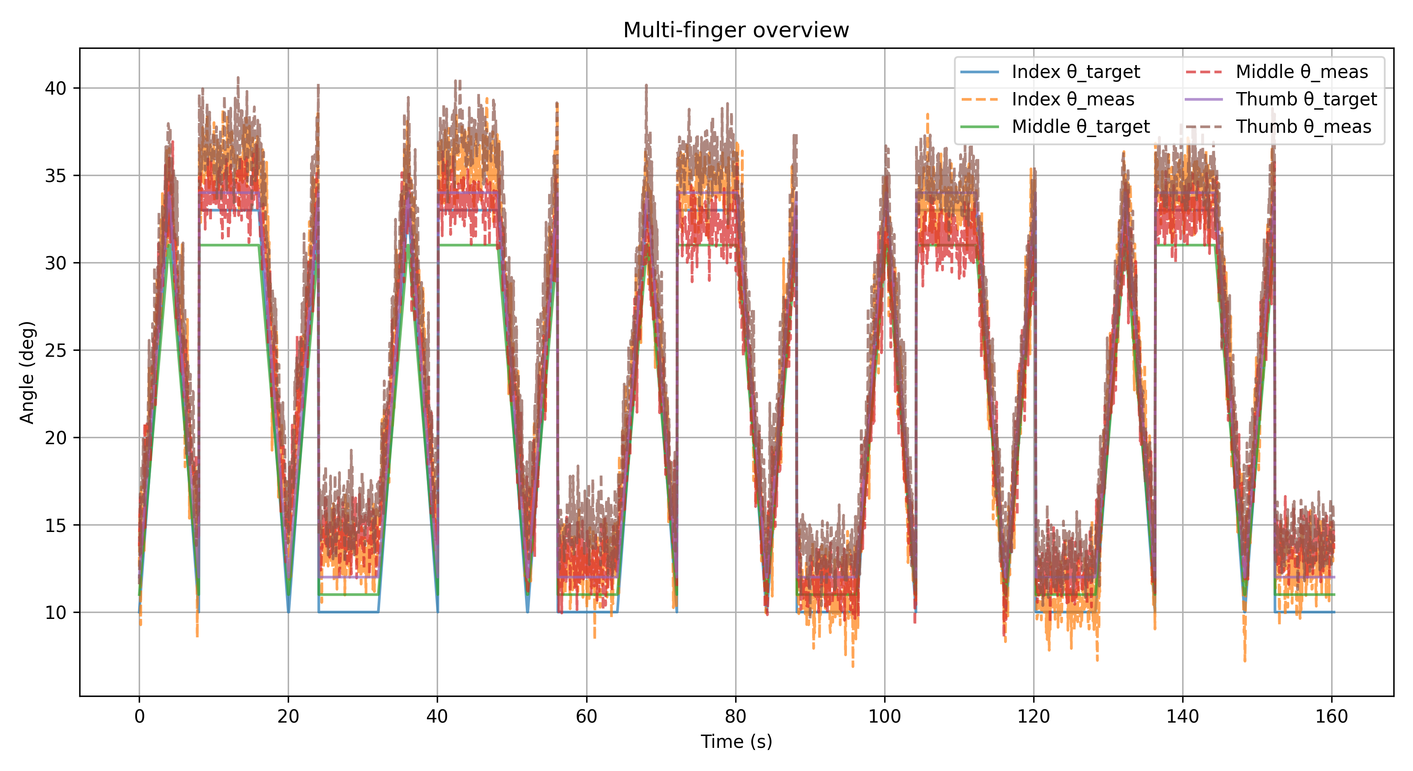
output/control_results/timeseries_overview.png
