JiajunGuo1027/Soft-Glove-Dissertation/output/Ind2/Ind2_keyframe.png

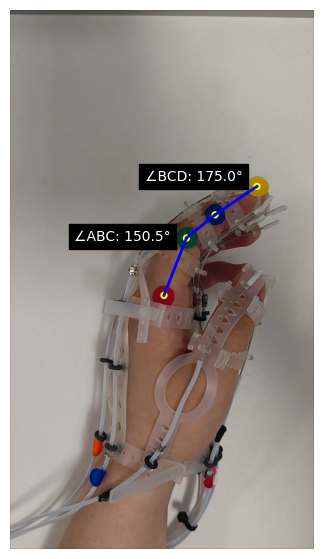
output/Ind2/Ind2_keyframe.png
