JiajunGuo1027/Soft-Glove-Dissertation/output/ind2_sensor2/ind2_sensor2_keyframe.png

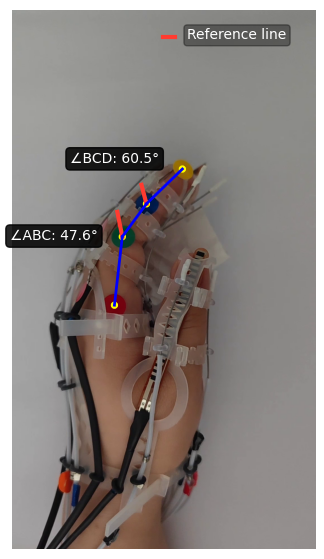
output/ind2_sensor2/ind2_sensor2_keyframe.png
