JiajunGuo1027/Soft-Glove-Dissertation/output/Ind3/Ind3_keyframe.png

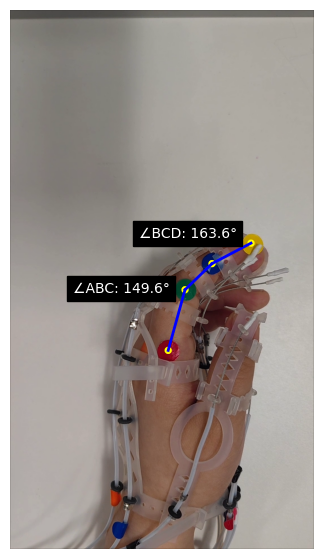
output/Ind3/Ind3_keyframe.png
