JiajunGuo1027/Soft-Glove-Dissertation/output/middle_angles/mid2_keyframe.png

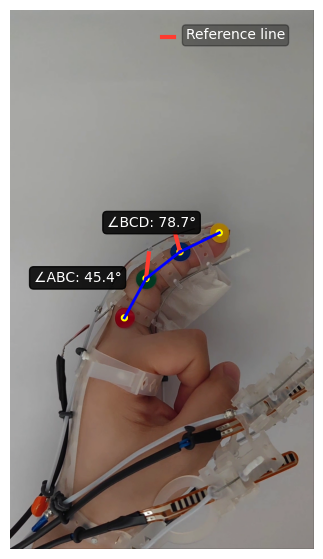
output/middle_angles/mid2_keyframe.png
