JiajunGuo1027/Soft-Glove-Dissertation/output/model0/extend_abc.png

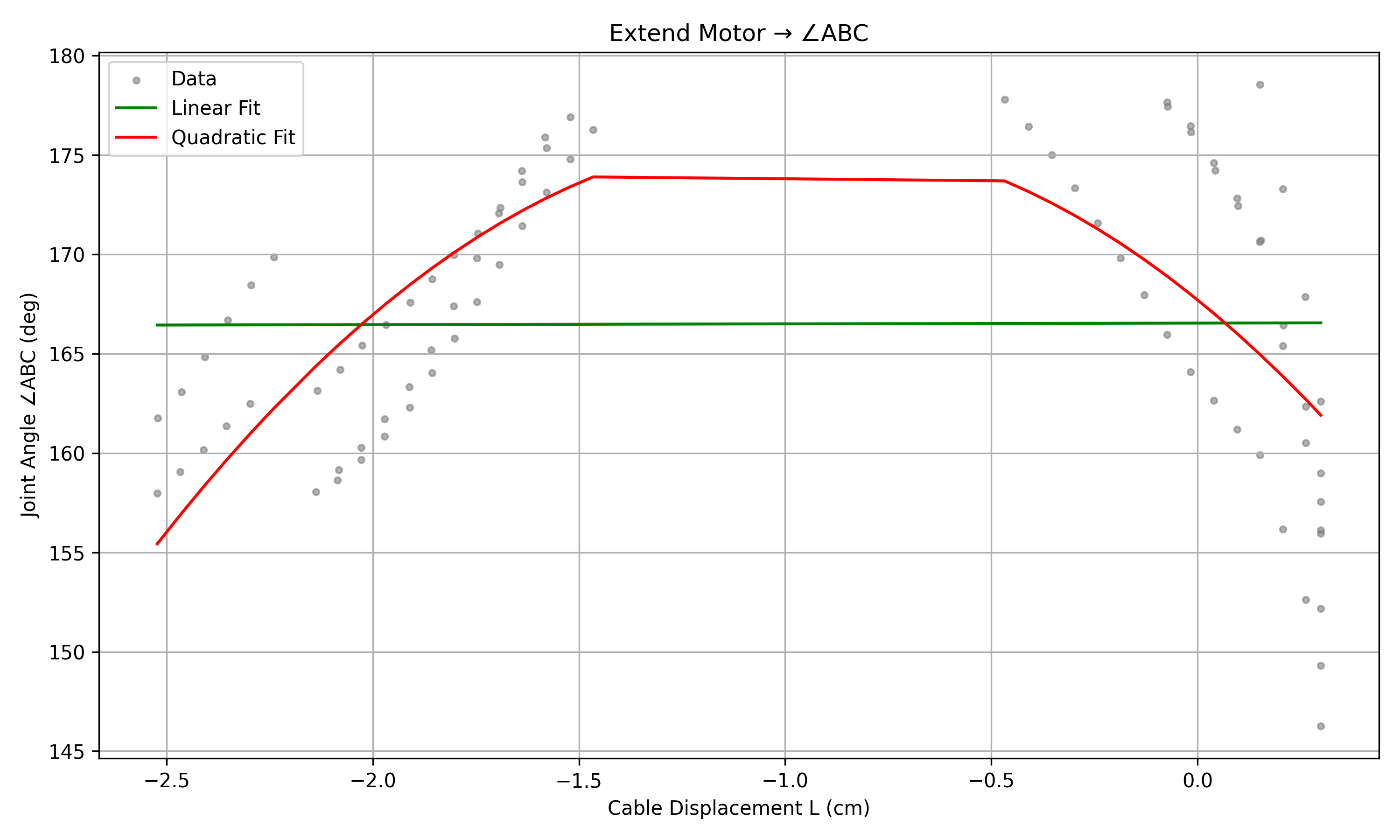
output/model0/extend_abc.png
