JiajunGuo1027/Soft-Glove-Dissertation/output/model0/extend_abc_filtered.png

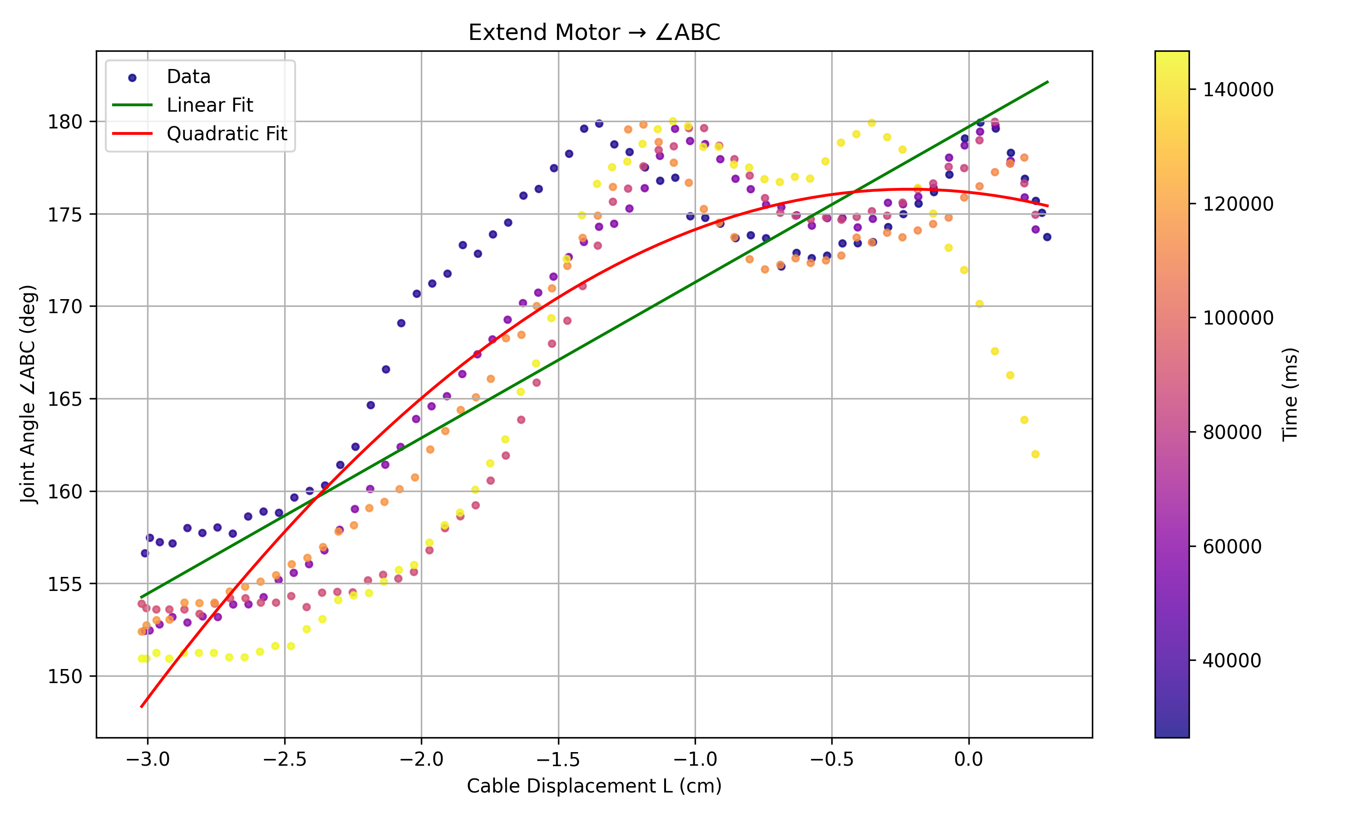
output/model0/extend_abc_filtered.png
