JiajunGuo1027/Soft-Glove-Dissertation/output/model0/extend_bcd.png

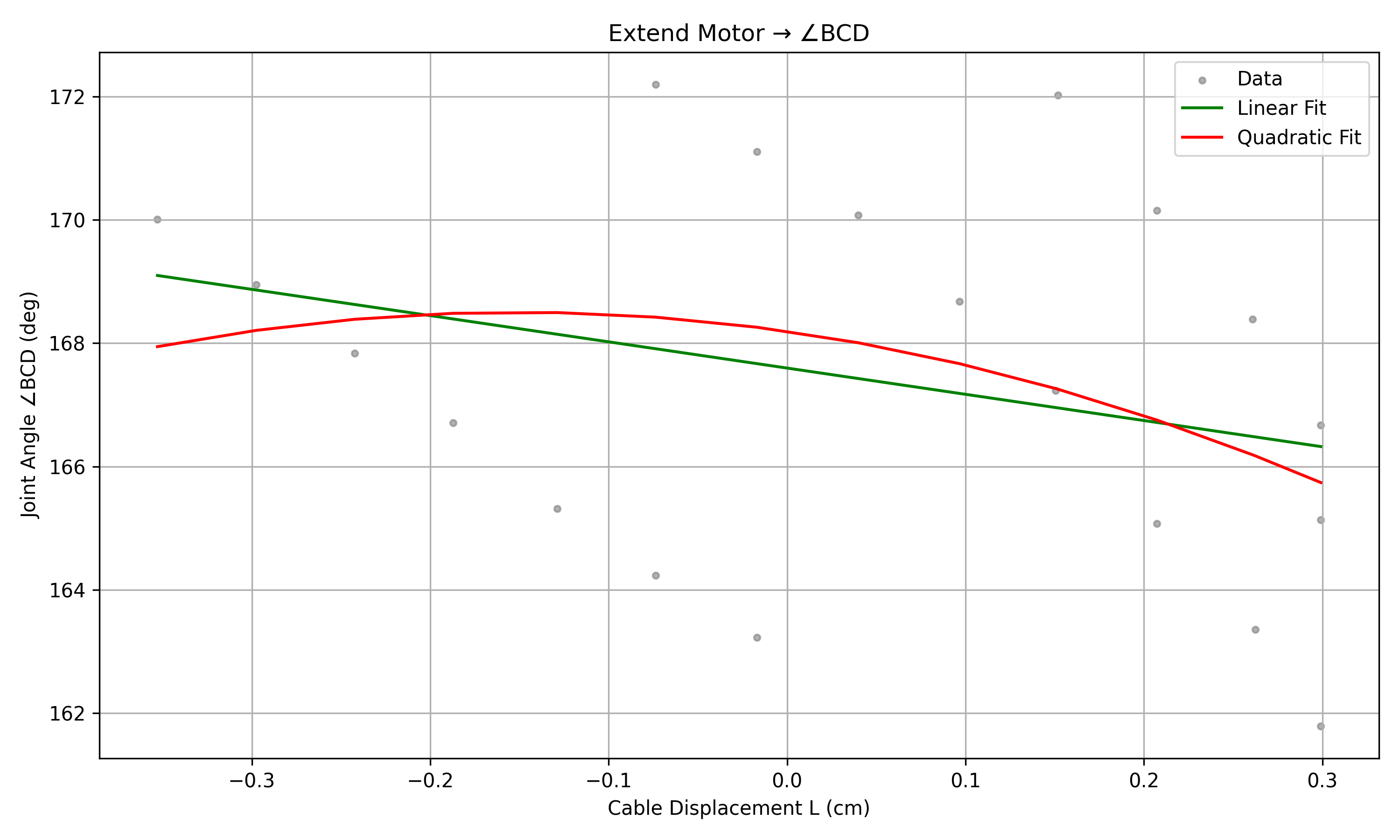
output/model0/extend_bcd.png
