JiajunGuo1027/Soft-Glove-Dissertation/output/model0/extend_bcd_filtered.png

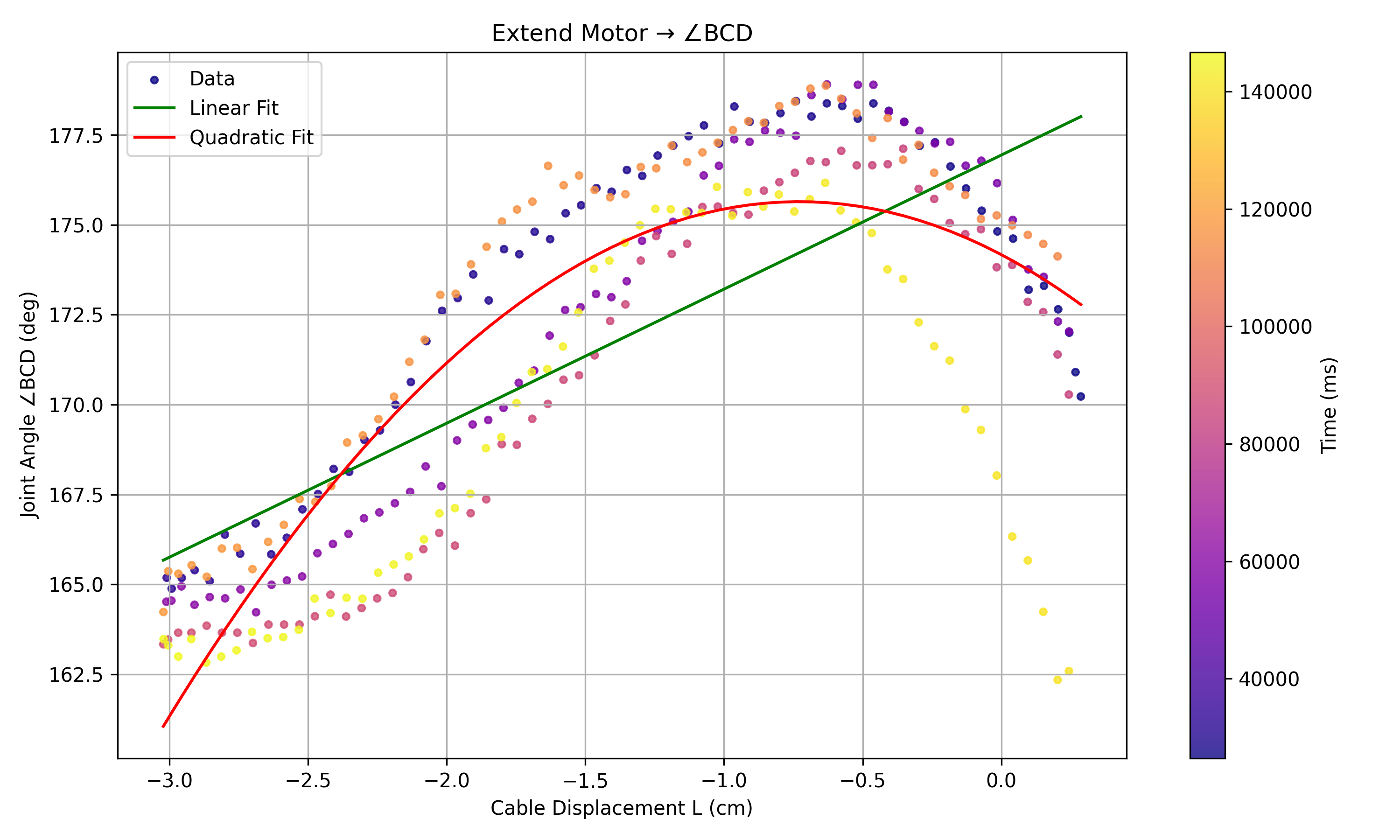
output/model0/extend_bcd_filtered.png
