JiajunGuo1027/Soft-Glove-Dissertation/output/model0/flex_abc.png

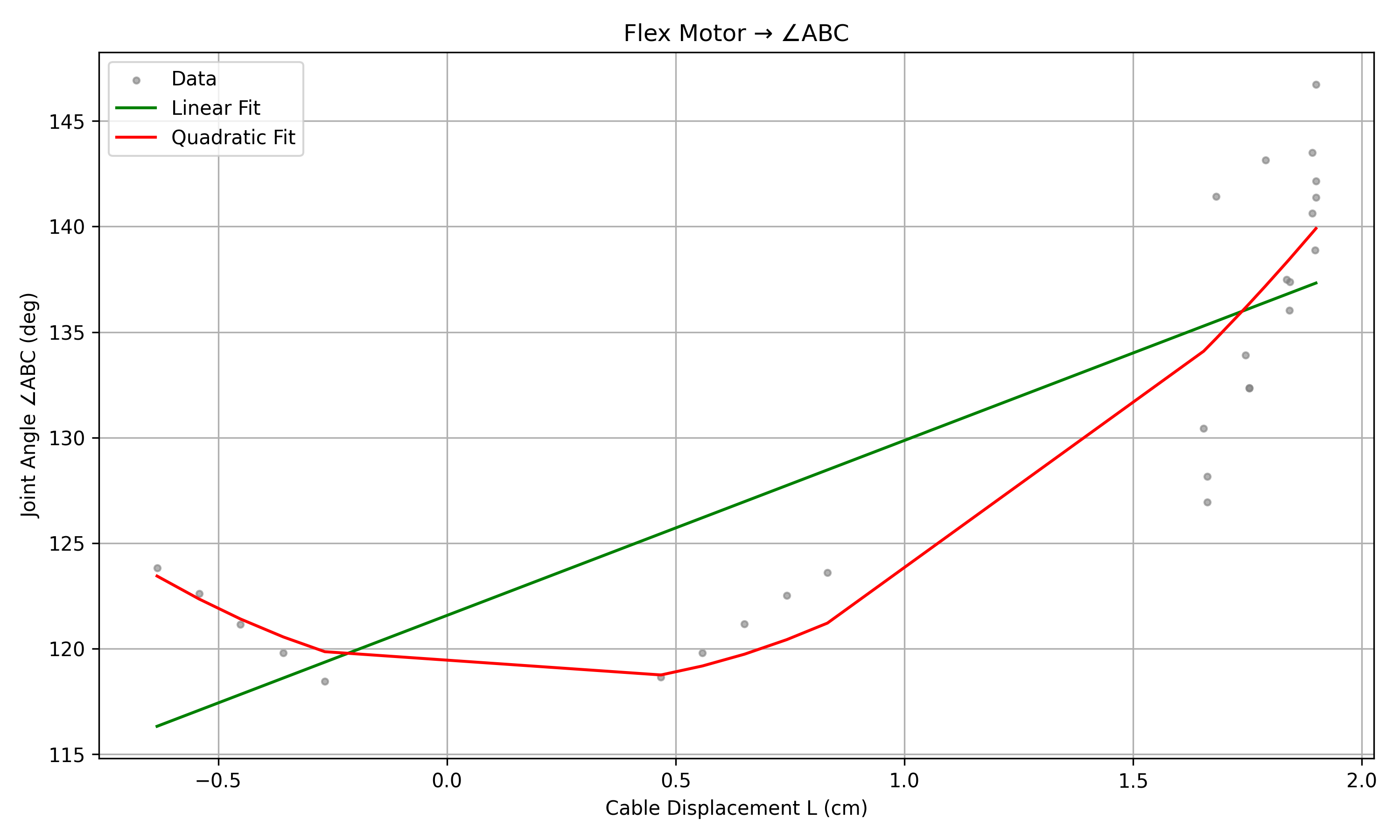
output/model0/flex_abc.png
