JiajunGuo1027/Soft-Glove-Dissertation/output/model0/flex_bcd_filtered.png

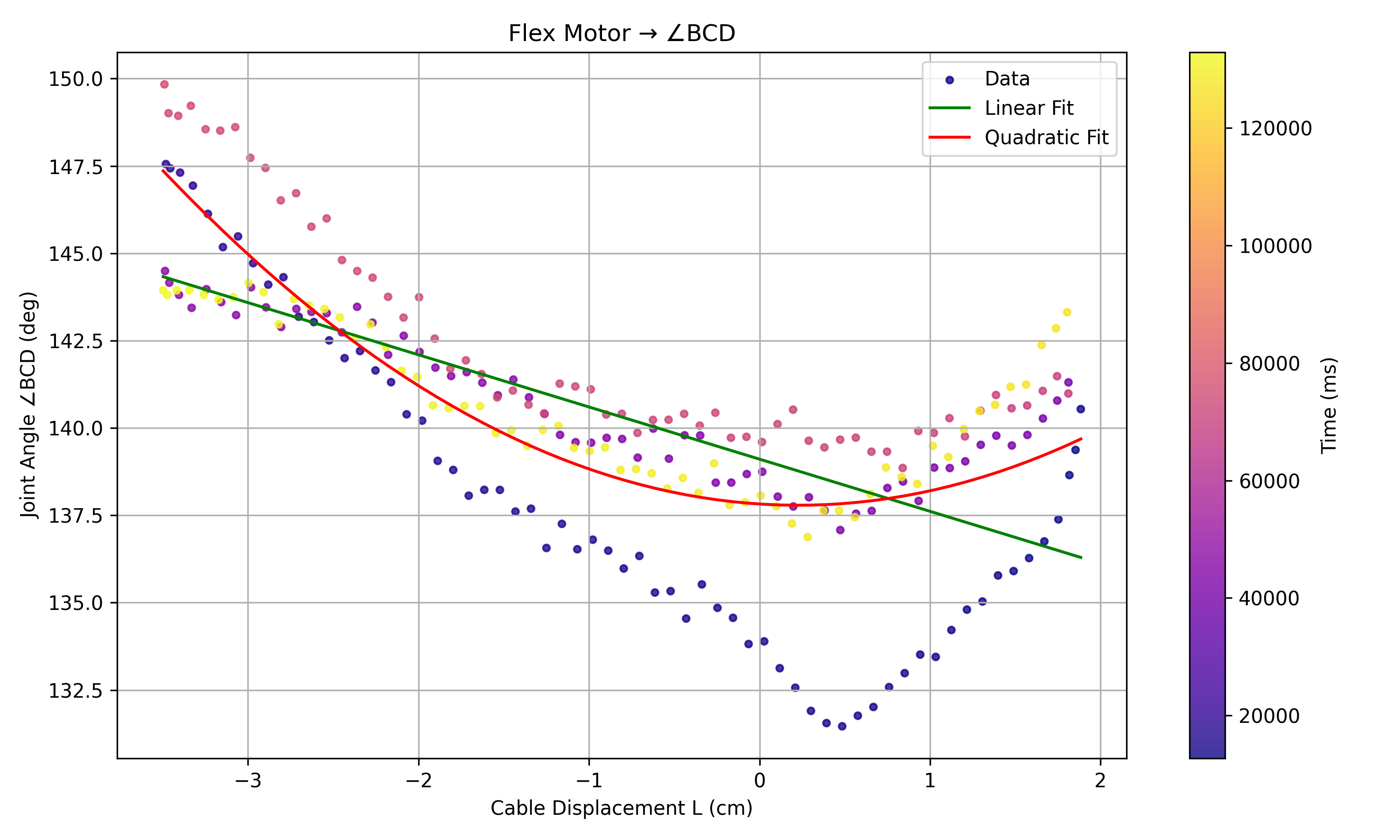
output/model0/flex_bcd_filtered.png
