JiajunGuo1027/Soft-Glove-Dissertation/output/model0/ind2_extend_abc_cycles.png

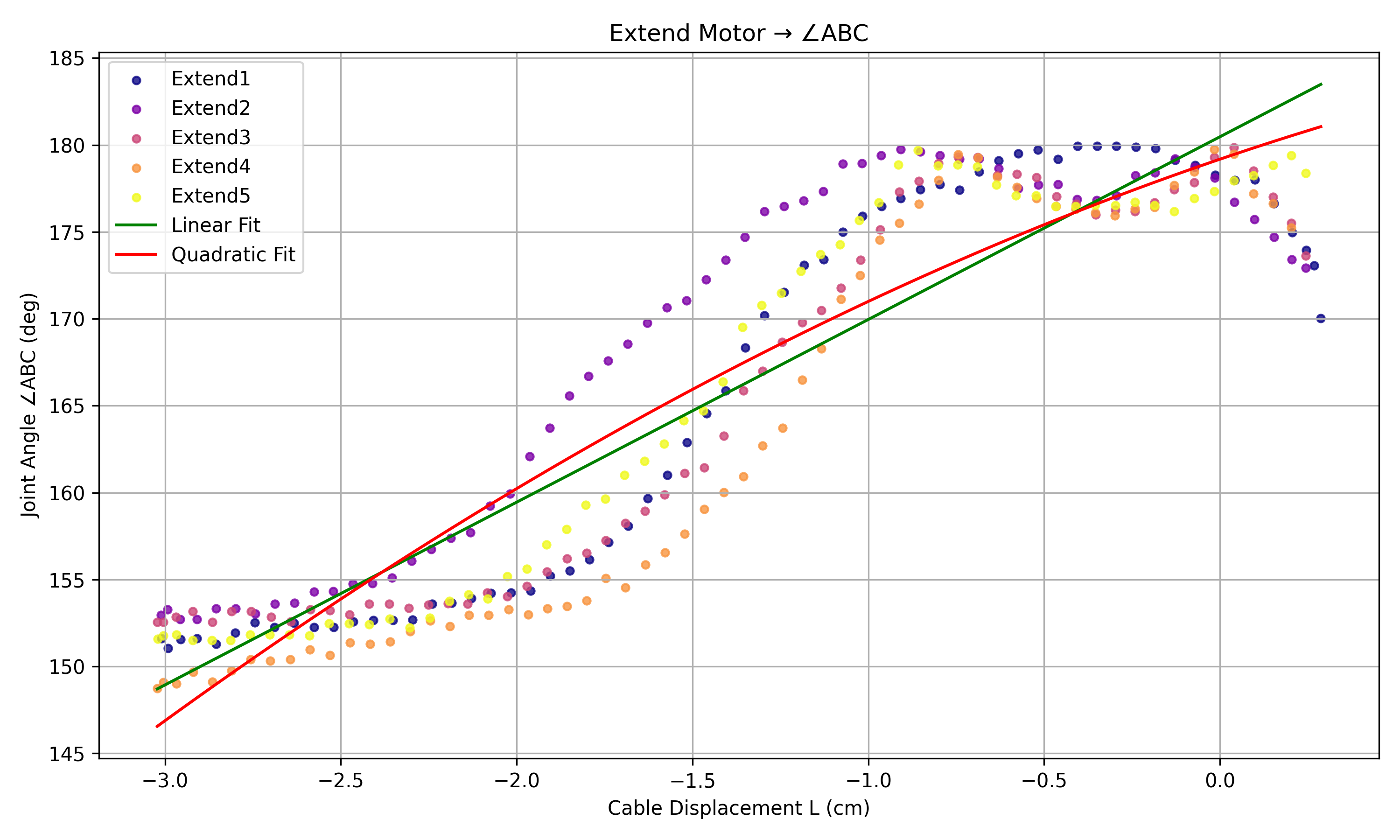
output/model0/ind2_extend_abc_cycles.png
