JiajunGuo1027/Soft-Glove-Dissertation/output/model0/ind2_extend_bcd_cycles.png

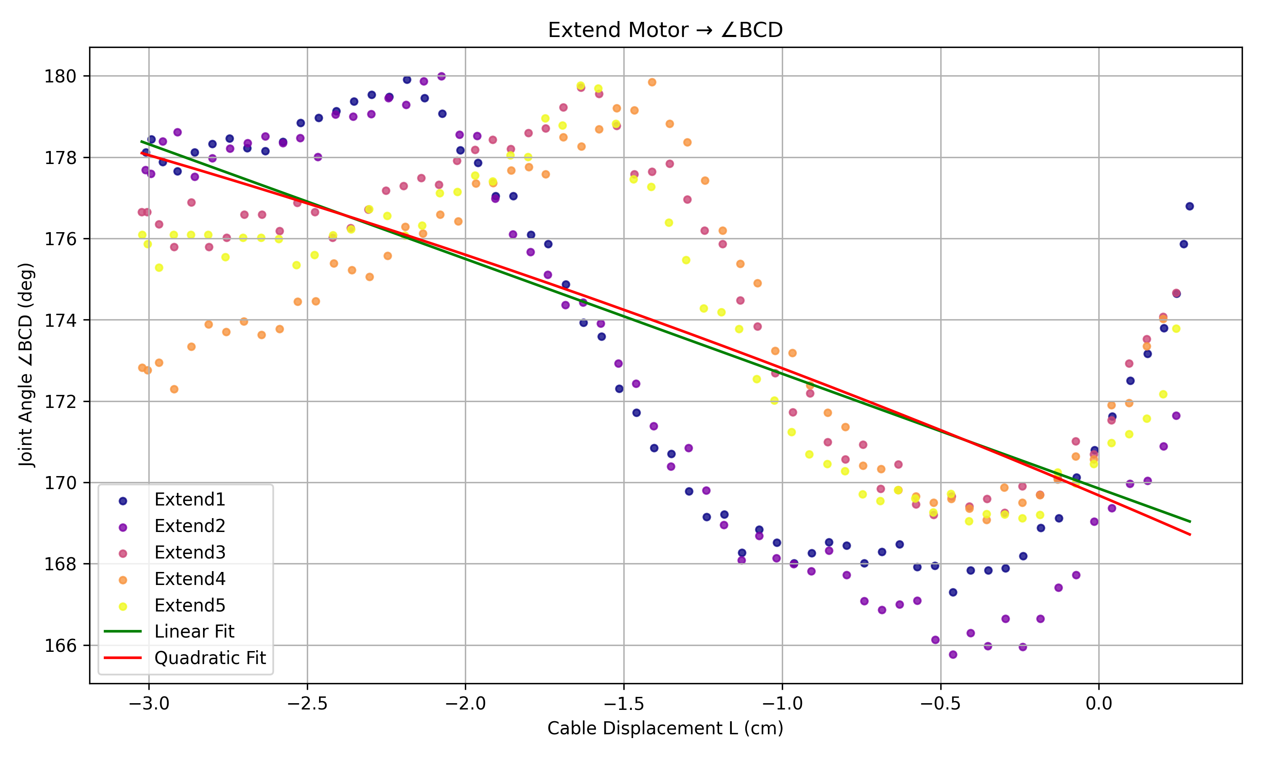
output/model0/ind2_extend_bcd_cycles.png
