JiajunGuo1027/Soft-Glove-Dissertation/output/model0/ind3_flex_abc_cycles.png

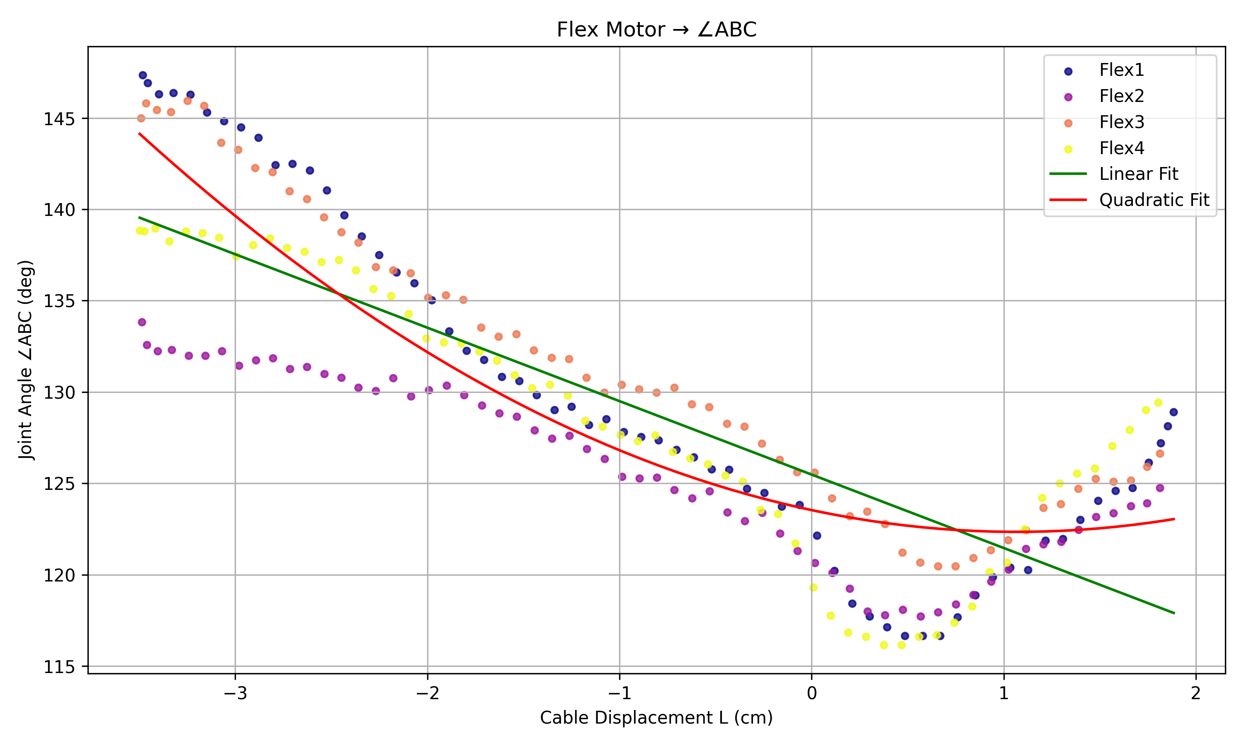
output/model0/ind3_flex_abc_cycles.png
