JiajunGuo1027/Soft-Glove-Dissertation/output/model0/L_theta_mapping.png

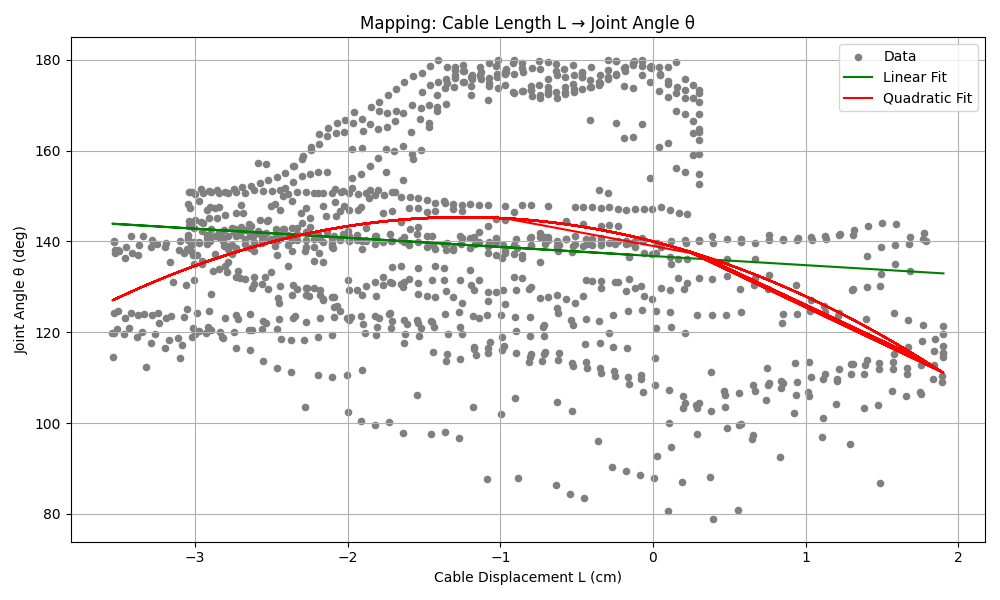
output/model0/L_theta_mapping.png
