JiajunGuo1027/Soft-Glove-Dissertation/output/model0/plot_extend_bcd.png

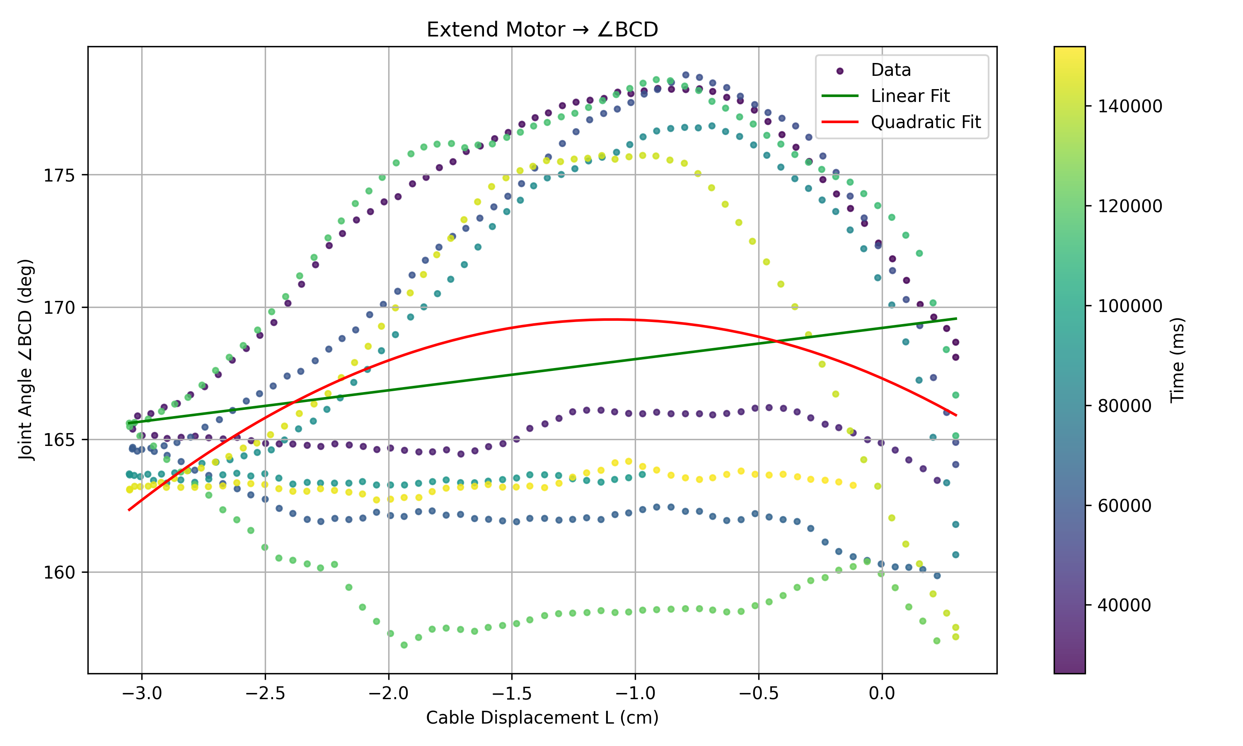
output/model0/plot_extend_bcd.png
