JiajunGuo1027/Soft-Glove-Dissertation/output/model0/plot_flex_abc.png

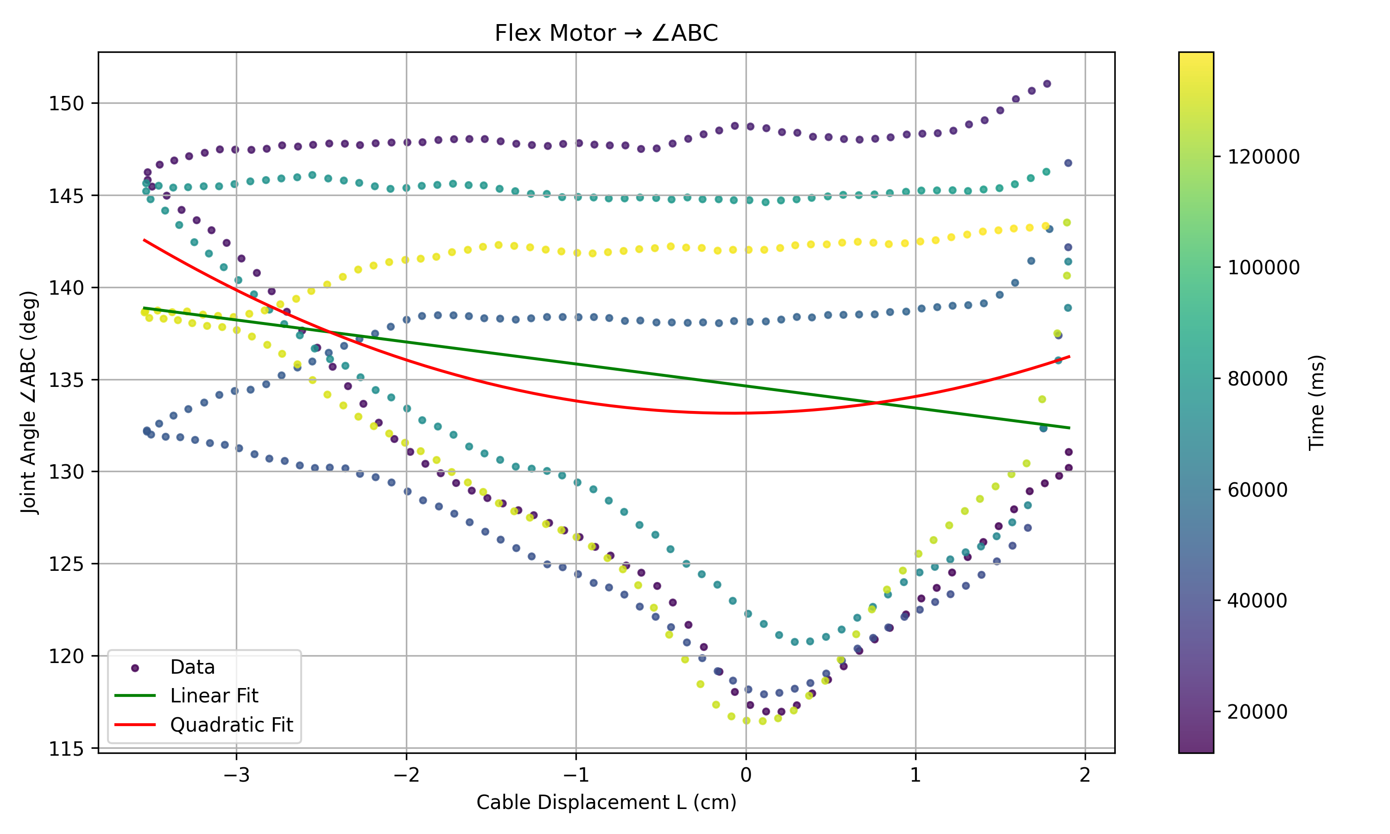
output/model0/plot_flex_abc.png
