JiajunGuo1027/Soft-Glove-Dissertation/output/model0/plot_flex_bcd.png

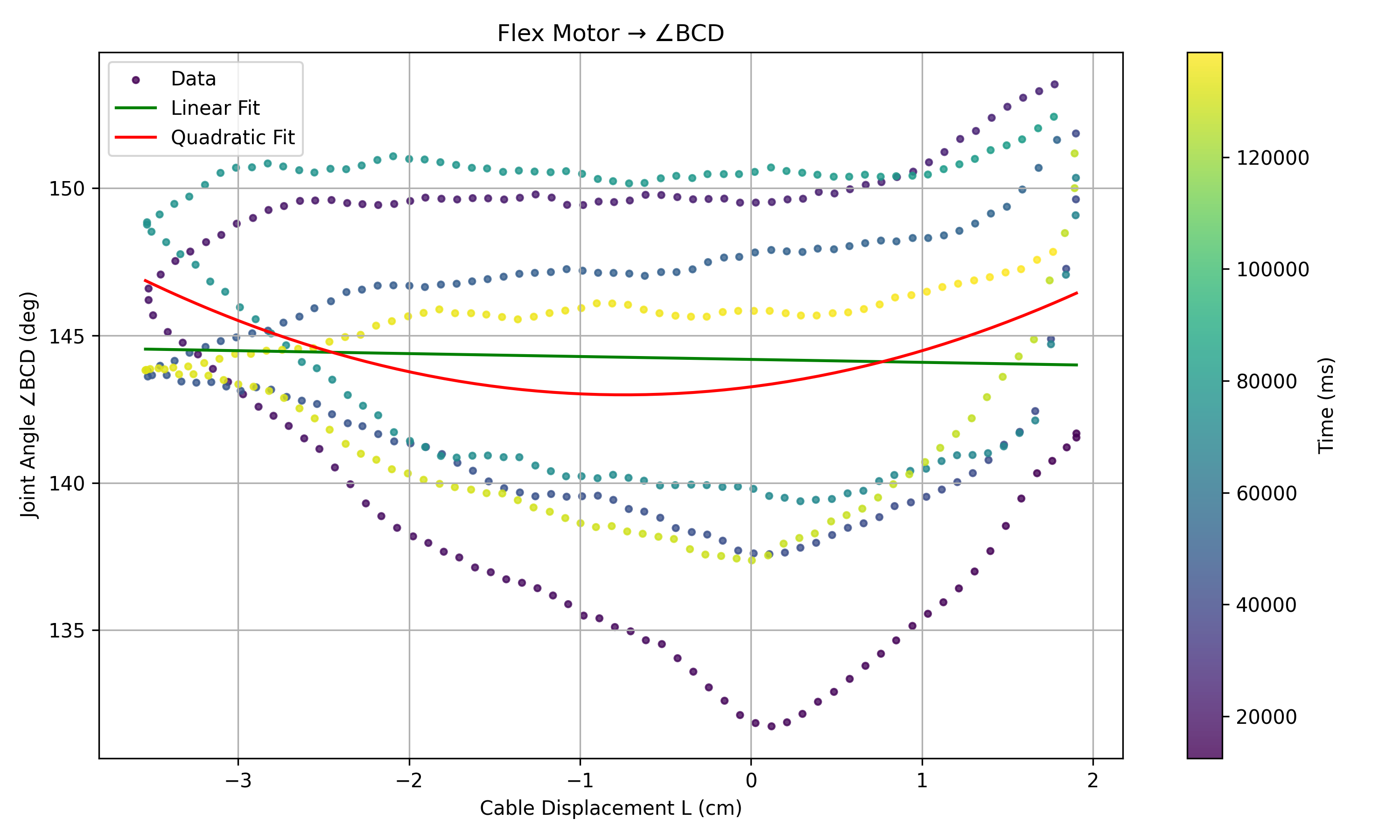
output/model0/plot_flex_bcd.png
