JiajunGuo1027/Soft-Glove-Dissertation/output/model0/split_R2_MSE.png

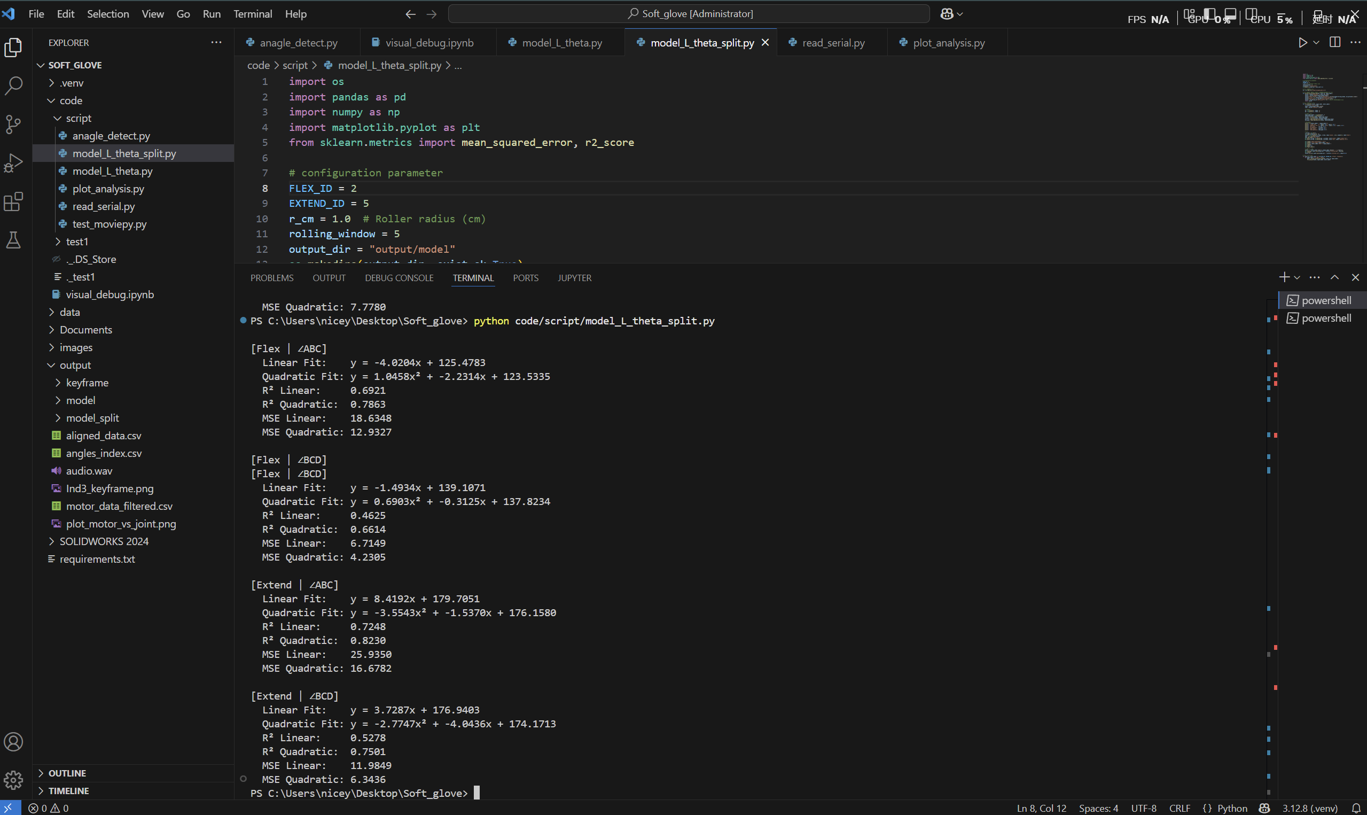
output/model0/split_R2_MSE.png
