JiajunGuo1027/Soft-Glove-Dissertation/output/thumb_angles/thumb_keyframe.png

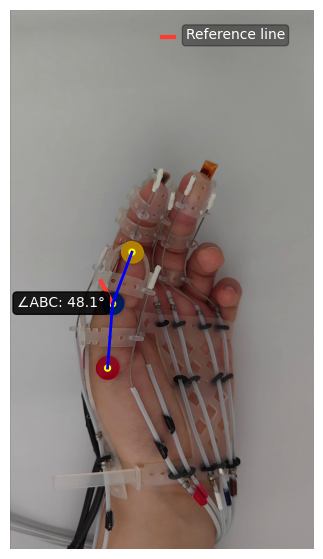
output/thumb_angles/thumb_keyframe.png
