JiajunGuo1027/Soft-Glove-Dissertation/tensile/figs/bar_disp_1N.png

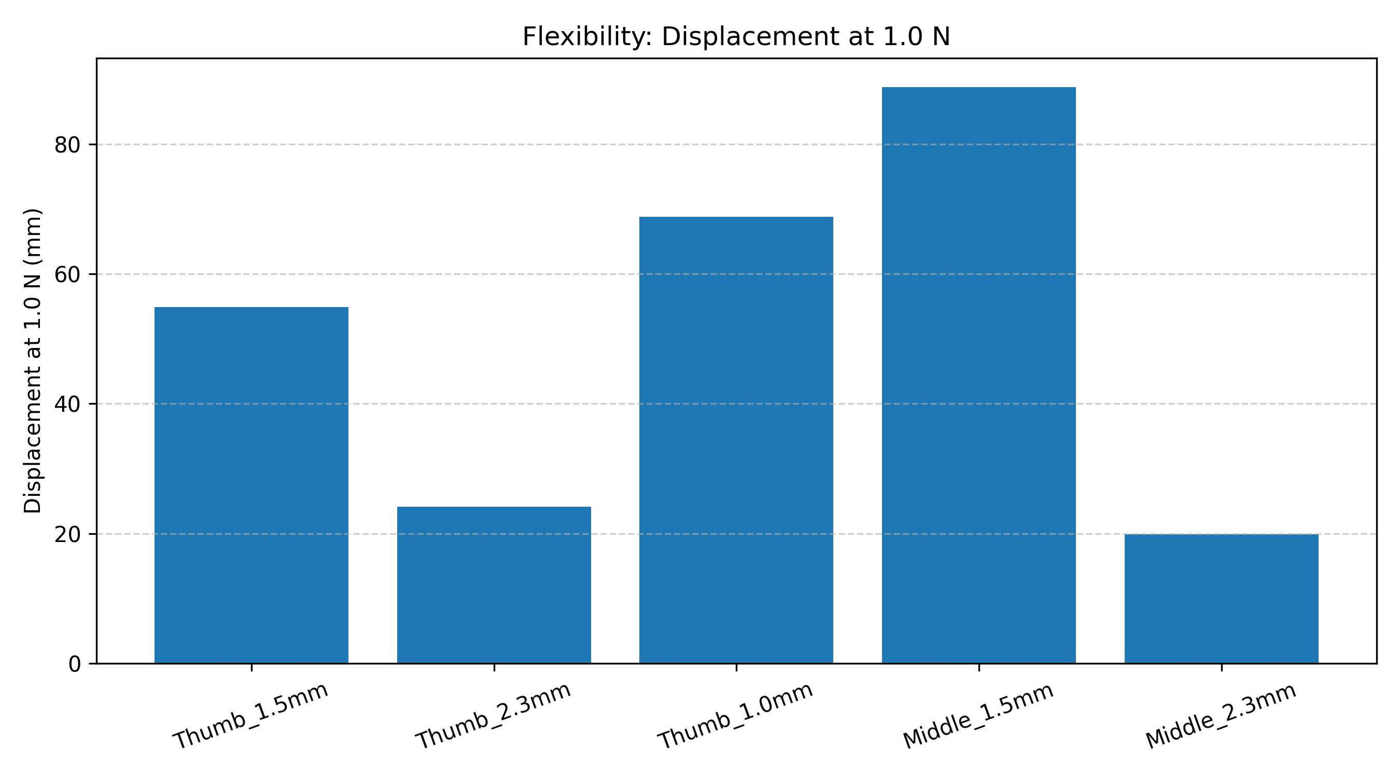
tensile/figs/bar_disp_1N.png
