JiajunGuo1027/Soft-Glove-Dissertation/tensile/figs/curve_tangent_stiffness.png

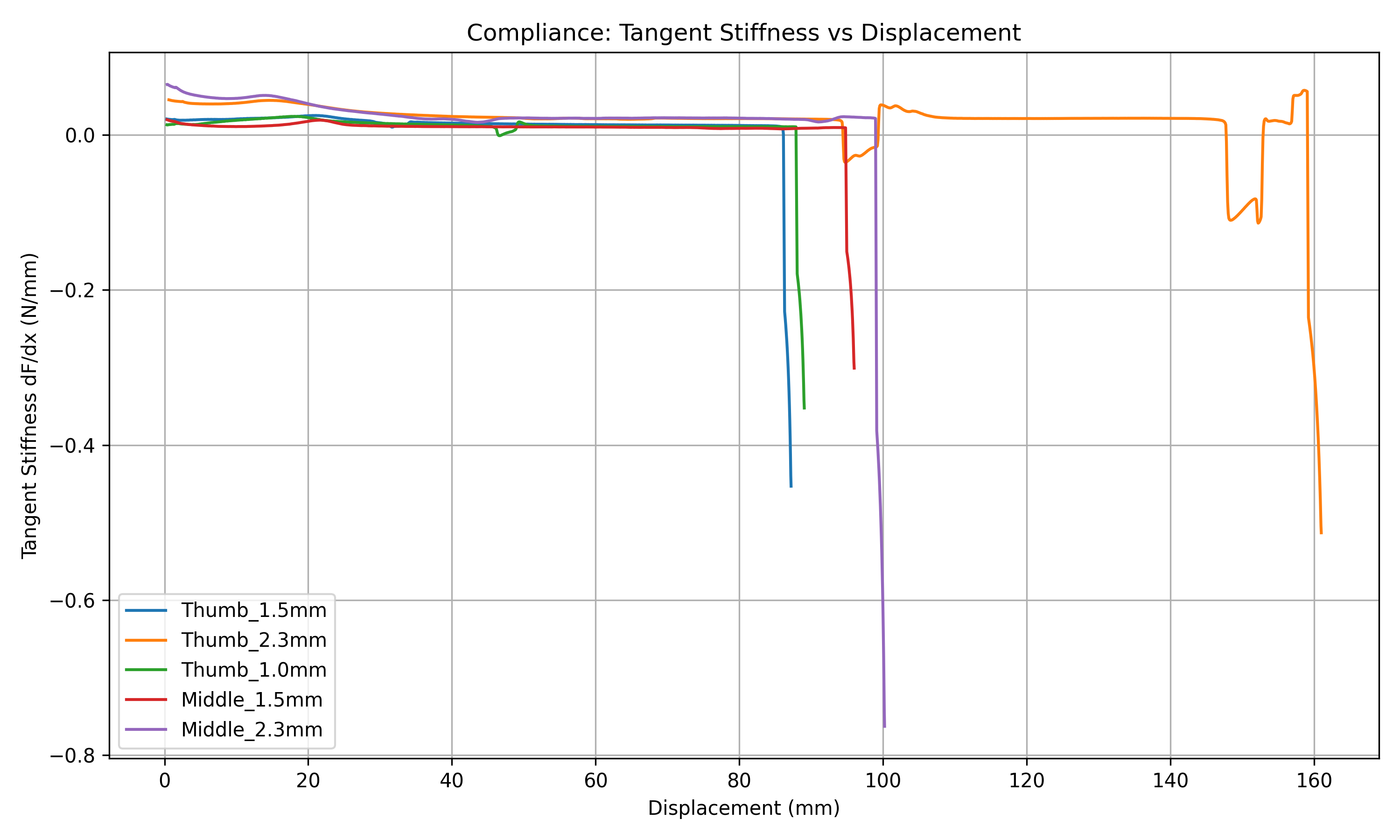
tensile/figs/curve_tangent_stiffness.png
