JiajunGuo1027/Soft-Glove-Dissertation/tensile/figs/force_displacement_all.png

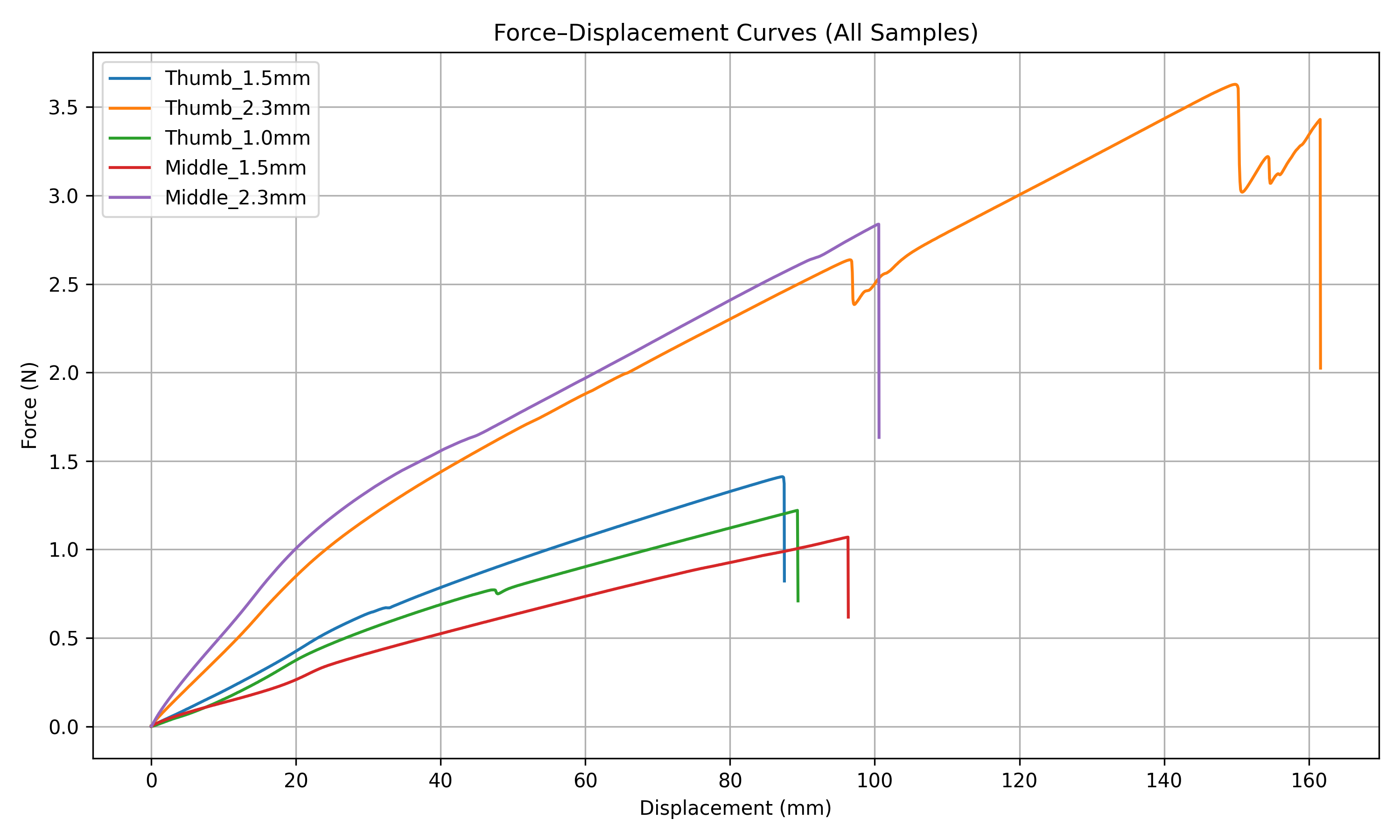
tensile/figs/force_displacement_all.png
