JiajunGuo1027/Soft-Glove-Dissertation/tensile/figs/radar_disp_multi_force.png

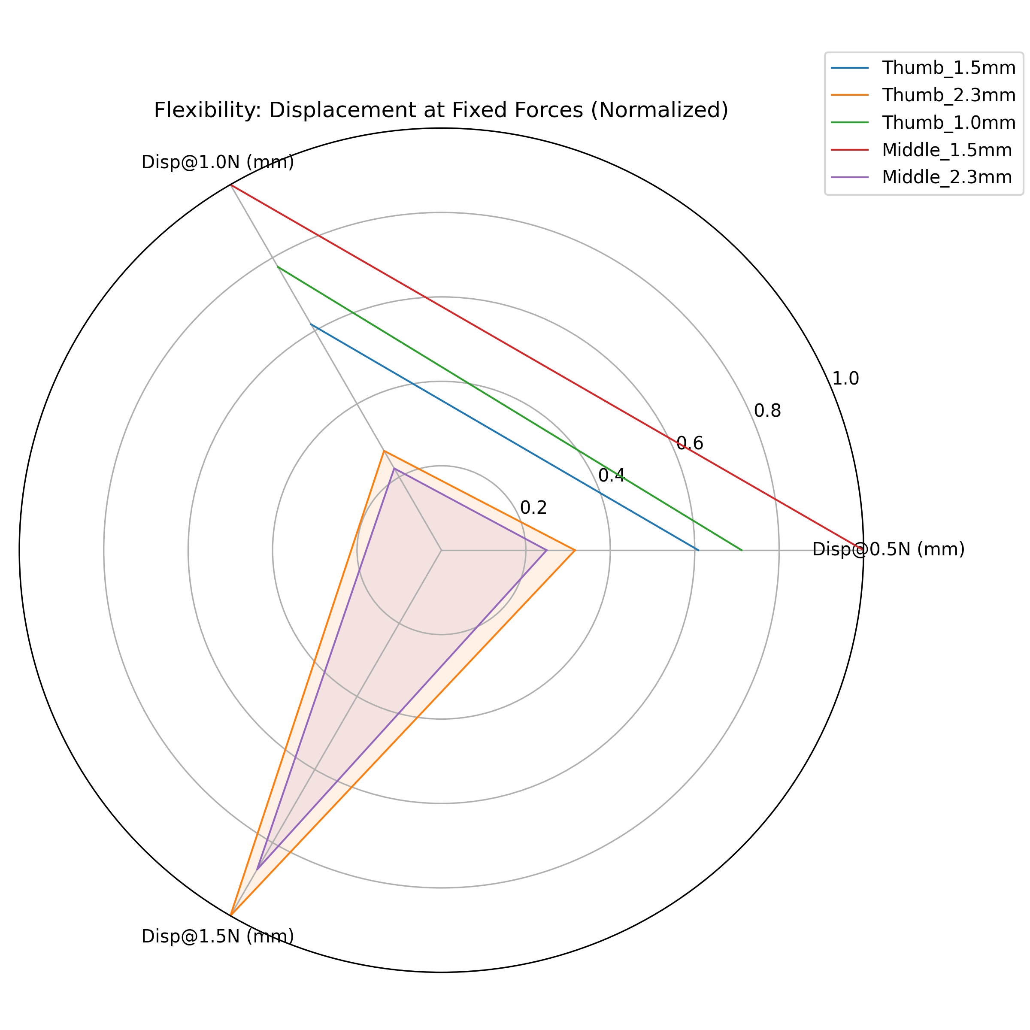
tensile/figs/radar_disp_multi_force.png
