JiajunGuo1027/Soft-Glove-Dissertation/tensile/figs/scatter_pareto.png

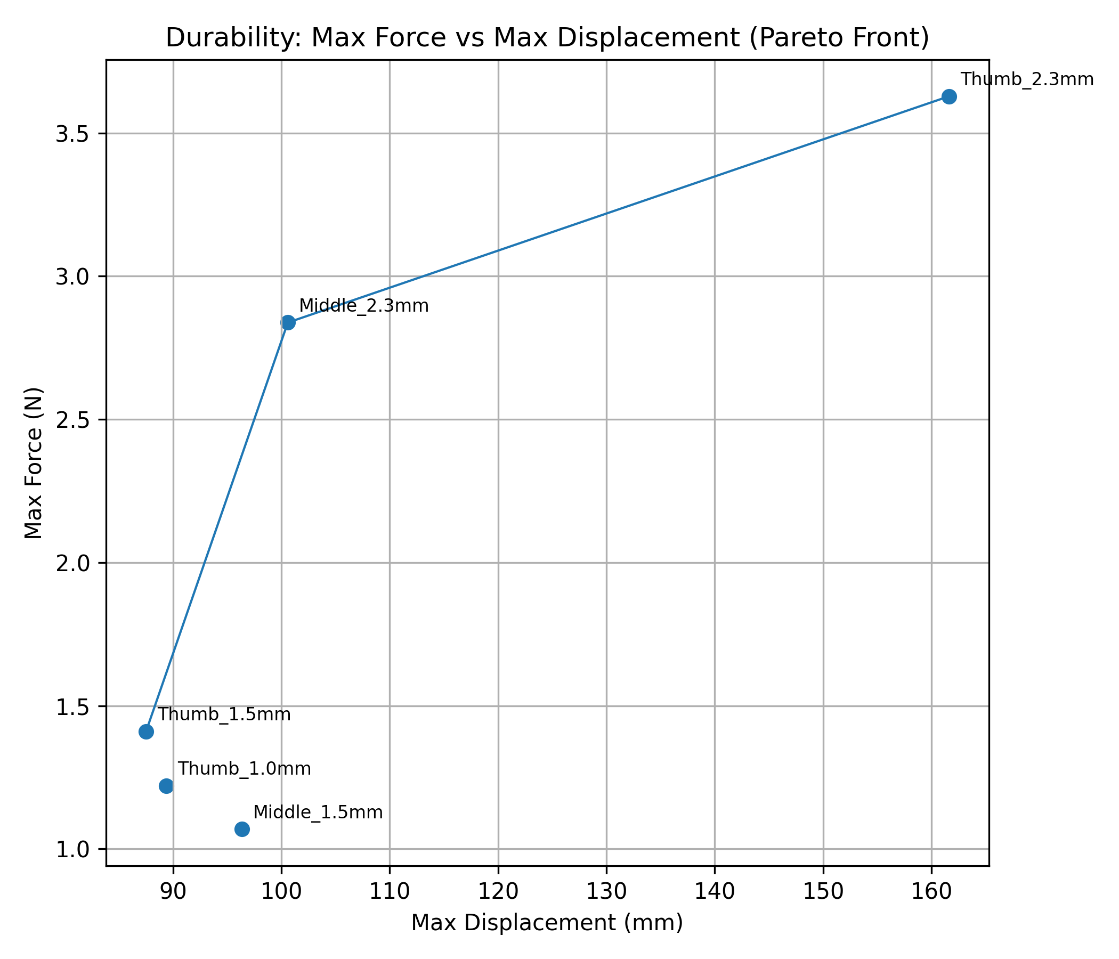
tensile/figs/scatter_pareto.png
