JiajunGuo1027/Soft-Glove-Dissertation/SOLIDWORKS 2024/LaserCut1/finger_lower_longer _3D.DXF

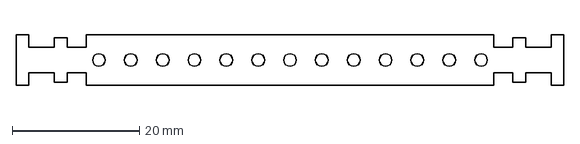
[picture p169: CAD file, 2025-08-06]
SOLIDWORKS 2024/LaserCut1/finger_lower_longer _3D.DXF
86.0 x 8.00 mm
