JiajunGuo1027/Soft-Glove-Dissertation/SOLIDWORKS 2024/LaserCut2/1_palm2.DXF

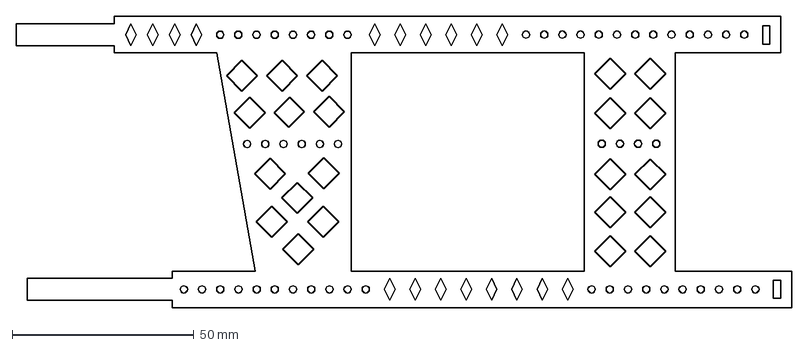
[picture p170: CAD file, 2025-08-06]
SOLIDWORKS 2024/LaserCut2/1_palm2.DXF
213.1 x 80.0 mm
