JiajunGuo1027/Soft-Glove-Dissertation/SOLIDWORKS 2024/Glove_final_design/shoter2.SLDPRT

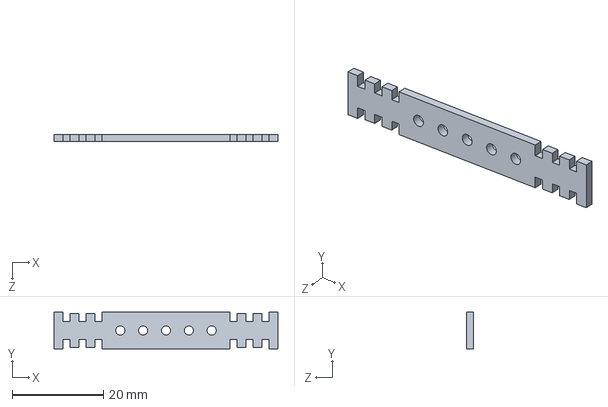
[picture p171: CAD file, 2025-08-06]
SOLIDWORKS 2024/Glove_final_design/shoter2.SLDPRT
49.0 x 8.00 x 1.50 mm
