JiajunGuo1027/Soft-Glove-Dissertation/SOLIDWORKS 2024/LaserCut1/palm1_3D.DXF

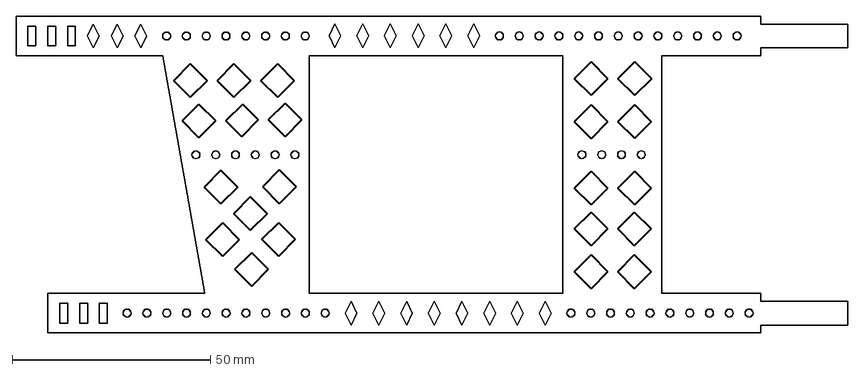
[picture p172: CAD file, 2025-08-06]
SOLIDWORKS 2024/LaserCut1/palm1_3D.DXF
210.0 x 80.0 mm
