JiajunGuo1027/Soft-Glove-Dissertation/SOLIDWORKS 2024/LaserCut2/1_index2.DXF

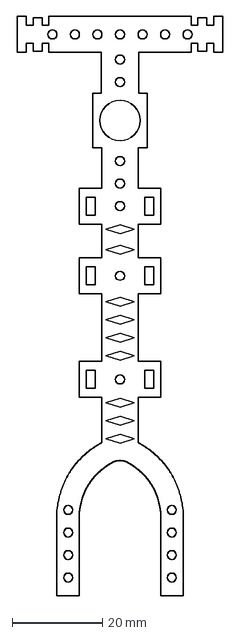
[picture p173: CAD file, 2025-08-06]
SOLIDWORKS 2024/LaserCut2/1_index2.DXF
45.6 x 128.6 mm
