JiajunGuo1027/Soft-Glove-Dissertation/SOLIDWORKS 2024/thumb_upper_3D.SLDPRT

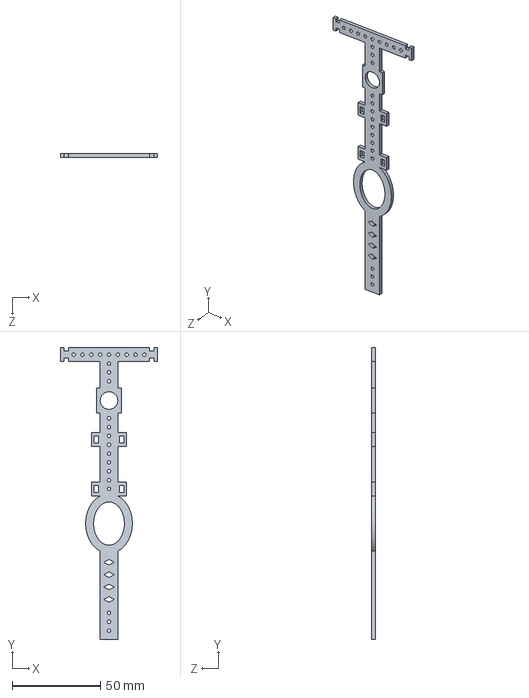
[picture p174: CAD file, 2025-08-06]
SOLIDWORKS 2024/thumb_upper_3D.SLDPRT
55.0 x 165.1 x 2.00 mm
