JiajunGuo1027/Soft-Glove-Dissertation/SOLIDWORKS 2024/finger_lower_longer _3D.SLDPRT

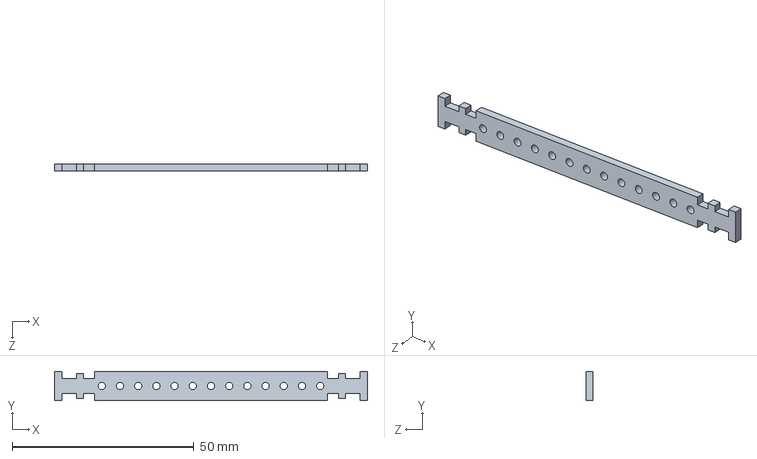
[picture p175: CAD file, 2025-08-06]
SOLIDWORKS 2024/finger_lower_longer _3D.SLDPRT
86.0 x 8.00 x 2.00 mm
