JiajunGuo1027/Soft-Glove-Dissertation/SOLIDWORKS 2024/Glove_final_design/longer2.SLDPRT

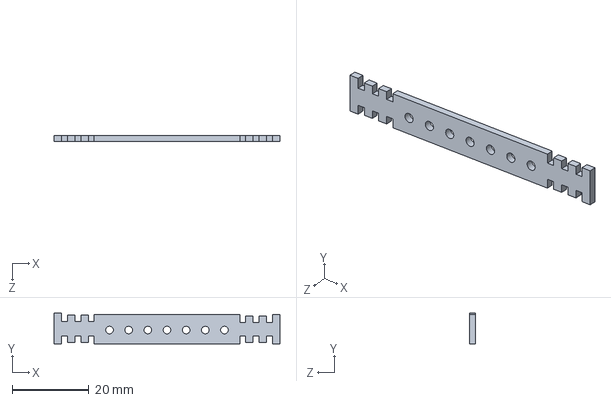
[picture p176: CAD file, 2025-08-06]
SOLIDWORKS 2024/Glove_final_design/longer2.SLDPRT
59.0 x 8.00 x 1.50 mm
