JiajunGuo1027/Soft-Glove-Dissertation/SOLIDWORKS 2024/LaserCut2/1_middle2.DXF

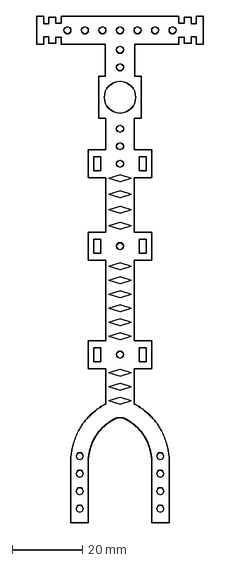
[picture p177: CAD file, 2025-08-06]
SOLIDWORKS 2024/LaserCut2/1_middle2.DXF
47.6 x 144.6 mm
