JiajunGuo1027/Soft-Glove-Dissertation/SOLIDWORKS 2024/Glove_final_design/palm2.SLDPRT

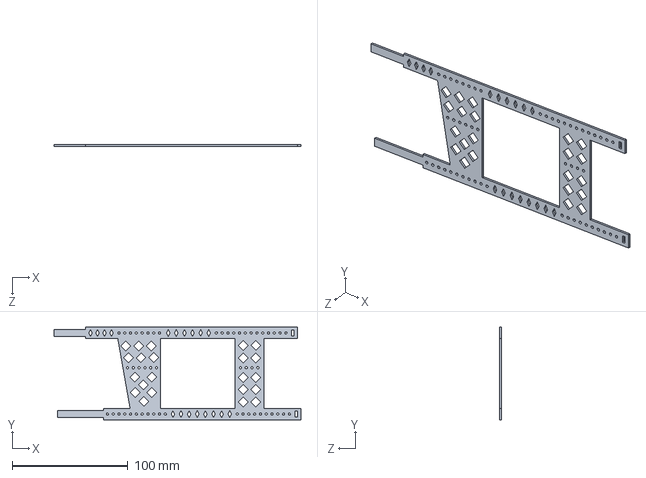
[picture p178: CAD file, 2025-08-06]
SOLIDWORKS 2024/Glove_final_design/palm2.SLDPRT
213.1 x 80.0 x 1.50 mm
