JiajunGuo1027/Soft-Glove-Dissertation/SOLIDWORKS 2024/train.SLDPRT

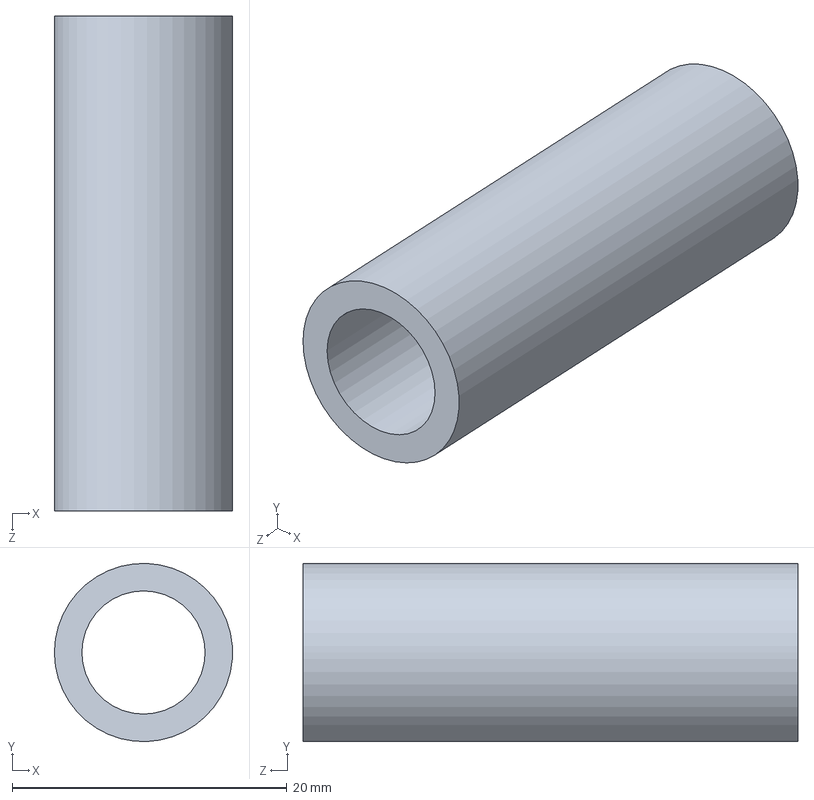
[picture p179: CAD file, 2025-08-06]
SOLIDWORKS 2024/train.SLDPRT
13.0 x 13.0 x 36.0 mm
