JiajunGuo1027/Soft-Glove-Dissertation/SOLIDWORKS 2024/palm1_3D.SLDPRT

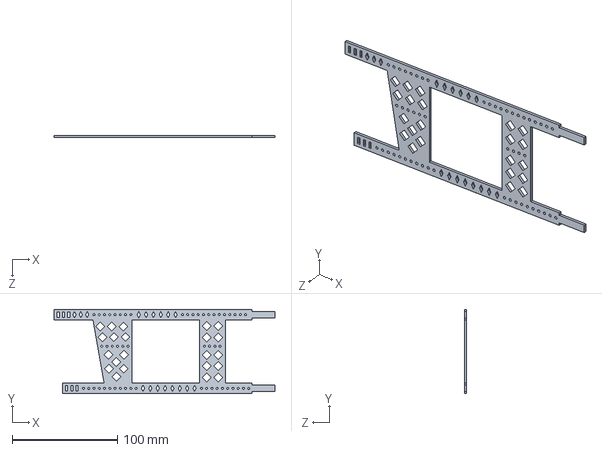
[picture p180: CAD file, 2025-08-06]
SOLIDWORKS 2024/palm1_3D.SLDPRT
210.0 x 80.0 x 2.00 mm
