JiajunGuo1027/Soft-Glove-Dissertation/SOLIDWORKS 2024/finger_upper_3D.SLDPRT

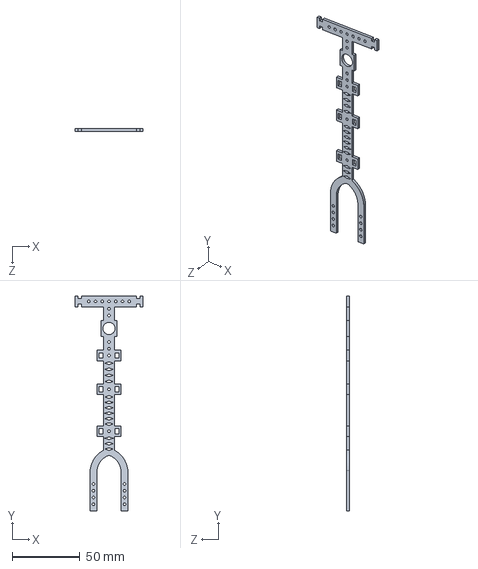
[picture p181: CAD file, 2025-08-06]
SOLIDWORKS 2024/finger_upper_3D.SLDPRT
50.0 x 159.0 x 2.00 mm
