JiajunGuo1027/Soft-Glove-Dissertation/data/raw/test/1/motor_2_log.csv

Time(ms) | MotorID | Phase | Direction | Position | Angle(deg)
53301 | 2 | Flex | >> | -471 | -31.74
53403 | 2 | Flex | >> | -531 | -37.1
53506 | 2 | Flex | >> | -591 | -42.29
53608 | 2 | Flex | >> | -651 | -47.47
53711 | 2 | Flex | >> | -711 | -52.75
53814 | 2 | Flex | >> | -771 | -58.02
53916 | 2 | Flex | >> | -831 | -63.38
54019 | 2 | Flex | >> | -891 | -68.84
54121 | 2 | Flex | >> | -951 | -74.11
54223 | 2 | Flex | >> | -1011 | -79.47
54326 | 2 | Flex | >> | -1071 | -84.84
54429 | 2 | Flex | >> | -1131 | -90.2
54531 | 2 | Flex | >> | -1191 | -95.47
54634 | 2 | Flex | >> | -1251 | -100.75
54736 | 2 | Flex | >> | -1311 | -106.02
54839 | 2 | Flex | >> | -1371 | -111.3
54942 | 2 | Flex | >> | -1431 | -116.57
55044 | 2 | Flex | >> | -1491 | -121.85
55146 | 2 | Flex | >> | -1551 | -127.12
55249 | 2 | Flex | >> | -1611 | -132.31
55352 | 2 | Flex | >> | -1671 | -137.49
55454 | 2 | Flex | >> | -1731 | -142.51
55556 | 2 | Flex | >> | -1791 | -147.52
55658 | 2 | Flex | >> | -1851 | -152.7
55761 | 2 | Flex | >> | -1911 | -157.8
55863 | 2 | Flex | >> | -1971 | -162.9
55966 | 2 | Flex | >> | -2031 | -167.91
56068 | 2 | Flex | >> | -2091 | -173.19
56171 | 2 | Flex | >> | -2151 | -178.2
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
