JiajunGuo1027/Soft-Glove-Dissertation/data/raw/test/1/motor_3_log.csv

Time(ms) | MotorID | Phase | Direction | Position | Angle(deg)
53210 | 3 | Flex | >> | -1542 | -126.24
53313 | 3 | Flex | >> | -1605 | -131.78
53415 | 3 | Flex | >> | -1668 | -137.32
53518 | 3 | Flex | >> | -1731 | -142.95
53621 | 3 | Flex | >> | -1794 | -148.48
53724 | 3 | Flex | >> | -1857 | -154.02
53826 | 3 | Flex | >> | -1920 | -159.47
53928 | 3 | Flex | >> | -1983 | -165.1
54031 | 3 | Flex | >> | -2046 | -170.73
54133 | 3 | Flex | >> | -2109 | -176.26
54235 | 3 | Flex | >> | -2172 | -181.89
54338 | 3 | Flex | >> | -2235 | -187.25
54441 | 3 | Flex | >> | -2298 | -192.79
54543 | 3 | Flex | >> | -2361 | -198.24
54646 | 3 | Flex | >> | -2424 | -203.78
54748 | 3 | Flex | >> | -2487 | -209.41
54851 | 3 | Flex | >> | -2550 | -215.12
54954 | 3 | Flex | >> | -2613 | -220.66
55056 | 3 | Flex | >> | -2676 | -226.11
55159 | 3 | Flex | >> | -2739 | -231.65
55261 | 3 | Flex | >> | -2802 | -237.19
55364 | 3 | Flex | >> | -2865 | -242.55
55466 | 3 | Flex | >> | -2928 | -247.91
55568 | 3 | Flex | >> | -2991 | -253.36
55671 | 3 | Flex | >> | -3054 | -258.64
55773 | 3 | Flex | >> | -3117 | -264.0
55875 | 3 | Flex | >> | -3180 | -269.27
55978 | 3 | Flex | >> | -3243 | -274.73
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
