JiajunGuo1027/Soft-Glove-Dissertation/data/raw/test/1/motor_4_log.csv

Time(ms) | MotorID | Phase | Direction | Position | Angle(deg)
64186 | 4 | Extend | >> | 1482 | 130.29
64288 | 4 | Extend | >> | 1444 | 130.29
64391 | 4 | Extend | >> | 1406 | 128.09
64493 | 4 | Extend | >> | 1368 | 124.92
64595 | 4 | Extend | >> | 1330 | 121.58
64697 | 4 | Extend | >> | 1292 | 118.42
64799 | 4 | Extend | >> | 1254 | 115.16
64901 | 4 | Extend | >> | 1216 | 111.91
65003 | 4 | Extend | >> | 1178 | 108.57
65106 | 4 | Extend | >> | 1140 | 105.14
65208 | 4 | Extend | >> | 1102 | 101.8
65310 | 4 | Extend | >> | 1064 | 98.64
65412 | 4 | Extend | >> | 1026 | 95.12
65515 | 4 | Extend | >> | 988 | 91.78
65617 | 4 | Extend | >> | 950 | 88.53
65719 | 4 | Extend | >> | 912 | 85.27
65821 | 4 | Extend | >> | 874 | 82.02
65924 | 4 | Extend | >> | 836 | 78.68
66026 | 4 | Extend | >> | 798 | 75.43
66128 | 4 | Extend | >> | 760 | 72.18
66230 | 4 | Extend | >> | 722 | 69.01
66332 | 4 | Extend | >> | 684 | 65.76
66434 | 4 | Extend | >> | 646 | 62.59
66537 | 4 | Extend | >> | 608 | 59.43
66639 | 4 | Extend | >> | 570 | 56.26
66741 | 4 | Extend | >> | 532 | 53.1
66843 | 4 | Extend | >> | 494 | 49.67
66946 | 4 | Extend | >> | 456 | 46.42
67048 | 4 | Extend | >> | 418 | 43.08
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
