JiajunGuo1027/Soft-Glove-Dissertation/data/raw/test/1/motor_5_log.csv

Time(ms) | MotorID | Phase | Direction | Position | Angle(deg)
64198 | 5 | Extend | >> | 200 | 17.58
64301 | 5 | Extend | >> | 163 | 17.58
64403 | 5 | Extend | >> | 126 | 15.47
64505 | 5 | Extend | >> | 89 | 12.48
64607 | 5 | Extend | >> | 52 | 9.23
64709 | 5 | Extend | >> | 15 | 6.15
64811 | 5 | Extend | >> | -22 | 2.99
64913 | 5 | Extend | >> | -59 | -0.35
65015 | 5 | Extend | >> | -96 | -3.6
65118 | 5 | Extend | >> | -133 | -6.86
65220 | 5 | Extend | >> | -170 | -10.2
65322 | 5 | Extend | >> | -207 | -13.45
65424 | 5 | Extend | >> | -244 | -16.7
65527 | 5 | Extend | >> | -281 | -19.78
65629 | 5 | Extend | >> | -318 | -22.95
65731 | 5 | Extend | >> | -355 | -26.46
65833 | 5 | Extend | >> | -392 | -29.63
65936 | 5 | Extend | >> | -429 | -32.97
66038 | 5 | Extend | >> | -466 | -36.13
66140 | 5 | Extend | >> | -503 | -39.47
66242 | 5 | Extend | >> | -540 | -42.46
66344 | 5 | Extend | >> | -577 | -45.45
66446 | 5 | Extend | >> | -614 | -48.62
66548 | 5 | Extend | >> | -651 | -51.96
66651 | 5 | Extend | >> | -688 | -55.03
66753 | 5 | Extend | >> | -725 | -58.29
66855 | 5 | Extend | >> | -762 | -61.54
66958 | 5 | Extend | >> | -799 | -64.97
67060 | 5 | Extend | >> | -836 | -68.31
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
