JiajunGuo1027/Soft-Glove-Dissertation/data/raw/test/1/motor_6_log.csv

Time(ms) | MotorID | Phase | Direction | Position | Angle(deg)
64210 | 6 | Extend | >> | 1087 | 95.56
64313 | 6 | Extend | >> | 1045 | 95.56
64415 | 6 | Extend | >> | 1003 | 93.54
64517 | 6 | Extend | >> | 961 | 89.93
64619 | 6 | Extend | >> | 919 | 86.24
64721 | 6 | Extend | >> | 877 | 82.55
64823 | 6 | Extend | >> | 835 | 78.86
64925 | 6 | Extend | >> | 793 | 75.16
65028 | 6 | Extend | >> | 751 | 71.47
65130 | 6 | Extend | >> | 709 | 67.78
65232 | 6 | Extend | >> | 667 | 64.26
65334 | 6 | Extend | >> | 625 | 60.4
65437 | 6 | Extend | >> | 583 | 56.79
65539 | 6 | Extend | >> | 541 | 53.27
65641 | 6 | Extend | >> | 499 | 49.76
65743 | 6 | Extend | >> | 457 | 46.15
65846 | 6 | Extend | >> | 415 | 42.64
65948 | 6 | Extend | >> | 373 | 39.21
66050 | 6 | Extend | >> | 331 | 35.78
66152 | 6 | Extend | >> | 289 | 32.26
66254 | 6 | Extend | >> | 247 | 28.75
66356 | 6 | Extend | >> | 205 | 25.23
66459 | 6 | Extend | >> | 163 | 22.07
66561 | 6 | Extend | >> | 121 | 18.73
66663 | 6 | Extend | >> | 79 | 15.21
66765 | 6 | Extend | >> | 37 | 11.08
66867 | 6 | Extend | >> | -5 | 6.77
66970 | 6 | Extend | >> | -47 | 2.73
67073 | 6 | Extend | >> | -89 | -0.97
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
