JiajunGuo1027/Soft-Glove-Dissertation/data/raw/test/1/Figure_1.png

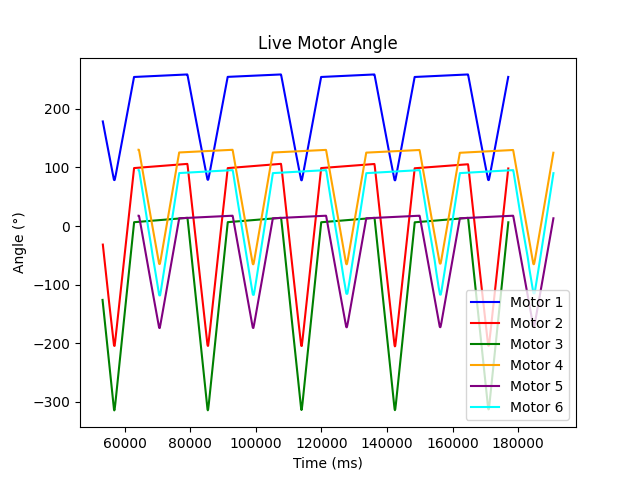
data/raw/test/1/Figure_1.png
