JiajunGuo1027/Soft-Glove-Dissertation/data/raw/test/2_vido/Figure_2.png

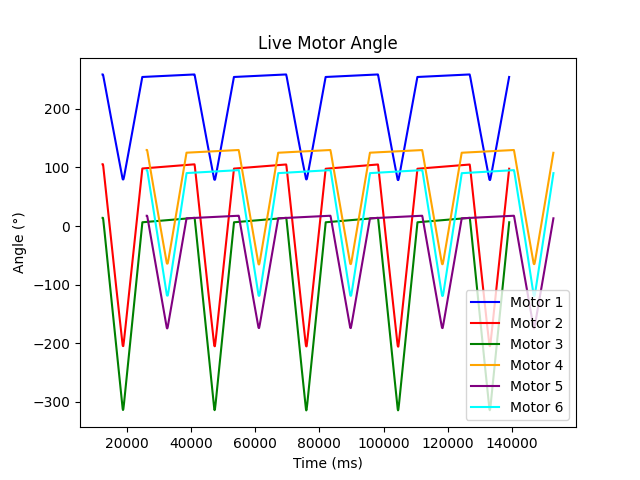
data/raw/test/2_vido/Figure_2.png
