JiajunGuo1027/Soft-Glove-Dissertation/images/article/tensile_test.jpg

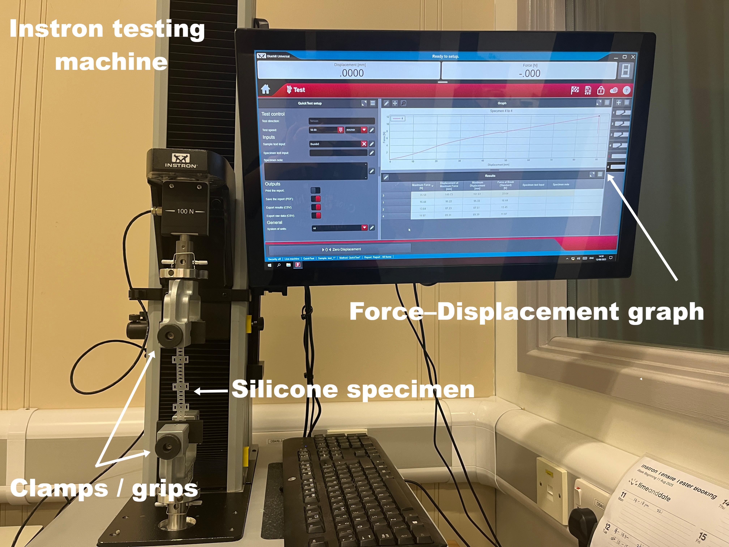
images/article/tensile_test.jpg
