JiajunGuo1027/Soft-Glove-Dissertation/images/soft_glove_test/IMG_20250731_200817.jpg

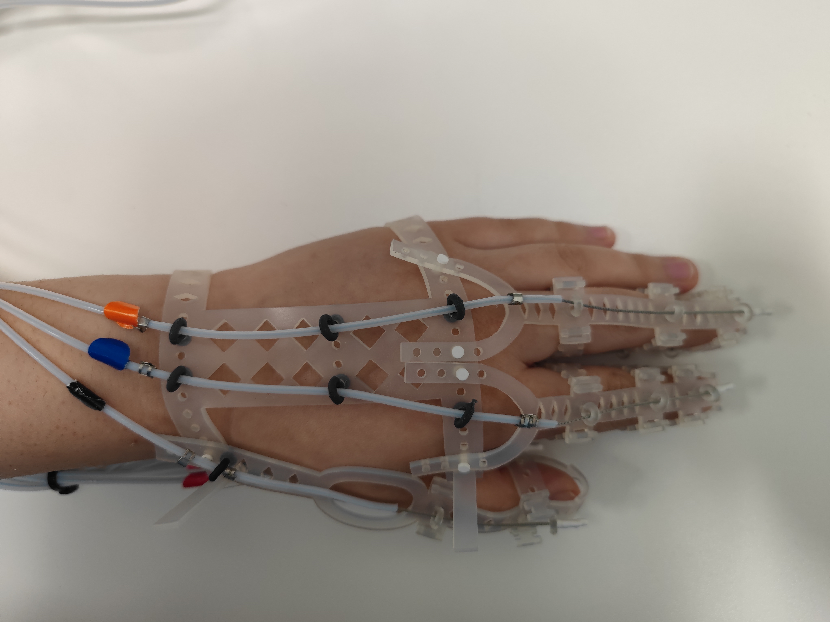
images/soft_glove_test/IMG_20250731_200817.jpg
