JiajunGuo1027/Soft-Glove-Dissertation/images/soft_glove_test/IMG_20250731_201116.jpg

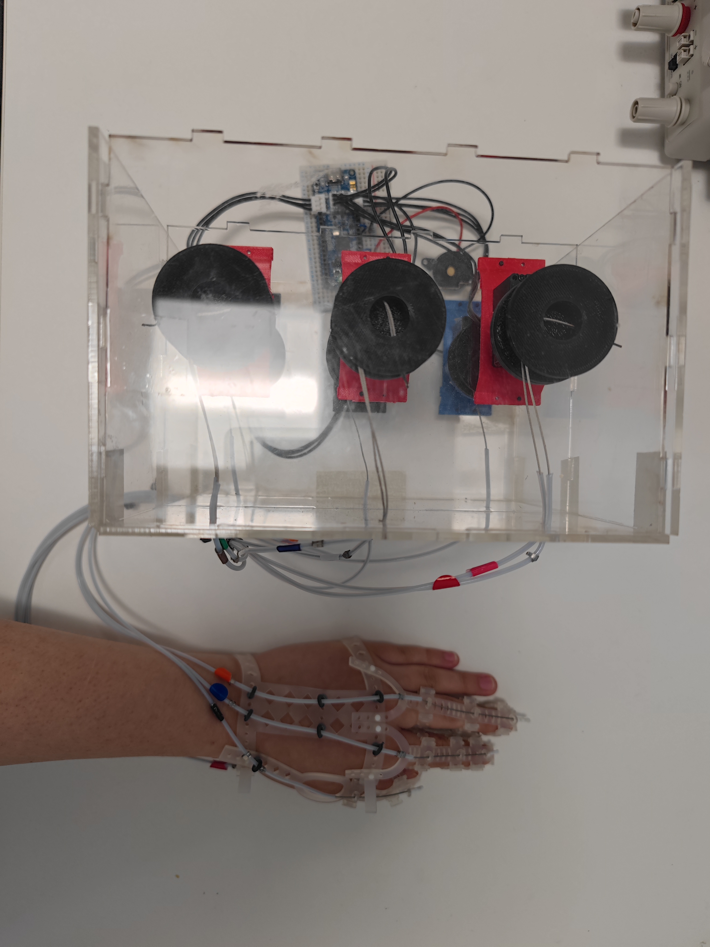
images/soft_glove_test/IMG_20250731_201116.jpg
