JiajunGuo1027/Soft-Glove-Dissertation/images/soft_glove_test/IMG_20250812_173648.jpg

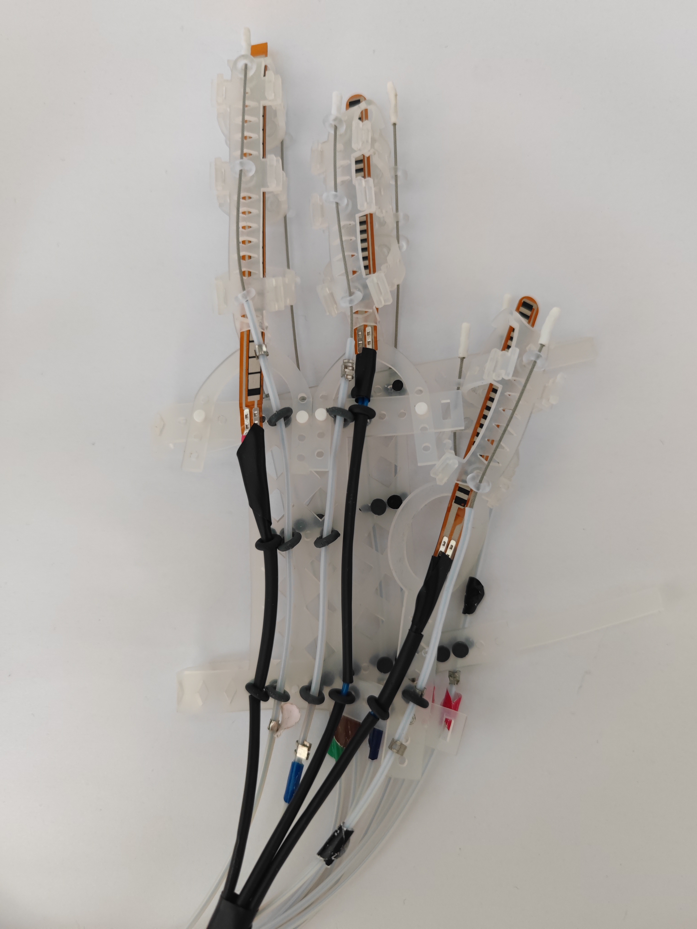
images/soft_glove_test/IMG_20250812_173648.jpg
