JiajunGuo1027/Soft-Glove-Dissertation/images/soft_glove_test/test1.jpg

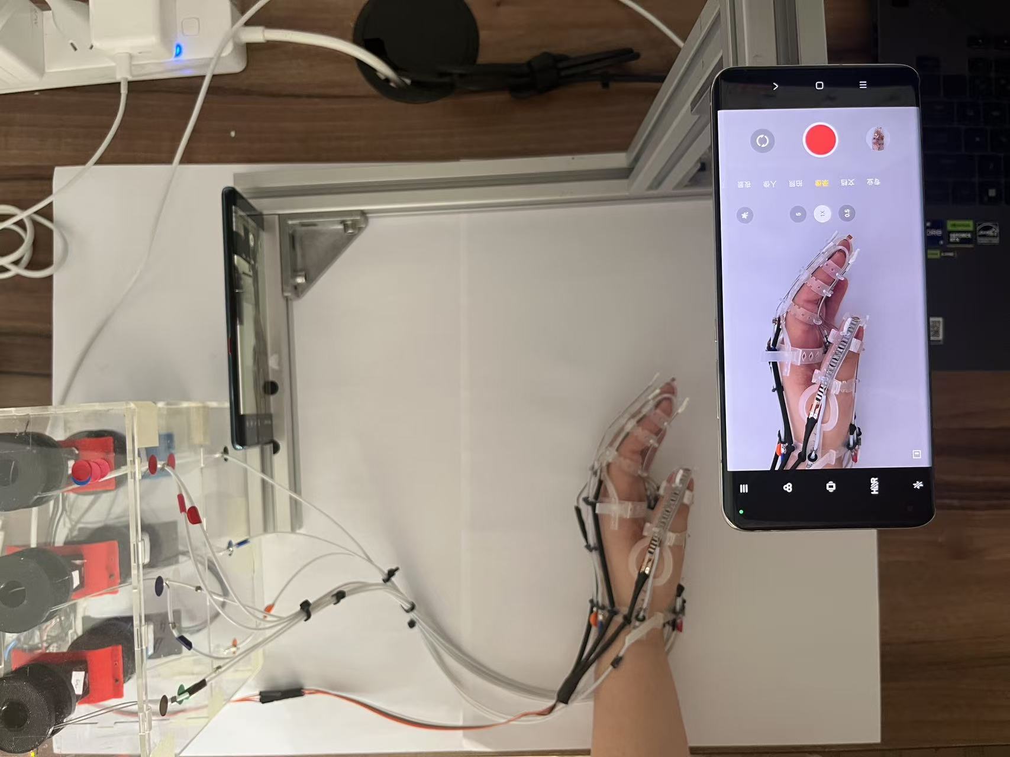
images/soft_glove_test/test1.jpg
