JiajunGuo1027/Soft-Glove-Dissertation/images/soft_glove_test/test3.jpg

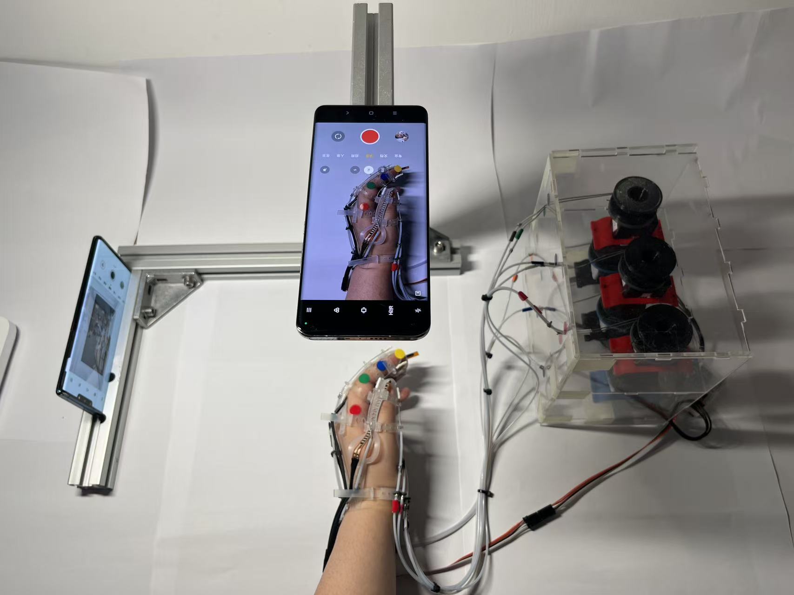
images/soft_glove_test/test3.jpg
