JiajunGuo1027/Soft-Glove-Dissertation/output/control_results/error_Index.png

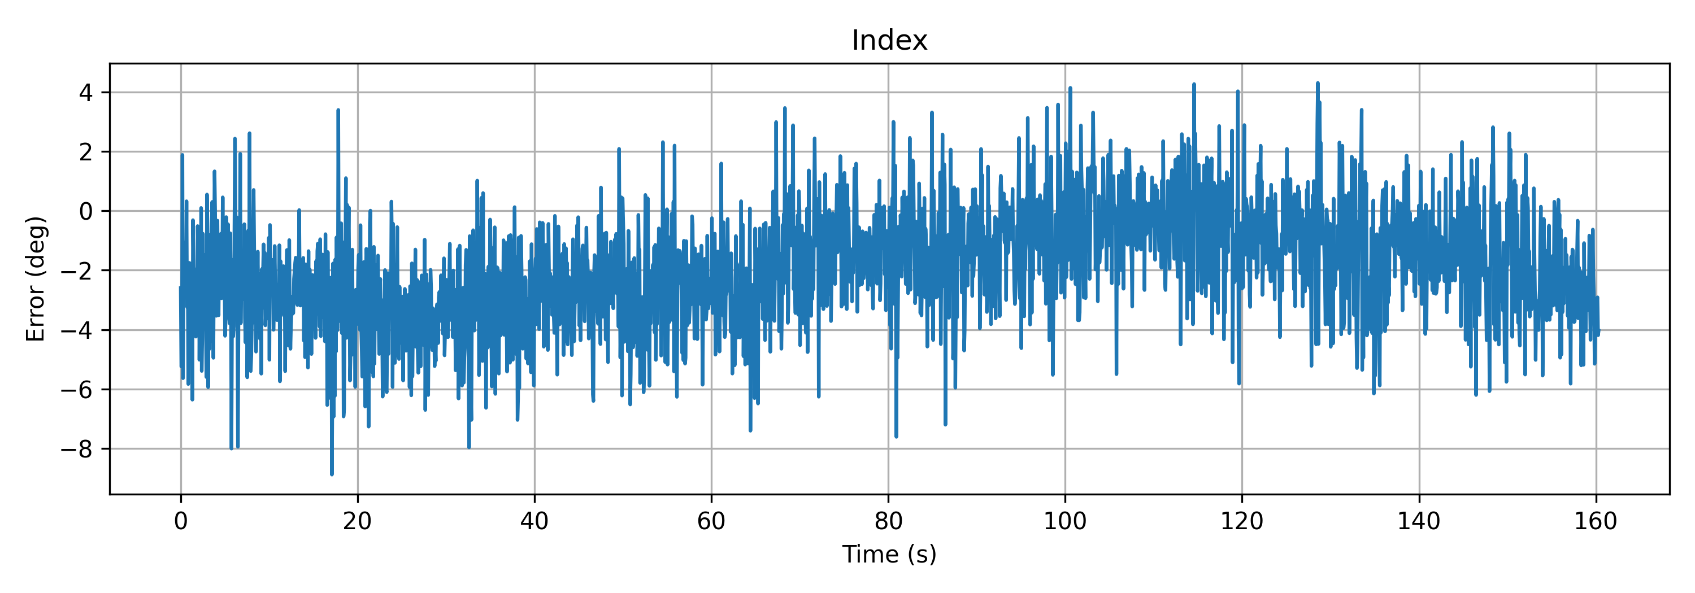
output/control_results/error_Index.png
