JiajunGuo1027/Soft-Glove-Dissertation/output/control_results/error_Middle.png

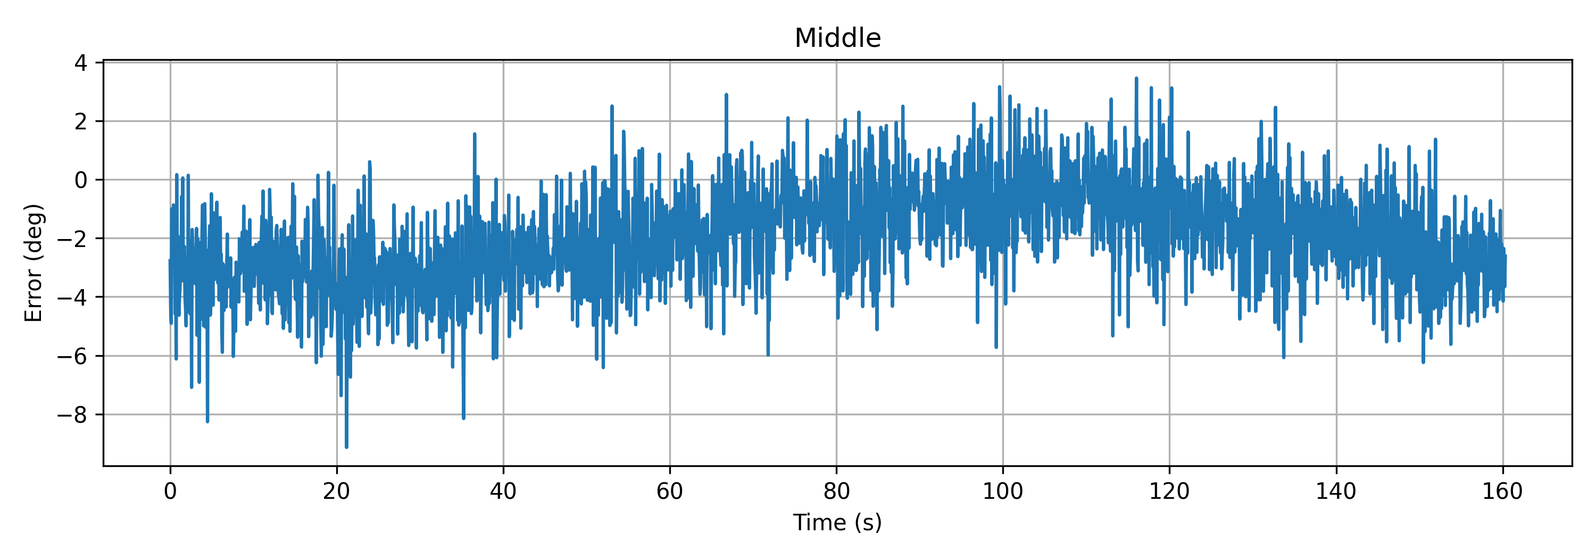
output/control_results/error_Middle.png
