JiajunGuo1027/Soft-Glove-Dissertation/output/control_results/error_Thumb.png

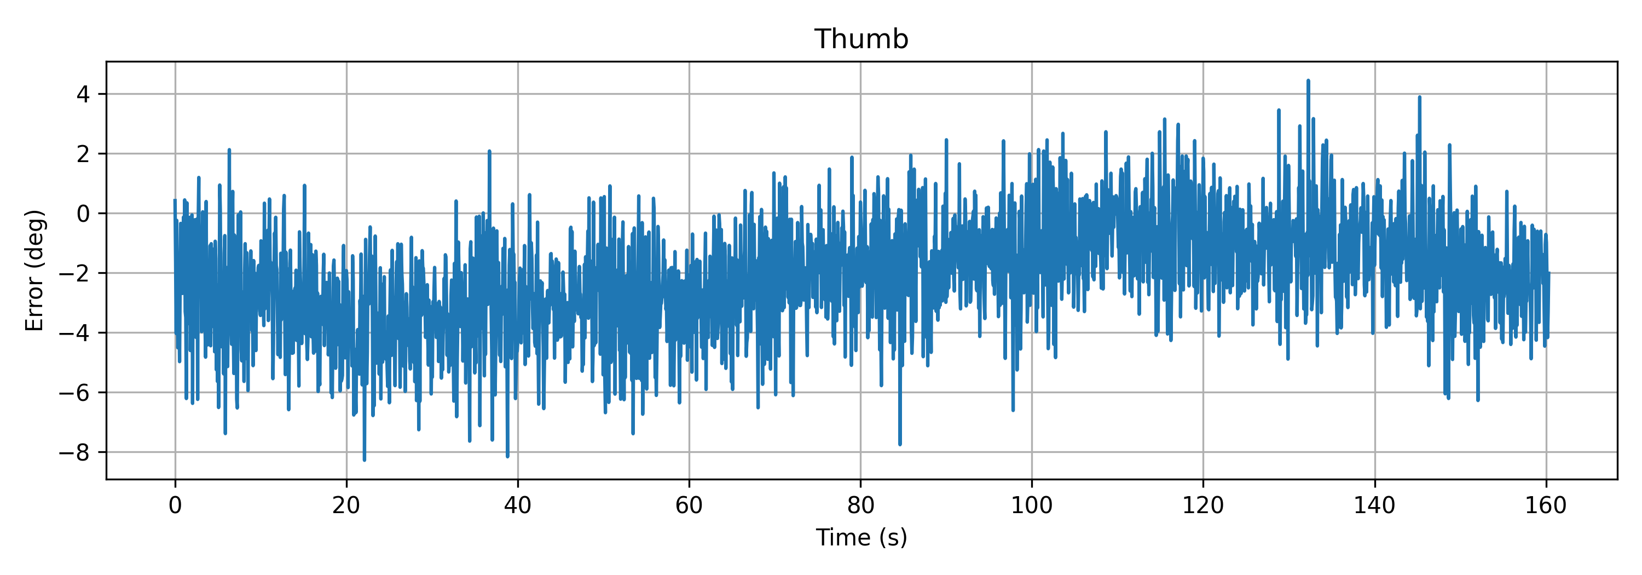
output/control_results/error_Thumb.png
