JiajunGuo1027/Soft-Glove-Dissertation/output/control_results/fig_error_violin.png

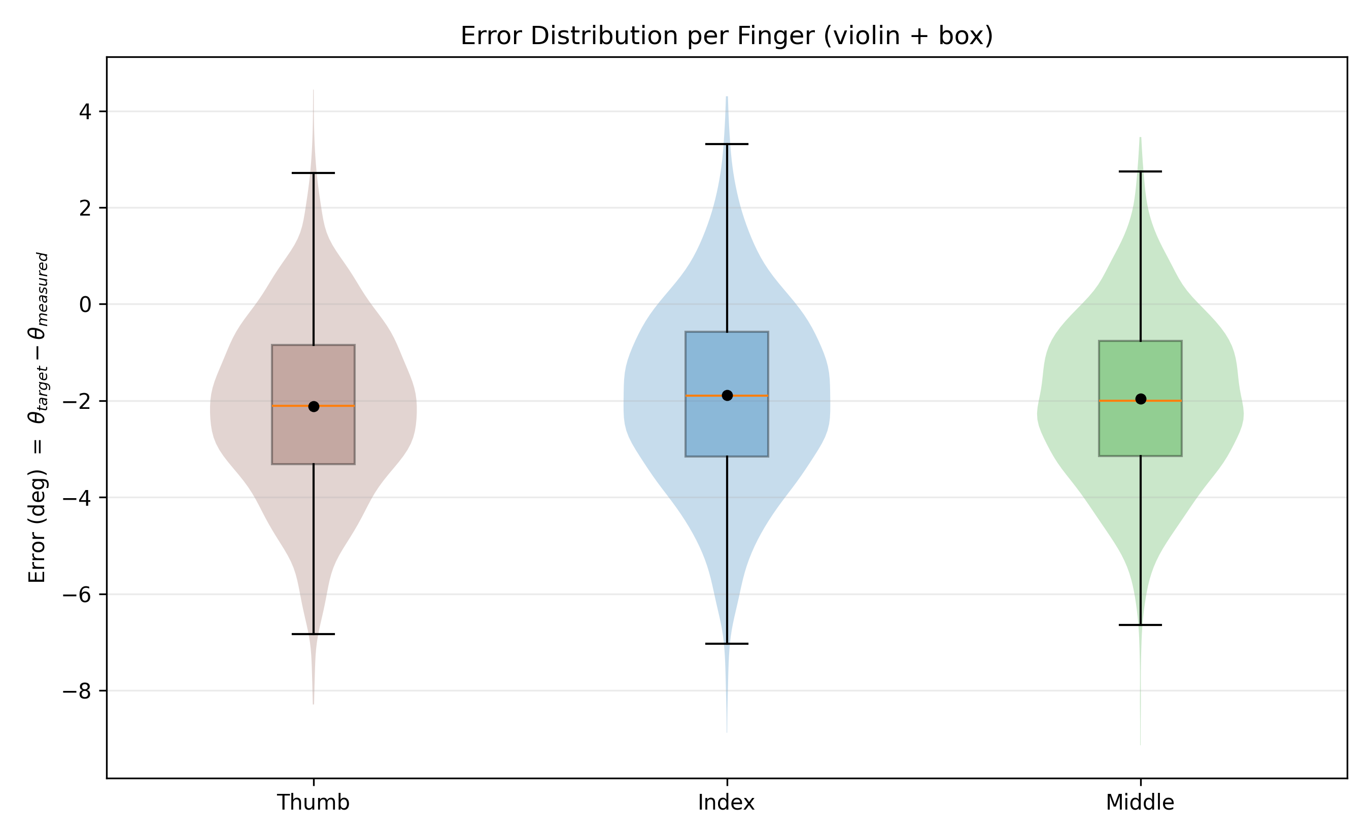
output/control_results/fig_error_violin.png
