JiajunGuo1027/Soft-Glove-Dissertation/output/control_results/fig_meas_vs_target.png

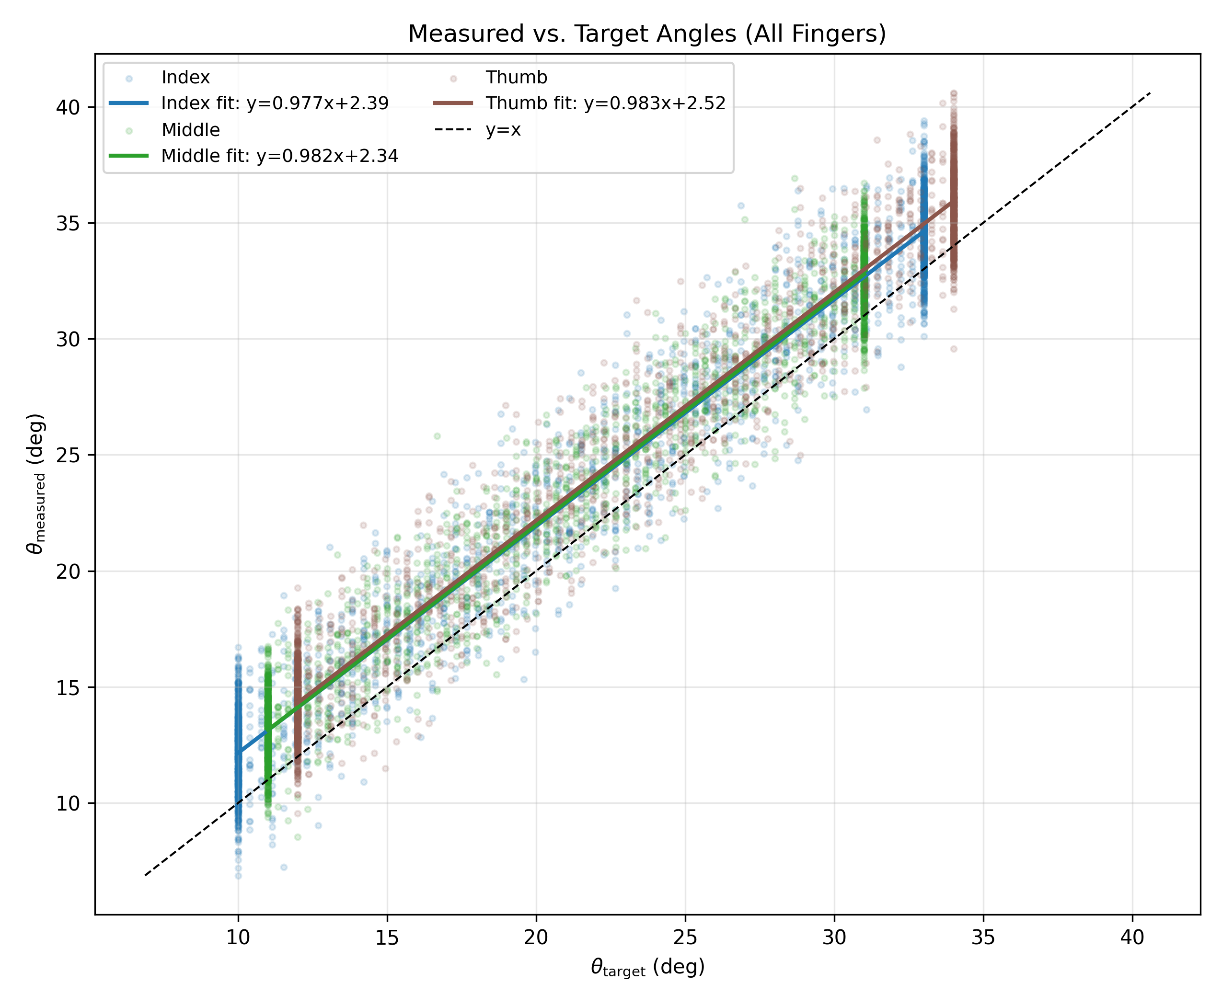
output/control_results/fig_meas_vs_target.png
