JiajunGuo1027/Soft-Glove-Dissertation/output/control_results/result.png

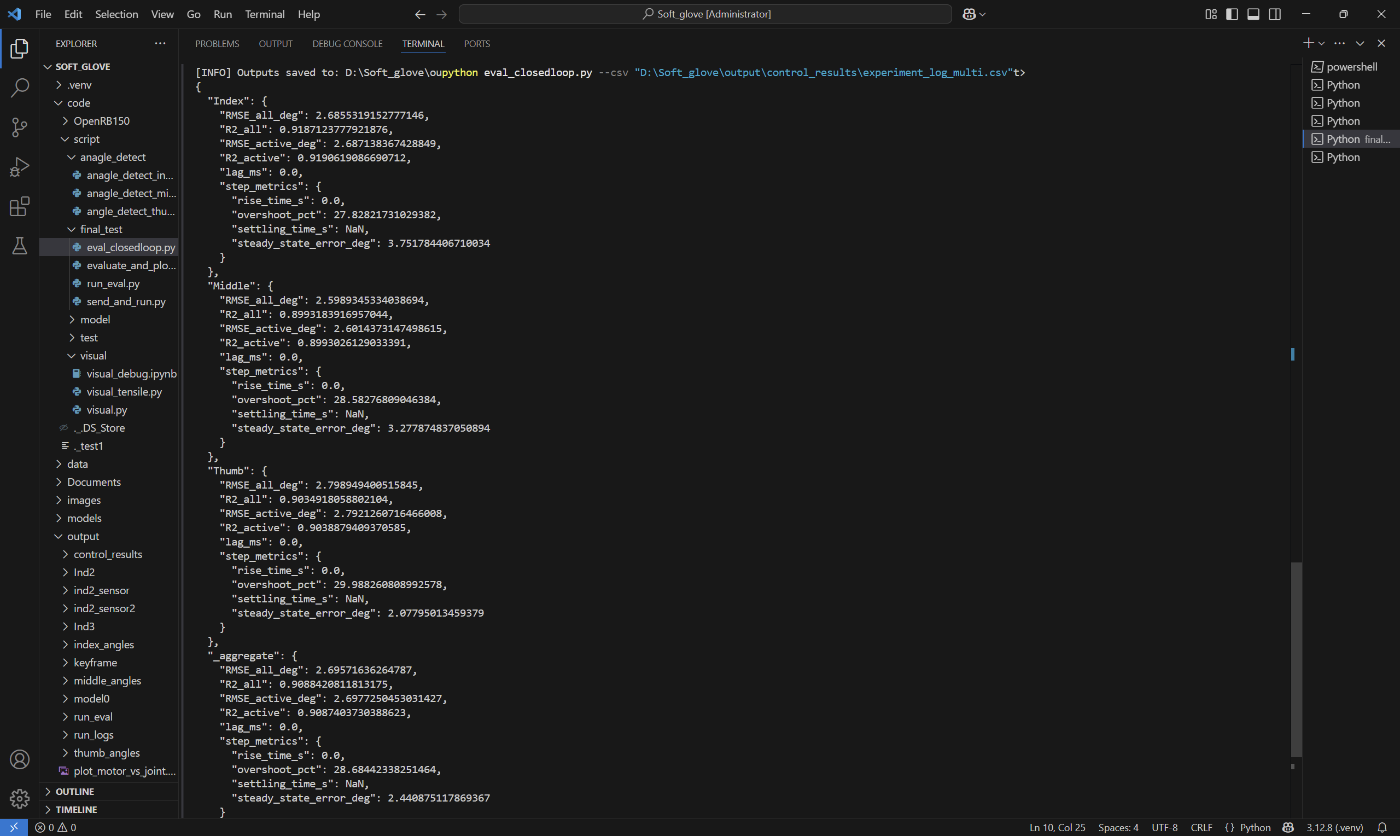
output/control_results/result.png
