JiajunGuo1027/Soft-Glove-Dissertation/output/control_results/summary.png

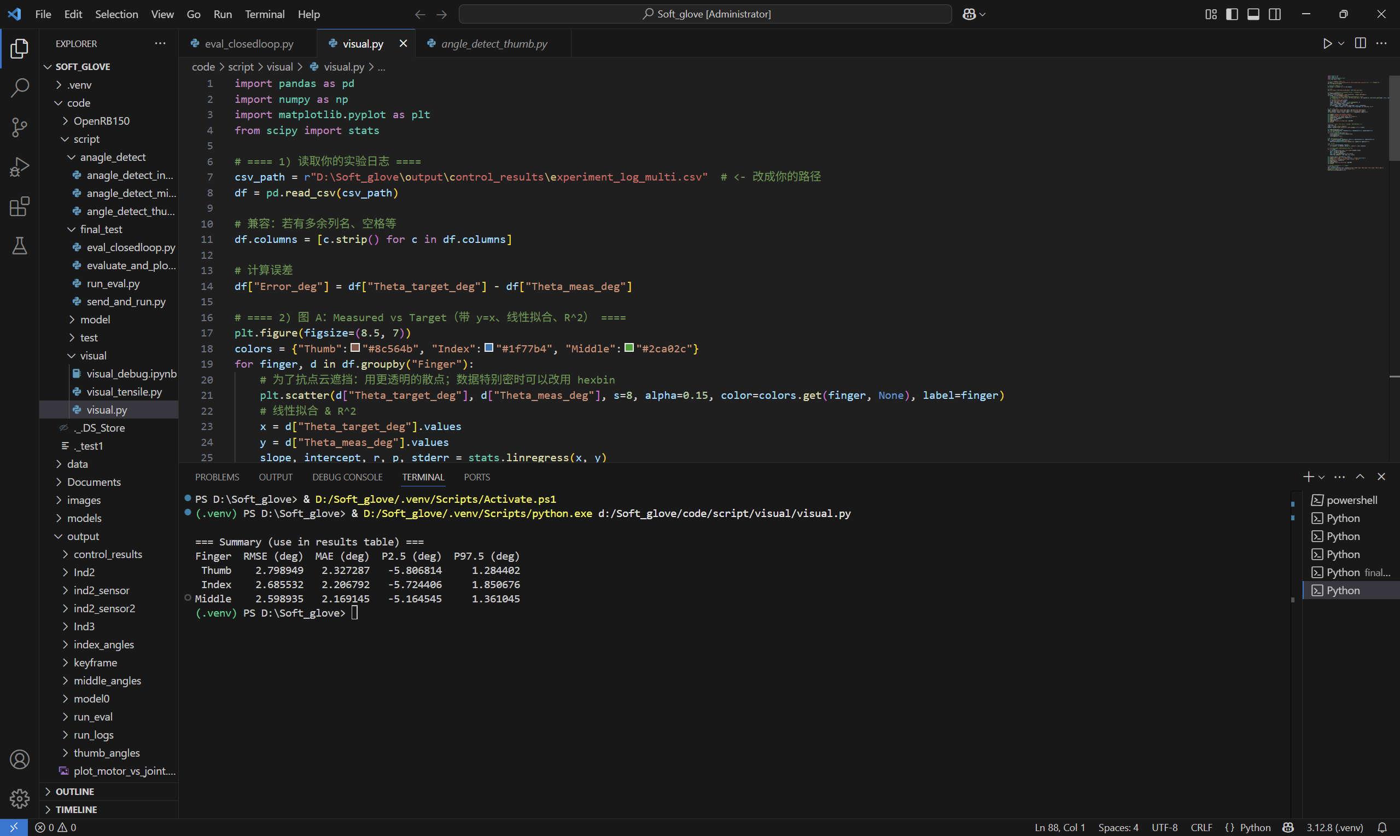
output/control_results/summary.png
