JiajunGuo1027/Soft-Glove-Dissertation/output/control_results/timeseries_Index.png

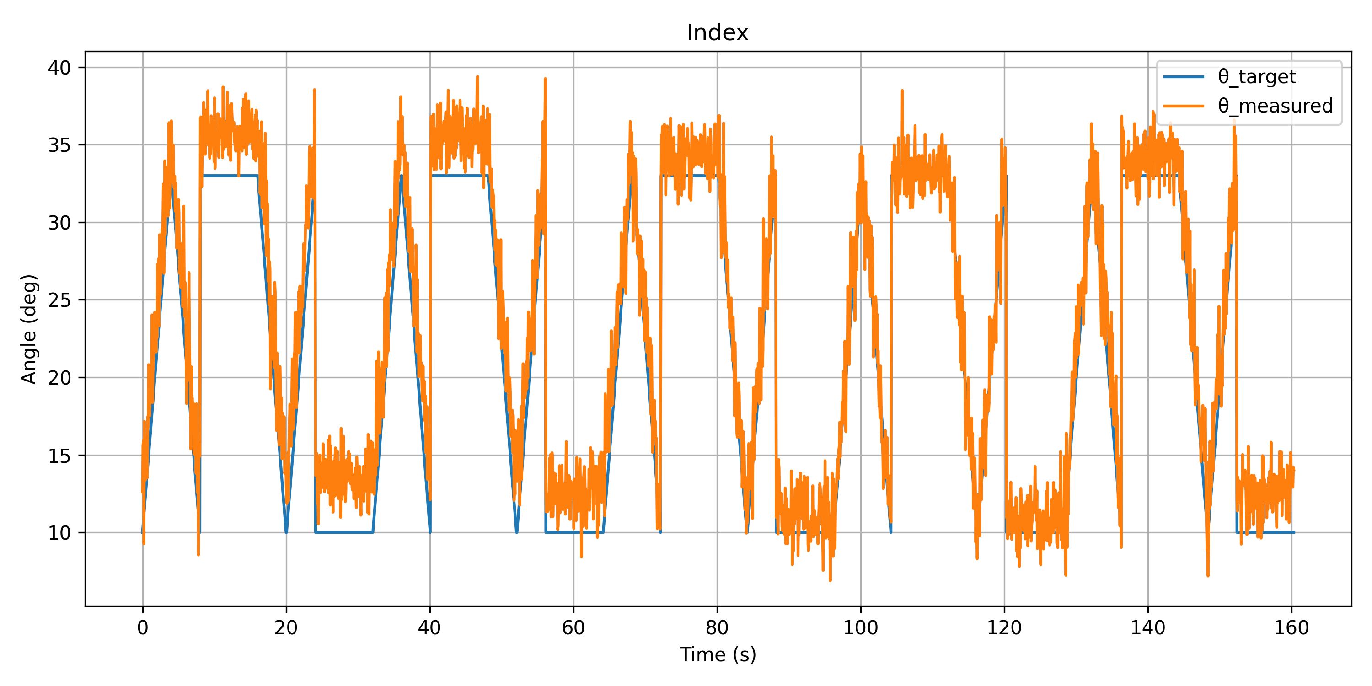
output/control_results/timeseries_Index.png
