JiajunGuo1027/Soft-Glove-Dissertation/output/control_results/timeseries_Middle.png

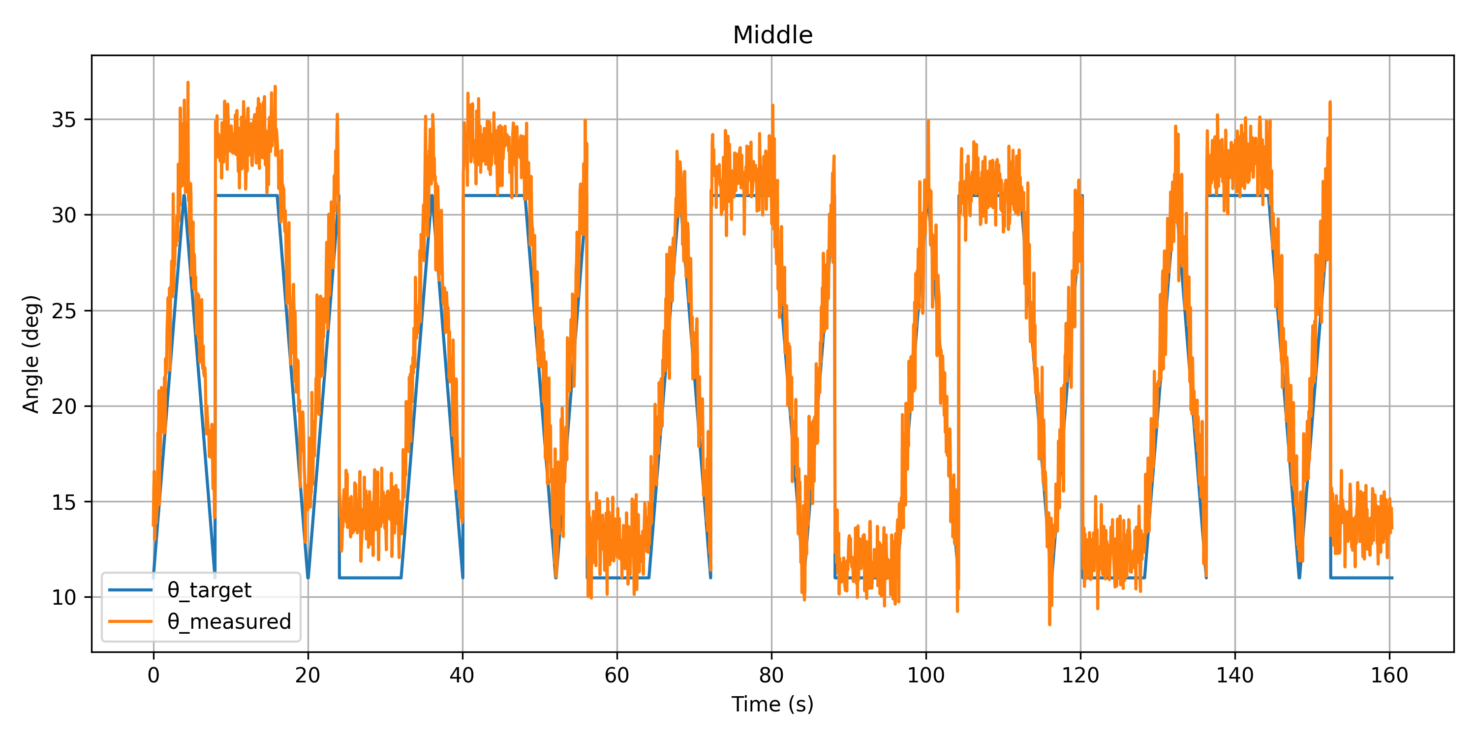
output/control_results/timeseries_Middle.png
